nrzimmer/retro-crt/tv/circuits/voltage_waveform_table.md

# Tabela de Tensões e Formas de Onda — A Board

**Fonte:** páginas 47–48 do manual | **Condição:** TV em operação normal, sinal NTSC salvo indicação

> Valores marcados com `*` = sinal (não tensão DC).

## IC001 — TDA12009H (128 pinos)

### Pinos 1–48

| Pino | Sinal | Tensão (V) |
|---|---|---|
| 1 | — | 0 |
| 2 | — | 0 |
| 3 | — | 1.2 |
| 4 | — | 2.6 |
| 5 | — | 3.2 |
| 6 | — | 0 |
| 7 | — | 3.2 |
| 8 | — | 0 |
| 9 | — | 3.1 |
| 10 | — | * |
| 11 | — | * |
| 12 | — | 0 |
| 13 | VGUARD | 0.1 |
| 14 | PH2LF | 2.4 |
| 15 | PH1LF | 4.8 |
| 16 | — | 1.9 |
| 17 | — | 2.1 |
| 18 | — | 0 |
| 19 | — | 2.2 |
| 20 | — | 2.2 |
| 21 | EWD | 3.2 |
| 22 | VD+ | 1.6 |
| 23 | VD− | 1.7 |
| 24 | VIFIN1 | 1.8 |
| 25 | VIFIN2 | 1.5 |
| 26 | — | 2.3 |
| 27 | — | 1.8 |
| 28 | — | 0 |
| 29 | SIFIN1 | 1.8 |
| 30 | SIFIN2 | 1.8 |
| 31 | AGCOUT | 4.6 |
| 32 | EHTO | 0.7 |
| 33 | — | 0 |
| 34 | — | 2.1 |
| 35 | — | 2.1 |
| 36 | OUTL | 3.4 |
| 37 | OUTR | 3.4 |
| 38 | — | 2.0 |
| 39 | MONO_OUTL | 2.4 |
| 40 | — | 0 |
| 41 | PLLIF | 1.8 |
| 42 | — | 2.0 |
| 43 | IFVO | 0.3 |
| 44 | — | 0.3 |
| 45 | VCC8V | 8.3 |
| 46 | — | 1.8 |
| 47 | — | 4.8 |
| 48 | — | 1.1 |

### Pinos 49–87 (entradas de vídeo e saídas RGB)

| Pino | Sinal | Tensão (V) |
|---|---|---|
| 49 | — | 2.1 |
| 50 | — | 2.1 |
| 51 | CVBS2/Y2 | 1.3 |
| 52 | C2 | 1.5 |
| 53 | — | 2.1 |
| 54 | — | 2.1 |
| 55 | CVBS3 | 1.4 |
| 56 | — | 2.1 |
| 57 | — | 2.1 |
| 58 | CVBS1/Y1 | 1.3 |
| 59 | C1 | 1.5 |
| 60 | — | 3.4 |
| 61 | — | 3.4 |
| 62 | — | 3.4 |
| 63 | — | 3.4 |
| 64 | CVBSO | 1.1 |
| 65 | VM | 0.2 |
| 66 | AFC | 0 |
| 67 | HOUT | 4.7 |
| 68 | — | 1.2 |
| 69 | — | 1.2 |
| 70 | — | 1.2 |
| 71 | — | 1.9 |
| 72 | — | 1.6 |
| 73 | — | 0.1 |
| 74 | — | 0 |
| 75 | — | 0.1 |
| 76 | — | 1.1 |
| 77 | — | 1.2 |
| 78 | — | 1.2 |
| 79 | — | 0 |
| 80 | — | 4.7 |
| 81 | — | 3.4 |
| 82 | — | 3.0 |
| 83 | ABL | 1.5 |
| 84 | IK | 1.5 |
| 85 | B OUT | 1.5 |
| 86 | G OUT | 1.4 |
| 87 | R OUT | 1.5 |

### Pinos 88–128 (controle de sistema)

| Pino | Sinal | Tensão (V) |
|---|---|---|
| 88–90 | — | 3.1, 0, 3.1 |
| 91 | — | 1.5 |
| 92 | — | 0 |
| 93 | — | 1.8 |
| 94 | — | 3.1 |
| 95 | — | 0 |
| 96 | — | 1.8 |
| 97 | — | 2.8 |
| 98 | — | 0.3 |
| 99 | — | 3.2 |
| 100 | VDDC2 | 1.6 |
| 101 | VSSC2 | 0 |
| 102 | — | 3.2 |
| 103 | — | 0 |
| 104 | — | 2.2 |
| 105 | — | 0 |
| 106 | — | 0 |
| 107 | — | 3.1 |
| 108 | SCL0 | 3.5 |
| 109 | SDA0 | 3.2 |
| 110 | VDDP (3.3V) | 3.2 |
| 111 | S1/VC | 4.8 |
| 112 | ROT CTRL | 0 |
| 113 | ROT SW | 0 |
| 114 | STBY_SW | 0 |
| 115 | DGC RELAY | 0.1 |
| 116 | — | 1.6 |
| 117 | VDDC1 (1.8V) | 1.6 |
| 118 | — | 3.1 |
| 119 | KEY | 0.2 |
| 120 | S2 | 0 |
| 121 | — | 0 |
| 122 | RED LED | 3.1 |
| 123 | GREEN LED | 1.6 |
| 124 | VDDC3 (1.8V) | 0 |
| 125 | VSSC3 | 3.2 |
| 126 | — | 0.2 |
| 127 | — | 3.2 |
| 128 | — | 3.2 |

---

## Reguladores de tensão

| Ref | Tipo | Pin I (V) | Pin G (V) | Pin O (V) |
|---|---|---|---|---|
| IC602 | KIA78R09API (9V) | 10.4 | 0 | 8.8 |
| IC603 | PQ018EF01SSH (1.8V áudio) | 3.9 | 0 | 1.9 (pin2=3.9, pin3=0, pin4=2.3) |
| IC604 | KIA7805API (5V) | 8.8 | 0 | 4.8 |
| IC605 | SE135N-LF38 (error amp) | 134.4 | 0 | 21.2 |
| IC606 | KIA78D33P1 (3.3V) | 23.6 | 0 | 3.2 |
| IC607 | BA18BC0FP-E2 (1.8V main) | 3.4 | 0 | 1.7 |

---

## IC802 — TJM4558CDT (op-amp EW)

| Pino | Tensão (V) |
|---|---|
| 1 (OUT1) | 3.3 |
| 2 (IN1−) | 2.2 |
| 3 (IN1+) | 6.0 |
| 4 (Vcc) | 8.8 |
| 5 (IN2+) | 2.4 |
| 6 (IN2−) | 3.1 |
| 7 (OUT2) | 3.0 |
| 8 (GND) | 0 |

---

## IC804 — STV9302A (Vertical IC)

| Pino | Sinal | Tensão (V) |
|---|---|---|
| 1 | VSS | −13.5 |
| 2 | IN | pulso |
| 3 | VCC | 13.9 |

---

## IC801 — LM2903DT (Comparador H-center)

| Pino | Tensão (V) |
|---|---|
| 1 | 2.2 |
| 2 | 0.7 |
| 3 | 1.5 |
| 4 | 0 |
| 5–8 | 3.3, 2.2, 6.0, 8.8 |

---

## Transistores — tensões chave

| Ref | Tipo | B (V) | C (V) | E (V) |
|---|---|---|---|---|
| Q001 | UN2211 | 0 | 2.1 | 0 |
| Q006 | UN2216 | 3.2 | 1.9 | 1.9 |
| Q007 | UN2216 | 0 | 3.1 | 0.1 |
| Q008 | 2SC1623 | 0 | 3.3 | 0 |
| Q010 | 2SA1235-F | 0.2 | 0 | 0.9 |
| Q200 | UN2211 | 82.3 | 0 | 0 |
| Q201 | 2SA1235-F | 4.5 | 8.8 | 3.9 |
| Q202 | 2SA1235-F | 1.9 | 0 | 0 |
| Q206 | UN2216 | 23.6 | 24.3 | 24.4 |
| Q803 | 2SC3209LK | 133.4 | 70.6 | 0 |
| Q804 | KTA1279 | 133.8 | 0 | (0) |
| Q805 | 2SC5885 | — | 137.6 (DC) | — |
| Q806 | 2SC1623 | 0 | 4.9 | 9.3 (NTSC: 9.9) |
| Q807 | 2SA1235-F | 1.1 | 0 | 0.1 |
| Q808 | IRF614-037 | G=0.1 | D=0 | S=1.8 |
| Q814 | 2SC1623 | 0 | 6.1 | 8.8 |
| Q900 | 2SA1235-F | 5.8 | 6.1 | 0 |
| Q901 | UN2216 | 5.8 | 0 | 5.6 |

---

## Formas de onda (condição NTSC salvo indicação)

| Ref | Local / sinal | Amplitude (Vpp) |
|---|---|---|
| 1 | — | 1.960 |
| 2 | VD+ drive vertical | 5.360 |
| 3 | VD− drive vertical | 3.440 |
| 4 | — | 1.800 |
| 5 | — | 2.480 |
| 6 | — | 1.120 |
| 7 | — | 1.840 |
| 8 | IC200 (áudio out) | 1.680 |
| 9 | — | 4 NTSC — 2.480 |
| 10 | — | 5 NTSC — varia |
| 11 | — | 660.0 mVpp |
| 12 | Estágio H (IC001 zona) | 132.0 |
| 13 | — | 700.0 mVpp |
| 14 | Saída vertical IC804 | 1.400 |
| 15 | DY800 yoke H | 28.80 |
| 16 | Q806 MIXER EW | 9.200 |
| 17 | Saída vertical (alt) | 1.340 |

---

## Deflection Yoke DY800 — tensões DC nas bobinas

| Pino | Tensão (V) |
|---|---|
| 1 (H.DY+) | 196.0 |
| 2 (H.DY−) | 196.2 |
| 3 (H.DY ref) | 196.6 |
| 4 (V.DY+) | 0.5 |
| 5 (V.DY−) | 0.1 |

---

## IC601 — Controlador SMPS (seleção)

| Pino | Tensão (V) |
|---|---|
| 1 | (12.6) [12.7] |
| 2 | 0 |
| 3 | 23.0 |
| 4–6 | 0, 0, 0 |
| 7 | 11.3 |
| 8 | 0.8 |
| 9 | 0 |
| 10 | 24.2 |
| 11 | 10.2 |
| 12 | 11.3 |
| 13 | 1.4 |
| 14 | 12.4 |
| 15 | 154.9 |
| 16 | 0 |
| 17 | 0.2 |
