nrzimmer/retro-crt/scart/cables/README.md

# Cabos SCART por Console

Pinagens e diagramas de fiação. Voltar para [`scart/README.md`](../README.md) para componentes comuns e avisos.

| Arquivo | Console | Conector | Obs |
|---|---|---|-----|
| [nes.md](nes.md) | NES / Famicom | MultiAV (via NESRGB) | Requer mod — ver [`consoles/nes/`](../../consoles/nes/) |
| [snes.md](snes.md) | Super Nintendo | MultiAV 12P card-edge | RGB nativo (exceto SNES Mini) |
| [n64.md](n64.md) | Nintendo 64 | MultiAV 12P | Requer mod — ver [`consoles/n64/`](../../consoles/n64/) |
| [megadrive.md](megadrive.md) | Sega Mega Drive 1/2 | DIN-8U / mini-DIN 9 | RGB nativo |
| [ps1.md](ps1.md) | PlayStation 1 | Proprietário 12P | RGB nativo |
| [ps2.md](ps2.md) | PlayStation 2 | Proprietário 12P | RGB nativo; atenção ao 480p |
| [saturn.md](saturn.md) | Sega Saturn | mini-DIN 10 | Componentes obrigatórios no sync |
| [neogeo.md](neogeo.md) | SNK Neo Geo AES/MVS | DIN-8C | RGB nativo |
