nrzimmer/retro-crt/consoles/megadrive/README.md

# Sega Mega Drive / Genesis — Mods

---

## Mod Stereo (MD1)

Mega Drive 1 tem apenas saída de áudio mono pelo DIN-8. Para stereo:

**Opção 1 — Jack de fone frontal:**  
MD1 tem jack 3.5mm na frente com stereo — capturar dali em vez do DIN-8.

**Opção 2 — Mod interno:**  
Separar os canais L e R do gerador de som (YM2612 / SN76489) internamente e adicionar conector.

Mega Drive 2 já tem stereo nativo pelo mini-DIN 9 (pinos 8 e 9).

---

## Referências

- [Genesis Stereo Audio Mod — RetroRGB](https://retrorgb.com/genesisaudio.html)
