nrzimmer/retro-crt/tv/manual/rev_brazil/pages/page-18.md

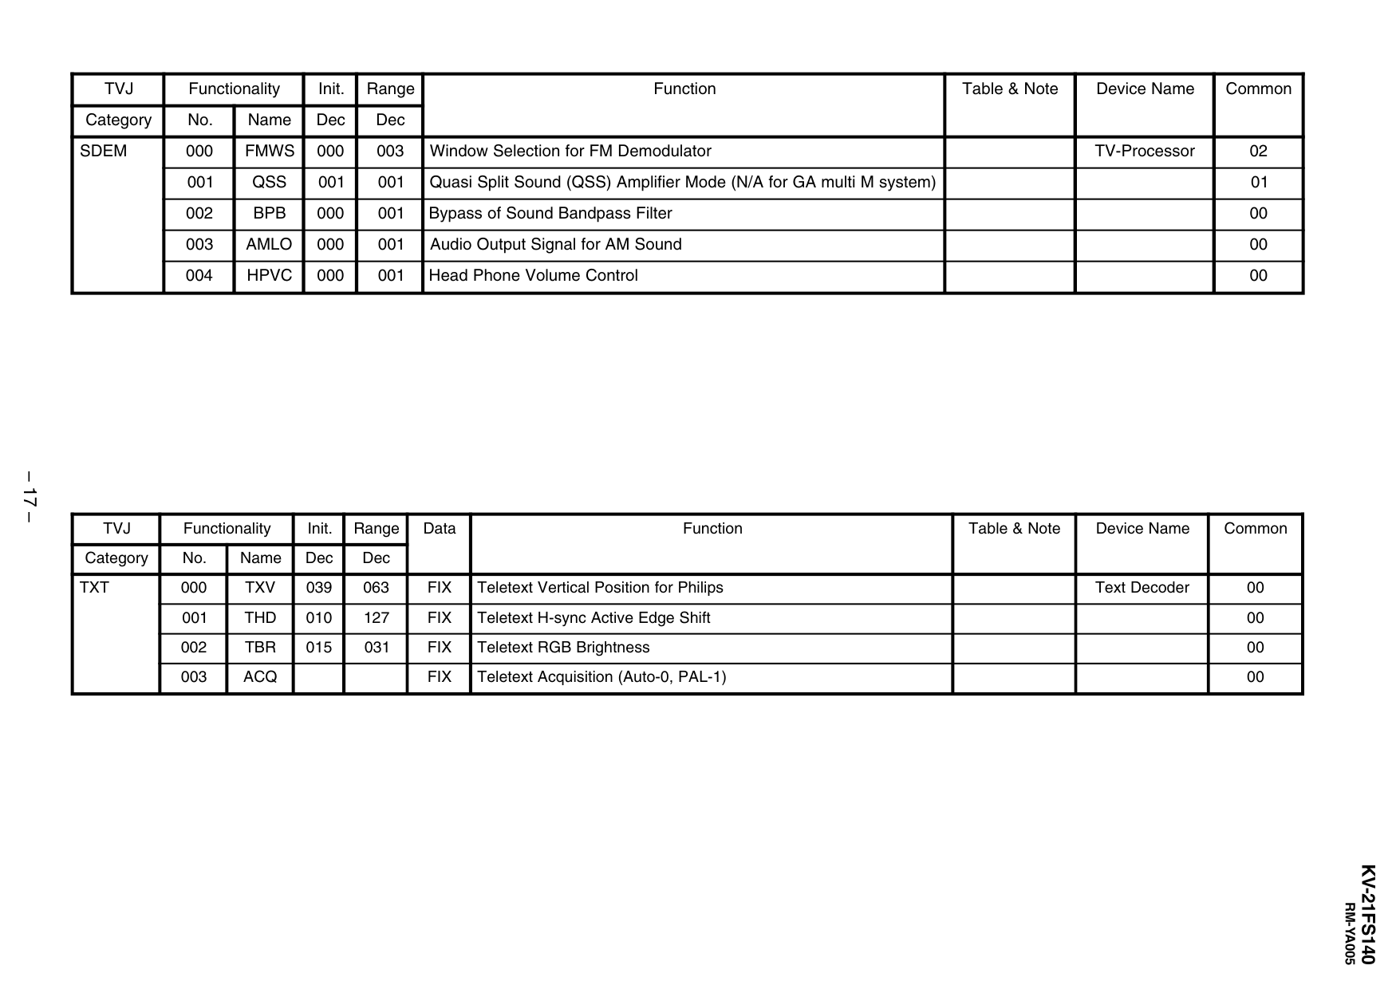
[picture p14: tv/manual/rev_brazil/pages/img/page-18.png]
page-18


TVJ

Functionality

Init.

Range

Category

No.

Name

Dec

Dec

SDEM

000

FMWS

000

003

Window Selection for FM Demodulator

001

QSS

001

001

Quasi Split Sound (QSS) Amplifier Mode (N/A for GA multi M system)

01

002

BPB

000

001

Bypass of Sound Bandpass Filter

00

003

AMLO

000

001

Audio Output Signal for AM Sound

00

004

HPVC

000

001

Head Phone Volume Control

00

Function

Table & Note

Device Name

Common

TV-Processor

02

– 17 –
TVJ

Functionality

Init.

Range

Category

No.

Name

Dec

Dec

TXT

000

TXV

039

063

FIX

Teletext Vertical Position for Philips

001

THD

010

127

FIX

Teletext H-sync Active Edge Shift

00

002

TBR

015

031

FIX

Teletext RGB Brightness

00

003

ACQ

FIX

Teletext Acquisition (Auto-0, PAL-1)

00

Data

Function

Table & Note

Device Name

Common

Text Decoder

00

RM-YA005

KV-21FS140
