nrzimmer/retro-crt/tv/manual/rev_brazil/pages/page-23.md

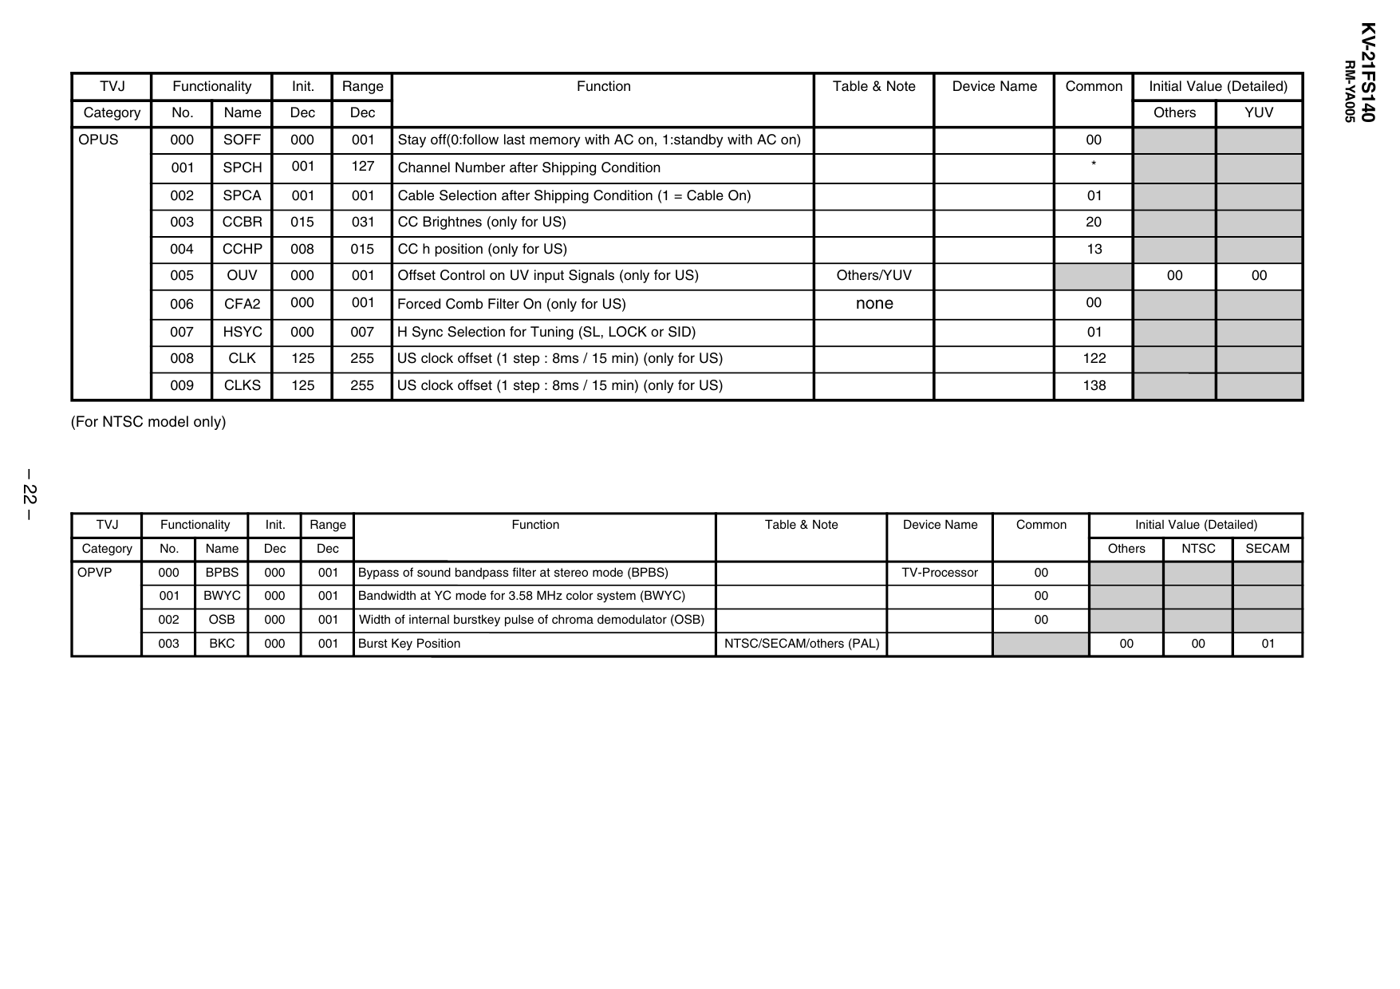
[picture p18: tv/manual/rev_brazil/pages/img/page-23.png]
page-23


Init.

Range

Category

No.

Name

Dec

Dec

OPUS

000

SOFF

000

001

Stay off(0:follow last memory with AC on, 1:standby with AC on)

00

001

SPCH

001

127

Channel Number after Shipping Condition

*

002

SPCA

001

001

Cable Selection after Shipping Condition (1 = Cable On)

01

003

CCBR

015

031

CC Brightnes (only for US)

20

004

CCHP

008

015

CC h position (only for US)

13

005

OUV

000

001

Offset Control on UV input Signals (only for US)

006

CFA2

000

001

Forced Comb Filter On (only for US)

007

HSYC

000

007

H Sync Selection for Tuning (SL, LOCK or SID)

01

008

CLK

125

255

US clock offset (1 step : 8ms / 15 min) (only for US)

122

009

CLKS

125

255

US clock offset (1 step : 8ms / 15 min) (only for US)

138

Function

Table & Note

Device Name

Common

Initial Value (Detailed)

Others/YUV

Others

YUV

00

00

00

none

(For NTSC model only)

– 22 –
TVJ

Functionality

Init.

Range

Category

No.

Name

Dec

Dec

OPVP

000

BPBS

000

001

Bypass of sound bandpass filter at stereo mode (BPBS)

Function

Table & Note

Device Name

Common

TV-Processor

00

001

BWYC

000

001

Bandwidth at YC mode for 3.58 MHz color system (BWYC)

00

002

OSB

000

001

Width of internal burstkey pulse of chroma demodulator (OSB)

00

003

BKC

000

001

Burst Key Position

NTSC/SECAM/others (PAL)

Initial Value (Detailed)
Others

NTSC

SECAM

00

00

01

RM-YA005

Functionality

KV-21FS140

TVJ
