nrzimmer/retro-crt/tv/manual/rev_brazil/pages/page-36.md

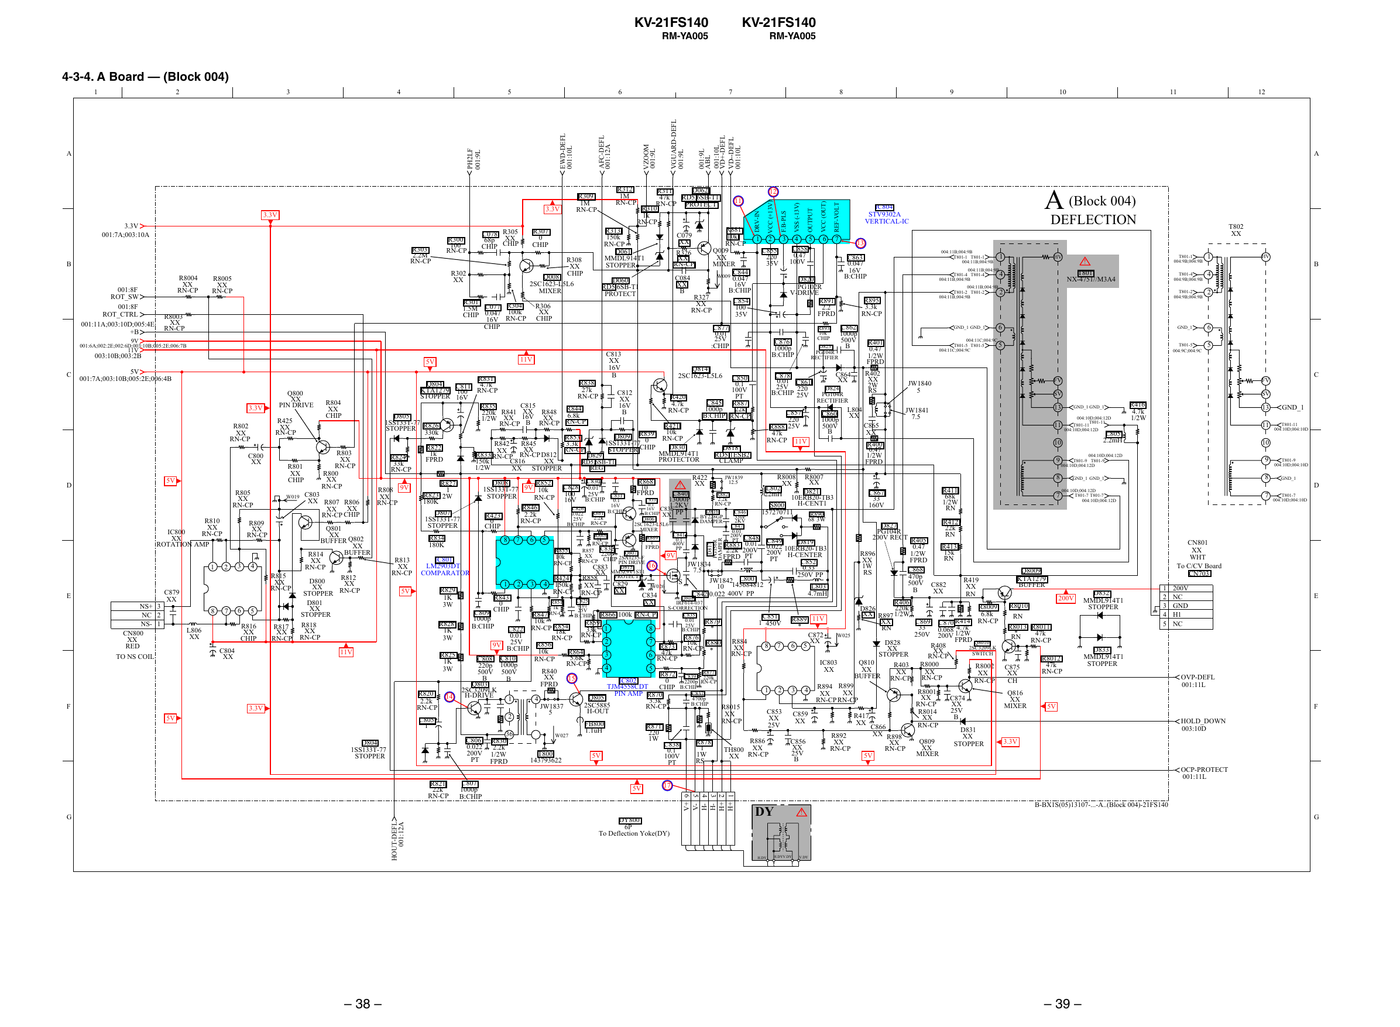
[picture p27: tv/manual/rev_brazil/pages/img/page-36.png]
page-36


KV-21FS140

KV-21FS140

RM-YA005

RM-YA005

4-3-4. A Board — (Block 004)
6

R303
2.2M
RN-CP

B

R308
XX
CHIP

R302
XX

R8005
XX
RN-CP

Q008
2SC1623-L5L6
MIXER

R301
1.5M C077 R304
100k
CHIP 0.047 RN-CP
16V
CHIP

R8003
XX
RN-CP

D060
RD5.6SB-T1
PROTECT

R306
XX
CHIP

C877
0.01
25V
:CHIP

001:6A;002:2E;002:6D;003:10B;005:2E;006:7B

11V

C

11V

5V

5V
001:7A;003:10B;005:2E;006:4B

3.3V

R425
XX
RN-CP

R802
XX
RN-CP
C800
XX
5V

D

R805
XX
RN-CP
R810
XX
IC800
RN-CP
XX
ROTATION AMP
1

NS+ 3
NC 2
NS- 1
CN800
XX
RED

2

3

7

6

5

C804
XX

F

3.3V
5V

R803
XX
RN-CP
R800
XX
RN-CP

R817
XX
RN-CP

REF-VOLT

VCC (OUT)

OUTPUT

F.B-PLS

VSS (-13V)

C862
R893
10k
1000p
CHIP
500V
B
D823
PG104R
RECTIFIER

C876
1000p
B:CHIP

C813
XX
16V
B

Q814
2SC1623-L5L6 C850
R831
R838
0.1
Q804
C811 4.7k
27k
100V
KTA1279 100 RN-CP
C812
RN-CP
PT
STOPPER 16V
R420
XX
C845
R887
4.7k
C815
16V
R835
R844
1000p
22k
RN-CP
B
220k R841 XX R848
6.8k
B:CHIP RN-CP
D805
1/2W XX 16V XX
RN-CP
1SS133T-77 R826
RN-CP B RN-CP
R421
STOPPER
10k
330k
D809 R839 RN-CP
R853
1SS133T-77 0
R842
3.3k
R845
D830
R822
D818
RN-CP
XX
STOPPER CHIP
XX
MMDL914T1
1k
R833 RN-CP RN-CP D812
RD5.1ESB2
D829
R824
PROTECTOR
FPRD
CLAMP
XX
150k
C816
RD5.6SB-T1
33k
1/2W
REG
XX STOPPER
RN-CP
JW1839
R422
C830
R868
12.5
R852
D808
R827
XX
!
C828 0.01
10
1SS133T-77 9V 10k
1
R808 9V
FPRD
C840
100
R882
25V
R823 2W
STOPPER
XX
RN-CP 16V B:CHIP C831
2.2k
C833
13000P
0.1
180K
RN-CP
RN-CP
0.1
1.2KV
16V
R846
C826
16V C836
D816
C846
B:CHIP XX PP
R861 B:CHIP
D807
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

PH2LF
001:9L

A

7

VCC (+13V)

5

4

3

EWD-DEFL
001:10L

2

1

0.01
200V
PT C848

CN801
XX
WHT
To C/CV Board
CN703
D832
MMDL914T1
STOPPER

1
2
3
4
5

200V
NC
GND
H1
NC

E

D833
MMDL914T1
STOPPER
OVP-DEFL
001:11L
F
HOLD_DOWN
003:10D

OCP-PROTECT
001:11L
5V

17

V+
VHHH+
H+

C807
1000p
B:CHIP

1
2
3
4
5
6

R821
22k
RN-CP

HOUT-DEFL
001:12A

G

– 38 –

DY800
6P
To Deflection Yoke(DY)

DY

H.DY

H.DYV.DY

B-BX1S(05)13107-...-A..(Block 004)-21FS140
!

G

V.DY

– 39 –
