nrzimmer/retro-crt/tv/manual/rev_brazil/pages/page-38.md

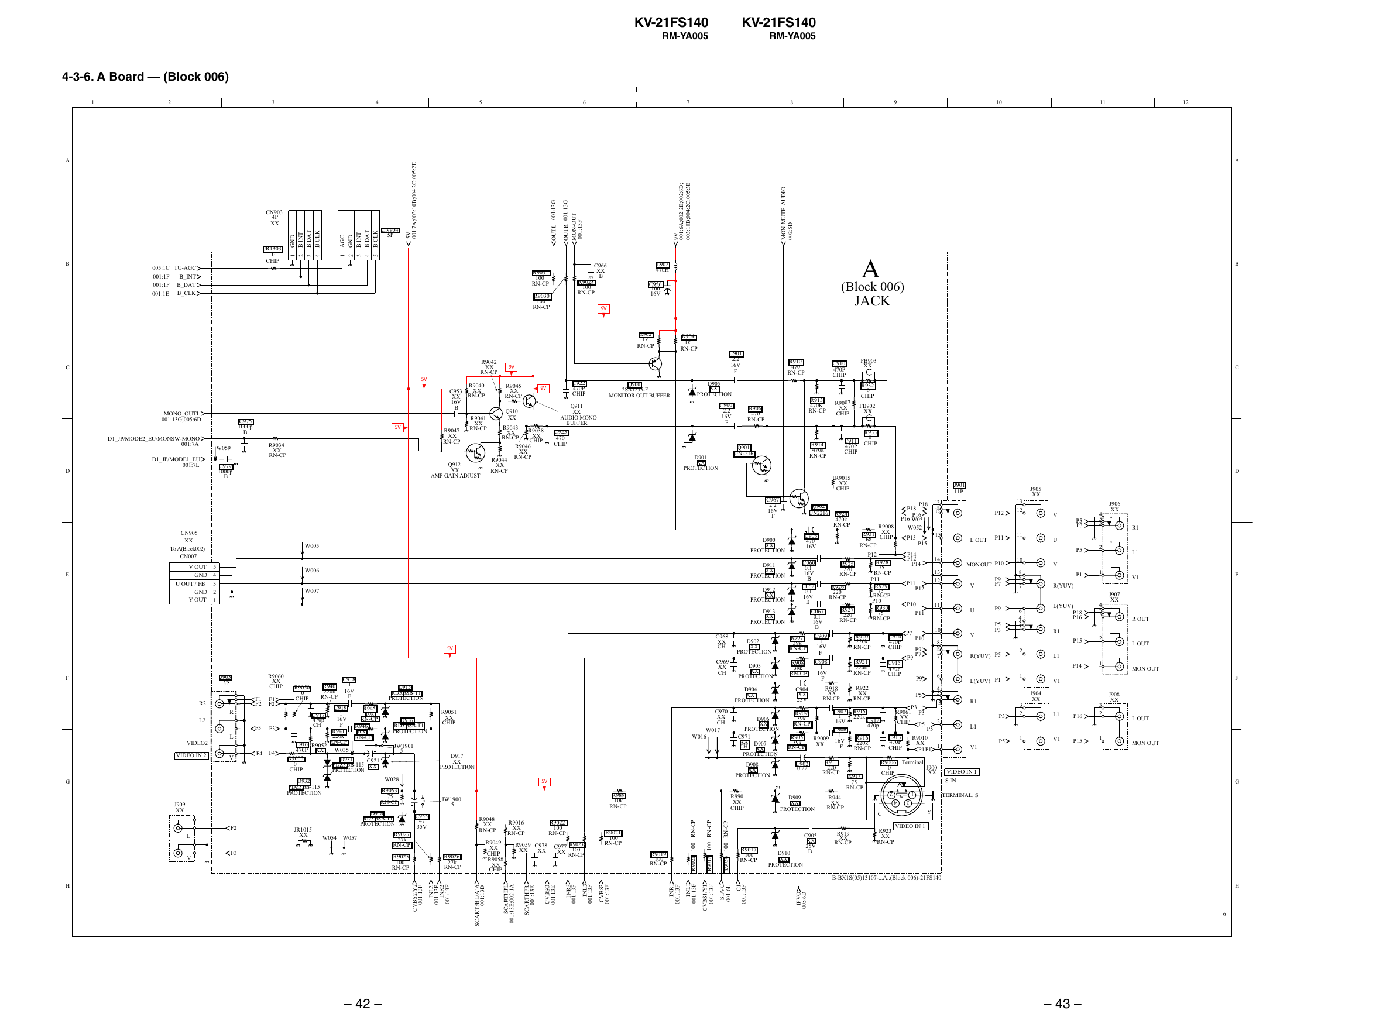
[picture p29: tv/manual/rev_brazil/pages/img/page-38.png]
page-38


KV-21FS140

KV-21FS140

RM-YA005

RM-YA005

7

8

4-3-6. A Board — (Block 006)
5

4

B

001:1F
001:1F
001:1E

R9028
100
RN-CP

R9030
100
RN-CP

R9042
XX
RN-CP

C

R9040
XX
C953
XX RN-CP
16V
B
C975
1000p
B

D1_JP/MODE2_EU/MONSW-MONO
001:7A

5V

W059

D1_JP/MODE1_EU
001:7L

R9047
XX
RN-CP

R9034
XX
RN-CP

Q912
XX
AMP GAIN ADJUST

C979
1000p
B

D

R904
1k
RN-CP

C901
2.2
16V
F

9V
R9045
XX
RN-CP

R9041
XX
RN-CP

MON-MUTE-AUDIO
002:5D

JACK

9V

5V

C922
470P
CHIP

9V

R9043
R9038
XX
XX
RN-CP
CHIP
R9046
XX
RN-CP
R9044
XX
RN-CP

R910
470
RN-CP

C900
2.2
16V
F

C925
470
CHIP

R906
470
RN-CP

D901
XX
PROTECTION

E

V OUT
GND
U OUT / FB
GND
Y OUT

Q902
UN2216

D911
XX
PROTECTION
D912
XX
PROTECTION

W007

C968
XX
CH

5V

F3

F4

F4

L
VIDEO2
VIDEO IN 2

V

C919
R945
10k
1
C917
RN-CP
16V
470p
F
CH
R946
R941
10k
220k
RN-CP
C916 R9052 RN-CP
W035
470P XX
R9005
D931
C921
0
PDZ3.6B-115 XX
CHIP
PROTECTION

L

V

D917
XX
PROTECTION

D918
RD5.6SB-T1
PROTECTION
JR1015
XX

W054

D906
XX
PROTECTION
C971
XX D907
CH XX
PROTECTION

JW1901
5

W057

F3

R926
220
RN-CP

C067
0.1
16V
B
C909
R907
1
39k
16V
RN-CP
F
C908
R908
1
39k
16V
RN-CP
F

R927
220
RN-CP

R920
220k
RN-CP

R918
XX
RN-CP

R922
XX
RN-CP

R909
39k
RN-CP

C907
1
16V
C906
1
R9009 16V
XX
F

R915
220k

C902
0.22

R911
220
RN-CP

R989
10k
RN-CP

JW1900
5
C955
47
35V

R9048
XX
RN-CP

R9027
27k
RN-CP

R9049
XX
CHIP
R9058
XX
CHIP

R9026
27k
RN-CP

R9025
100
RN-CP

R9016
XX
RN-CP

R9022
100
RN-CP

R9059 C978
XX
XX

C977 R9023
XX 100
RN-CP

R990
XX
CHIP

R9021
100
RN-CP
R9019
100
RN-CP

R9017
100
RN-CP

D909
XX
PROTECTION

D910
XX
PROTECTION

C905
XX
25V
B

R917
75
RN-CP

15

P14
P12
P14

13
12

P12

13
12

P5
P3

4
5
3

P5

2

P1

1

L(YUV)
P18
P16

4
5
3

V

11

P11
P7

P9

10
P10

7
6

P9

C913
470P
CHIP

11

U

P9

6
4
5
3

L1

Y

8
P9
P7

9

V

R1

U

10

E

V1

R(YUV)

7

P5
P3

R(YUV) P5

L(YUV) P1

3

2

P3
2
P5

L1

R9010
XX
1
P1 P1

V1

P15

2

P14

1

P5

L OUT

L1

1

MON OUT
F

V1
J904
XX

R1

R OUT

R1

Y

4
5

R9006 Terminal
J900
0
XX
CHIP

3
2

L1

P16

1

V1

P15

3
2

1

J908
XX
L OUT

MON OUT

VIDEO IN 1
S IN

G

TERMINAL, S
Y

C
R923
XX
RN-CP

MON OUT P10

8
9

P9
P7

P5

C912
470p

L OUT

P11

J906
XX

J907
XX

P10

P3
R9061 P3
XX
CHIP P5

R944
XX
RN-CP

R919
XX
RN-CP

14

P11
P12

C915
470P
CHIP

R916
220k
RN-CP

17
18
16

P15

C914
470P
CHIP

R921
220k
RN-CP

J905
XX

W052
P15

P12
R928
75
RN-CP
P11
R929
75
RN-CP
P10
R930
75
RN-CP

C904
XX
25V

R905
39k
RN-CP

D908
XX
PROTECTION

R9008
R931 XX
68 CHIP
RN-CP

R925
220
RN-CP

5V

R9053
75
RN-CP

J909
XX
F2

C970
XX
CH
W017
W016

R9051
XX
CHIP

W028

D932
PDZ3.6B-115
PROTECTION

G

D916
RD5.6SB-T1
PROTECTION

D904
XX
PROTECTION

P18
P18
P16
P16 W051

R924
470k
RN-CP

2

F3

D915
RD5.6SB-T1
PROTECTION

C060
0.1
16V
B
C062
0.1
16V
B

1

L2

D903
XX
PROTECTION

R9036 100 RN-CP

F1
F2

R

R9050
0
CHIP

R9020 100 RN-CP

F1
F2

R2

C969
XX
CH
C918
1
R940
220k 16V
F
RN-CP

R9018 100 RN-CP

R9060
XX
CHIP

D902
XX
PROTECTION

J901
11P

C903
470
16V

D900
XX
PROTECTION

W006

J903
3P

R933
0
CHIP

C911
470P
CHIP

D

D913
XX
PROTECTION

F

FB902
XX

R9015
XX
CHIP

W005

5
4
3
2
1

R9007
XX
CHIP

R914
470k
RN-CP

Q901
UN2216

C

R932
0
CHIP

R913
470K
RN-CP

C967
2.2
16V
F
CN905
XX
To A(Block002)
CN007

FB903
XX

C910
470P
CHIP

D905
XX
PROTECTION

Q900
2SA1235-F
MONITOR OUT BUFFER

Q911
XX
AUDIO MONO
BUFFER

Q910
XX

B

(Block 006)

C956
100
16V

R902
1k
RN-CP

MONO_OUTL
001:13G;005:6D

12

A

L902
47uH

C966
XX
B

R9031
100
RN-CP

B_INT
B_DAT
B_CLK

9V
001:6A;002:2E;002:6D;
003:10B;004:2C;005:3E

OUTL 001:13G

005:1C TU-AGC

OUTR 001:13G
MON-OUT
001:13F

AGC
GND
B INT
B DAT
B CLK
1
2
3
4
5

CN904
5P

11

10

A

5V
001:7A;003:10B;004:2C;005:2E

GND
B INT
B DAT
B CLK

JR1903
0
CHIP

1
2
3
4

CN903
4P
XX

9

2

A

6

4

3

3

2

1

1

VIDEO IN 1

H

IFVO
005:6D

C1
001:13F

S1/VC
001:6L

CVBS1/Y1
001:13F

INL1
001:13F

INR1
001:13F

CVBS3
001:13F

INL3
001:13F

INR3
001:13F

CVBSO
001:13E

SCARTHPR
001:13E

SCARTHPL
001:13E;002:1A

SCARTFBL/A16
001:13D

CVBS2/Y2
001:13F

– 42 –

INL2
001:13F
INR2
001:13F

B-BX1S(05)13107-...A..(Block 006)-21FS140
H

6

– 43 –
