nrzimmer/retro-crt/tv/manual/rev_brazil/pages/page-42.md

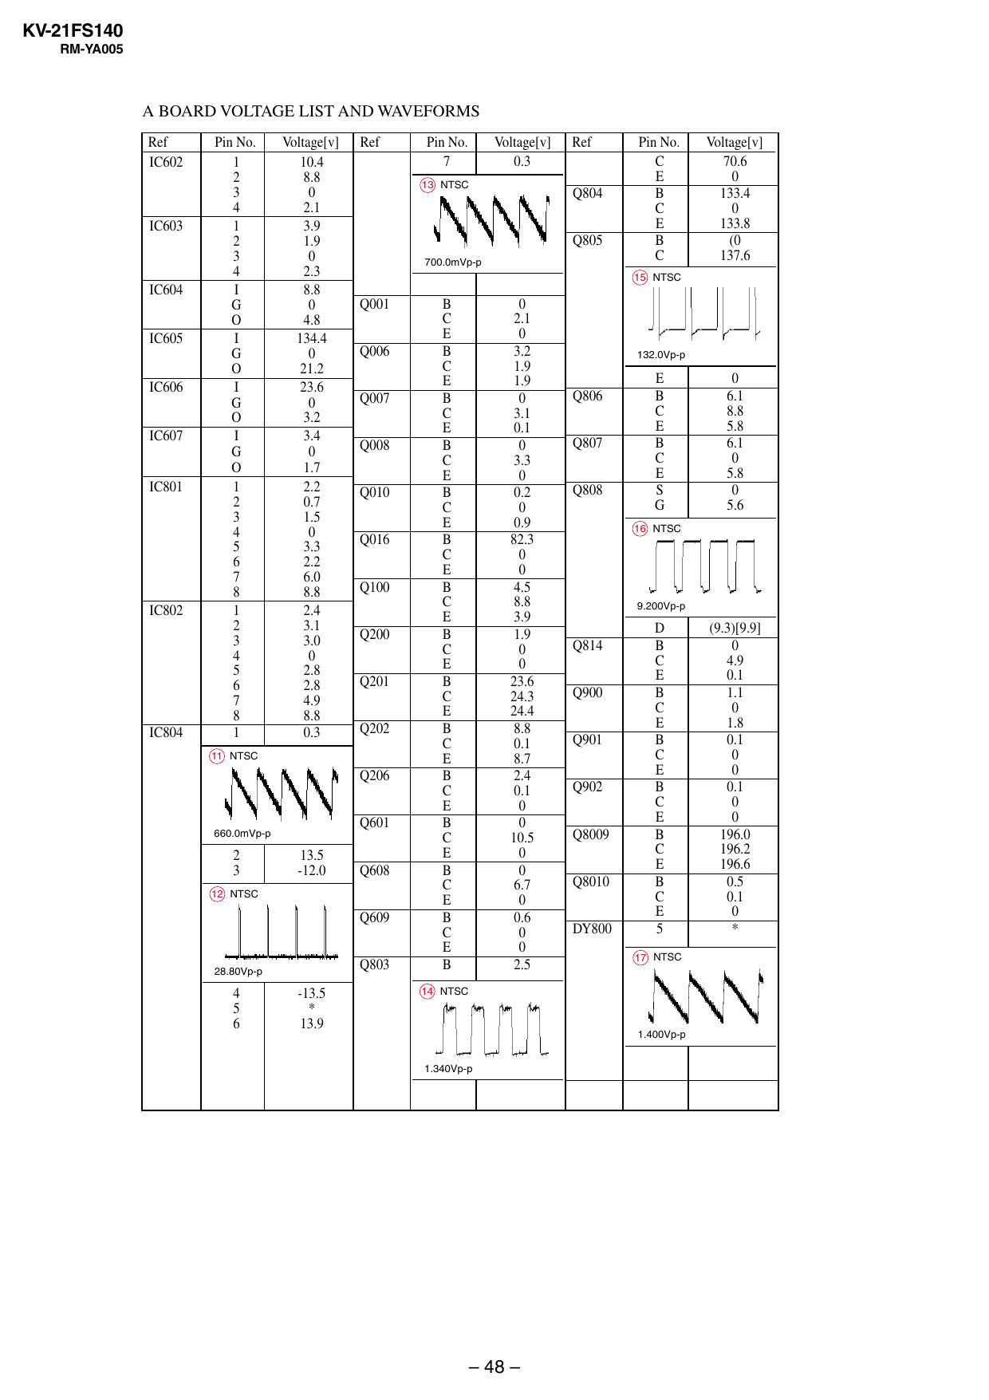
[picture p33: tv/manual/rev_brazil/pages/img/page-42.png]
page-42


KV-21FS140
RM-YA005

A BOARD VOLTAGE LIST AND WAVEFORMS
Ref
IC602

IC603

IC604
IC605
IC606
IC607
IC801

IC802

IC804

Pin No.
1
2
3
4
1
2
3
4
I
G
O
I
G
O
I
G
O
I
G
O
1
2
3
4
5
6
7
8
1
2
3
4
5
6
7
8
1

Voltage[v]
10.4
8.8
0
2.1
3.9
1.9
0
2.3
8.8
0
4.8
134.4
0
21.2
23.6
0
3.2
3.4
0
1.7
2.2
0.7
1.5
0
3.3
2.2
6.0
8.8
2.4
3.1
3.0
0
2.8
2.8
4.9
8.8
0.3

Ref

Q001
Q006
Q007
Q008
Q010
Q016
Q100
Q200
Q201
Q202

Q608
Q609

4
5
6

Q803
-13.5
*
13.9

Pin No.
C
E
B
C
E
B
C

Voltage[v]
70.6
0
133.4
0
133.8
(0
137.6

15 NTSC

12 NTSC

28.80Vp-p

Q804
Q805

Q601
13.5
-12.0

Ref

700.0mVp-p

Q206

2
3

Voltage[v]
0.3

13 NTSC

11 NTSC

660.0mVp-p

Pin No.
7

B
C
E
B
C
E
B
C
E
B
C
E
B
C
E
B
C
E
B
C
E
B
C
E
B
C
E
B
C
E
B
C
E
B
C
E
B
C
E
B
C
E
B

0
2.1
0
3.2
1.9
1.9
0
3.1
0.1
0
3.3
0
0.2
0
0.9
82.3
0
0
4.5
8.8
3.9
1.9
0
0
23.6
24.3
24.4
8.8
0.1
8.7
2.4
0.1
0
0
10.5
0
0
6.7
0
0.6
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

132.0Vp-p

Q806
Q807
Q808

E
B
C
E
B
C
E
S
G
16 NTSC

9.200Vp-p

Q814
Q900
Q901
Q902
Q8009
Q8010
DY800

D
B
C
E
B
C
E
B
C
E
B
C
E
B
C
E
B
C
E
5
17 NTSC

14 NTSC

1.400Vp-p
1.340Vp-p

– 48 –

0
6.1
8.8
5.8
6.1
0
5.8
0
5.6

(9.3)[9.9]
0
4.9
0.1
1.1
0
1.8
0.1
0
0
0.1
0
0
196.0
196.2
196.6
0.5
0.1
0
*
