nrzimmer/retro-crt/tv/manual/rev_brazil/pages/page-44.md

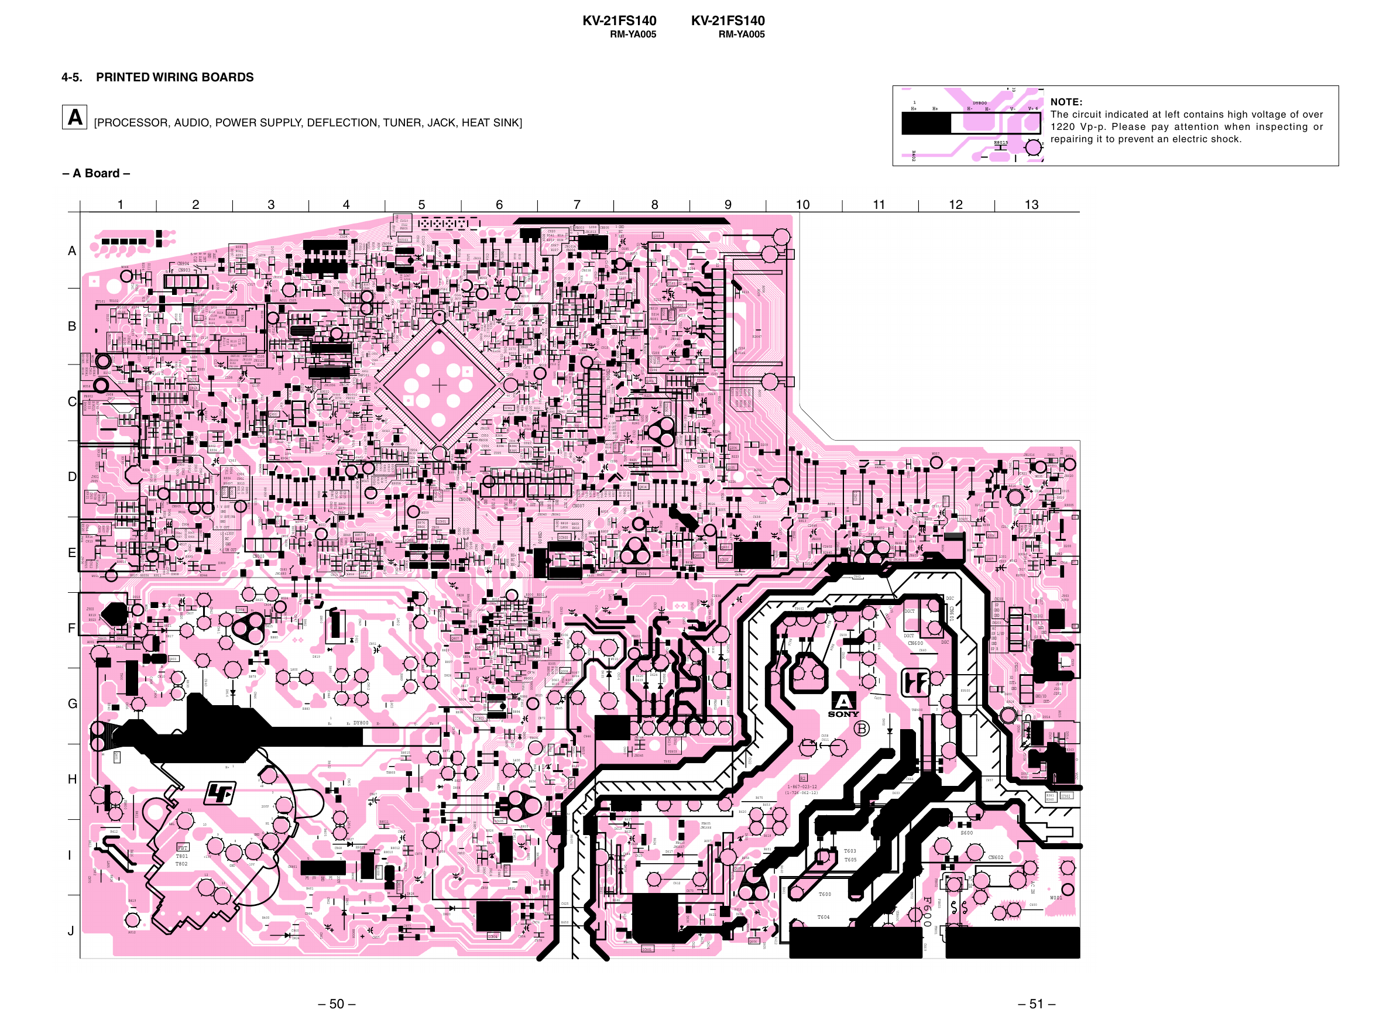
[picture p35: tv/manual/rev_brazil/pages/img/page-44.png]
page-44


4-5.

KV-21FS140

KV-21FS140

RM-YA005

RM-YA005

PRINTED WIRING BOARDS
NOTE:
The circuit indicated at left contains high voltage of over
1220 Vp-p. Please pay attention when inspecting or
repairing it to prevent an electric shock.

A [PROCESSOR, AUDIO, POWER SUPPLY, DEFLECTION, TUNER, JACK, HEAT SINK]
– A Board –

4

5
FB006

C231
R215

12

R216
C213

A008
A009

Q016

Q206

C210

C232

JR300

R232
C208
C206
C219

1

JR018
D202

R222

R200 C201

7

C241

D635
D205

R229

C632

R225

D209

Q204

R228

C675

A002

W057

R223

JR1016

D917

R227

Q205

R8005

C921

R609

IC607
R098

1
C009

C657

VCC

C666

O

C008

R633

R822

(1-726-062-12)

R672

FB800

D055
R362

D603

R361
R360

2

5

C623

T603
T605

R658

CN602

R660

D618

D615

FH603

W001
C600

FH601

C669

Q606

D605

D614

IC601

C616

FB601

C621

C878

T604

R612

C854

R623

R8008

C861

IC804

R650

PS604

C876

1

VDR600

6
7

R621

D636

C877

C844

C619

R400

2

T600

E
R618
D608

F600

R8007

D823

C862

B
C625

AC IN

C673

C602

R661

E

R645

R891

AC IN

FH602

R659

C863
R893

C845

D818

Q804

D830

Q605

R646

C857

S600

R619

R651

R895

D820

– 50 –

D633

R624

4

PH600

R831

C644

A007

FB610
JW1667
D617

C612
C858
D828

C864

D824

C855

Q8010

R401

C860

R888

C866

Q8009

R8013

B

B

200V

R406

NC

H1
NC

GND

C870

13

R419

A012

C850

FB605
JW1666
R625
C624

R833

C875

1

CN801

12

R414

C882

L805

-13V

A006

B

5
GND

R8012
R8010

E

R416

+13V

R824
R8009

D619

1

D827
C868

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

R155
C141

TU102

IC003

R131

R096

1
C120

L044
L032
C1329
C002

R004

L008

JR1010

TU101

R006
R393
R002
C001
C003
D002

D003

R099
R001
R003

R097

AGC

D111
R154

CN904
CN903

5

B CLK

5

W064

GND

B INT
B DAT

A

1

A

7
L039

FB007

C324

6

C1019
C022
FB005

O

3

I

2

3

1

– 51 –
