nrzimmer/retro-crt/tv/manual/rev_brazil/pages/page-45.md

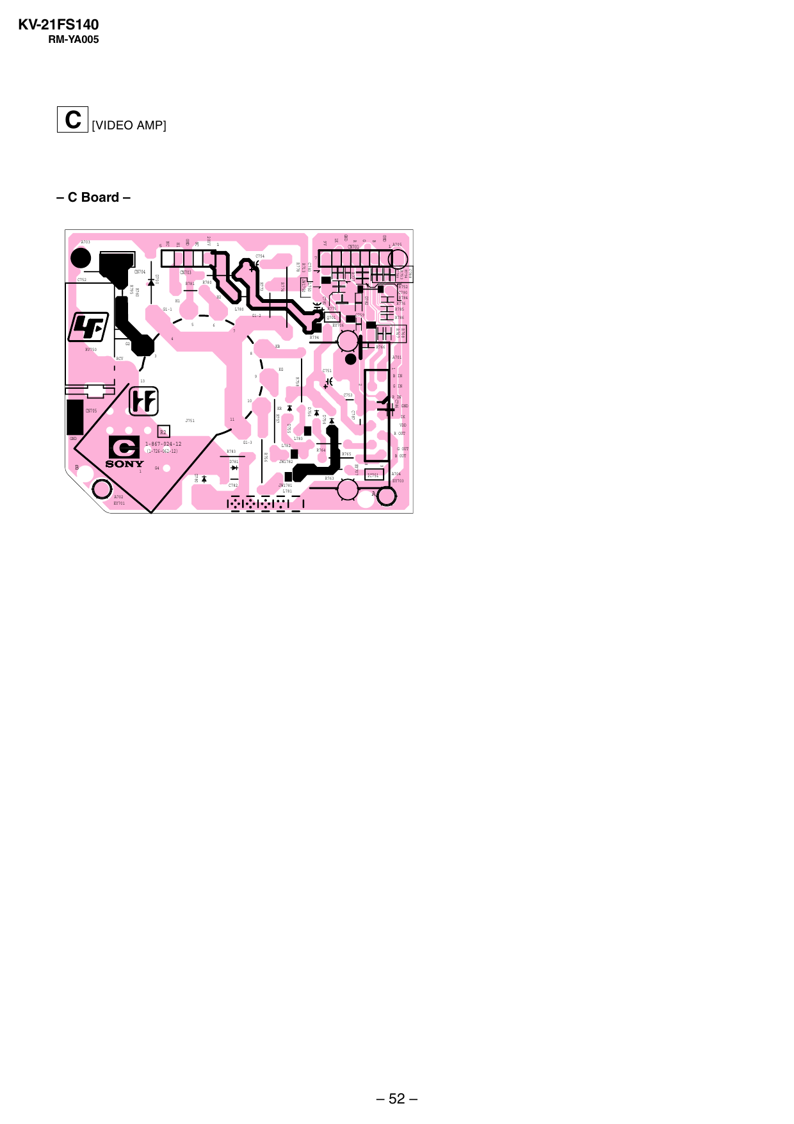
[picture p36: tv/manual/rev_brazil/pages/img/page-45.png]
page-45


KV-21FS140
RM-YA005

C [VIDEO AMP]
– C Board –
GND

B

R

G

1 A705

CN701

7

R777

R774

L750
JW1750

R780

R773

H2

G1-1

R775

L780
G1-2
5

R752
C790
R784
R776
R785

D782

C781

R760
R795

R781

H1

C788
R754
R753
C789

C783
R713
R778

CN703

D750

CN704

GND

1
C754

C752

1K

9V

200V

H1

NC

GND

5

NC

A703

C759

Q701

6

R786

EY706

R768
R767

7
R794

4
G2

KB

RV750
3

RCV

R766

8

A701

1

KG

C751

B IN

13

2

R758

9

G IN

C753

R IN

C786

10

D755

R2
GND
R783

R763
C782

A702
EY701

JW1781
L781

G OUT
R765

B OUT

9

G4

D780

1

JW1782

EY707

B

R764

8

D781

R OUT

L782

R756

(1-726-062-12)

GND
IK
VDD

L783

G1-3

1-867-024-12

C787

11

D754

R757

J751

D756

KR

CN705

IC751

A704
EY703

A

– 52 –
