nrzimmer/retro-crt/tv/manual/rev_brazil/pages/page-50.md

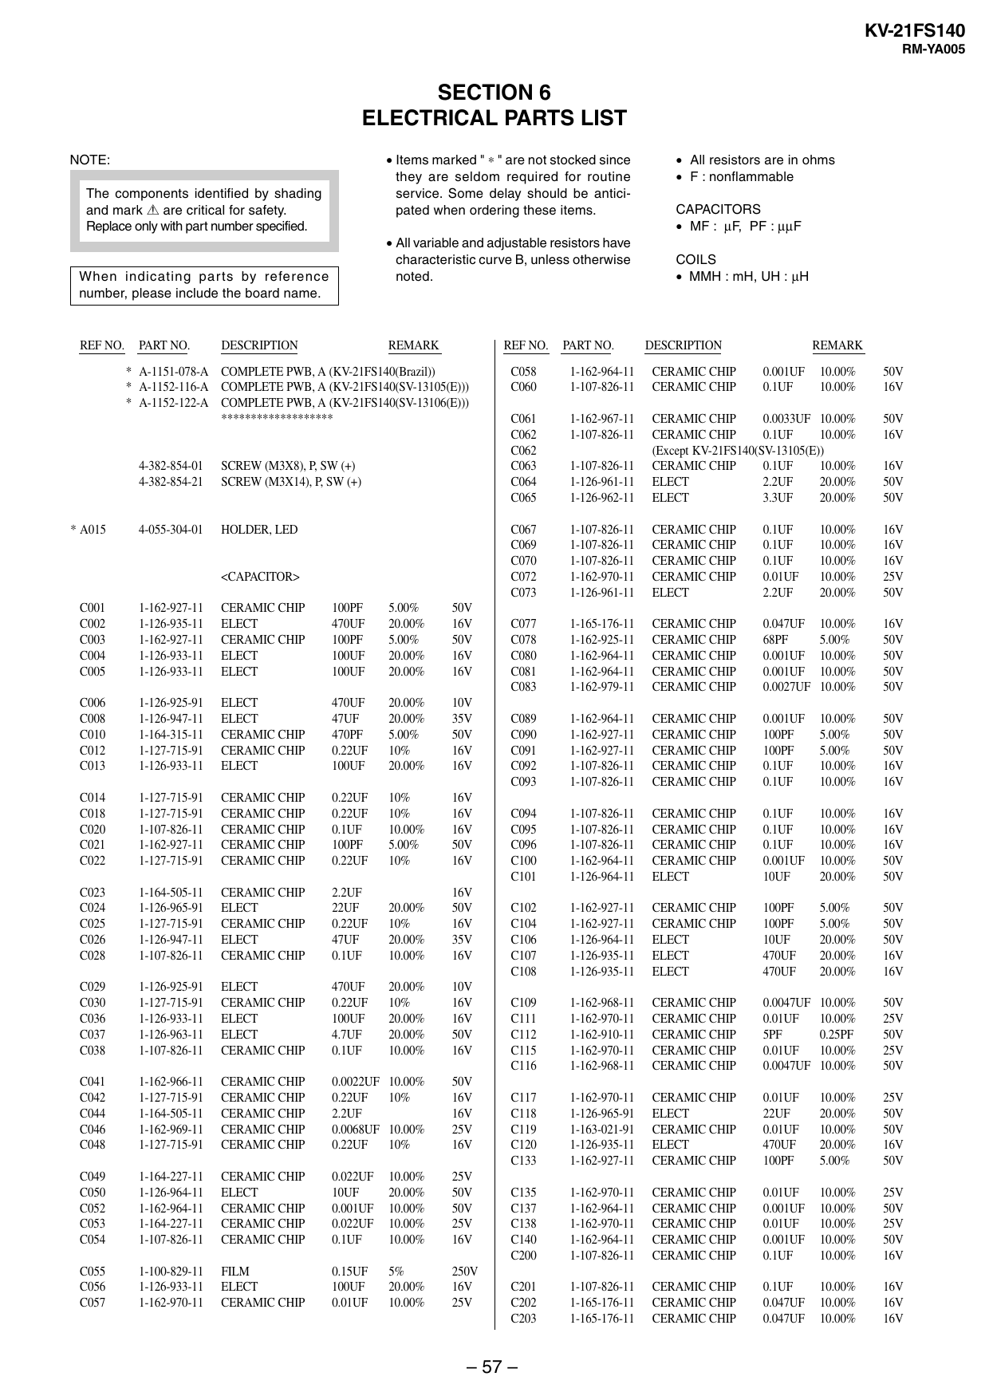
[picture p39: tv/manual/rev_brazil/pages/img/page-50.png]
page-50


KV-21FS140
RM-YA005
The components identified by shading
and mark ! are critical for safety.
Replace only with part number specified.

SECTION 6
ELECTRICAL PARTS LIST

A

REF NO.
NOTE:

PART NO.

DESCRIPTION

REMARK
REF NO. PART NO.
• Items marked " ∗ " are not stocked since
they are seldom required for routine
service. Some delay should be anticipated when ordering these items.

The components identified by shading
and mark ! are critical for safety.
Replace only with part number specified.

• All variable and adjustable resistors have
characteristic curve B, unless otherwise
noted.

When indicating par ts by reference
number, please include the board name.

REF NO.

PART NO.

DESCRIPTION

REMARK

* A-1151-078-A COMPLETE PWB, A (KV-21FS140(Brazil))
* A-1152-116-A COMPLETE PWB, A (KV-21FS140(SV-13105(E)))
* A-1152-122-A COMPLETE PWB, A (KV-21FS140(SV-13106(E)))
*******************

* A015

4-382-854-01
4-382-854-21

SCREW (M3X8), P, SW (+)
SCREW (M3X14), P, SW (+)

4-055-304-01

HOLDER, LED

<CAPACITOR>
C001
C002
C003
C004
C005

1-162-927-11
1-126-935-11
1-162-927-11
1-126-933-11
1-126-933-11

CERAMIC CHIP
ELECT
CERAMIC CHIP
ELECT
ELECT

100PF
470UF
100PF
100UF
100UF

5.00%
20.00%
5.00%
20.00%
20.00%

50V
16V
50V
16V
16V

C006
C008
C010
C012
C013

1-126-925-91
1-126-947-11
1-164-315-11
1-127-715-91
1-126-933-11

ELECT
ELECT
CERAMIC CHIP
CERAMIC CHIP
ELECT

470UF
47UF
470PF
0.22UF
100UF

20.00%
20.00%
5.00%
10%
20.00%

10V
35V
50V
16V
16V

C014
C018
C020
C021
C022

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
CERAMIC CHIP

0.01UF
0.001UF
0.01UF
0.001UF
0.1UF

10.00%
10.00%
10.00%
10.00%
10.00%

25V
50V
25V
50V
16V

C201
C202
C203

1-107-826-11
1-165-176-11
1-165-176-11

CERAMIC CHIP
CERAMIC CHIP
CERAMIC CHIP

0.1UF
0.047UF
0.047UF

10.00%
10.00%
10.00%

16V
16V
16V

– 57 –

REMARK
0.001UF
0.1UF
