nrzimmer/retro-crt/tv/manual/rev_brazil/pages/page-51.md

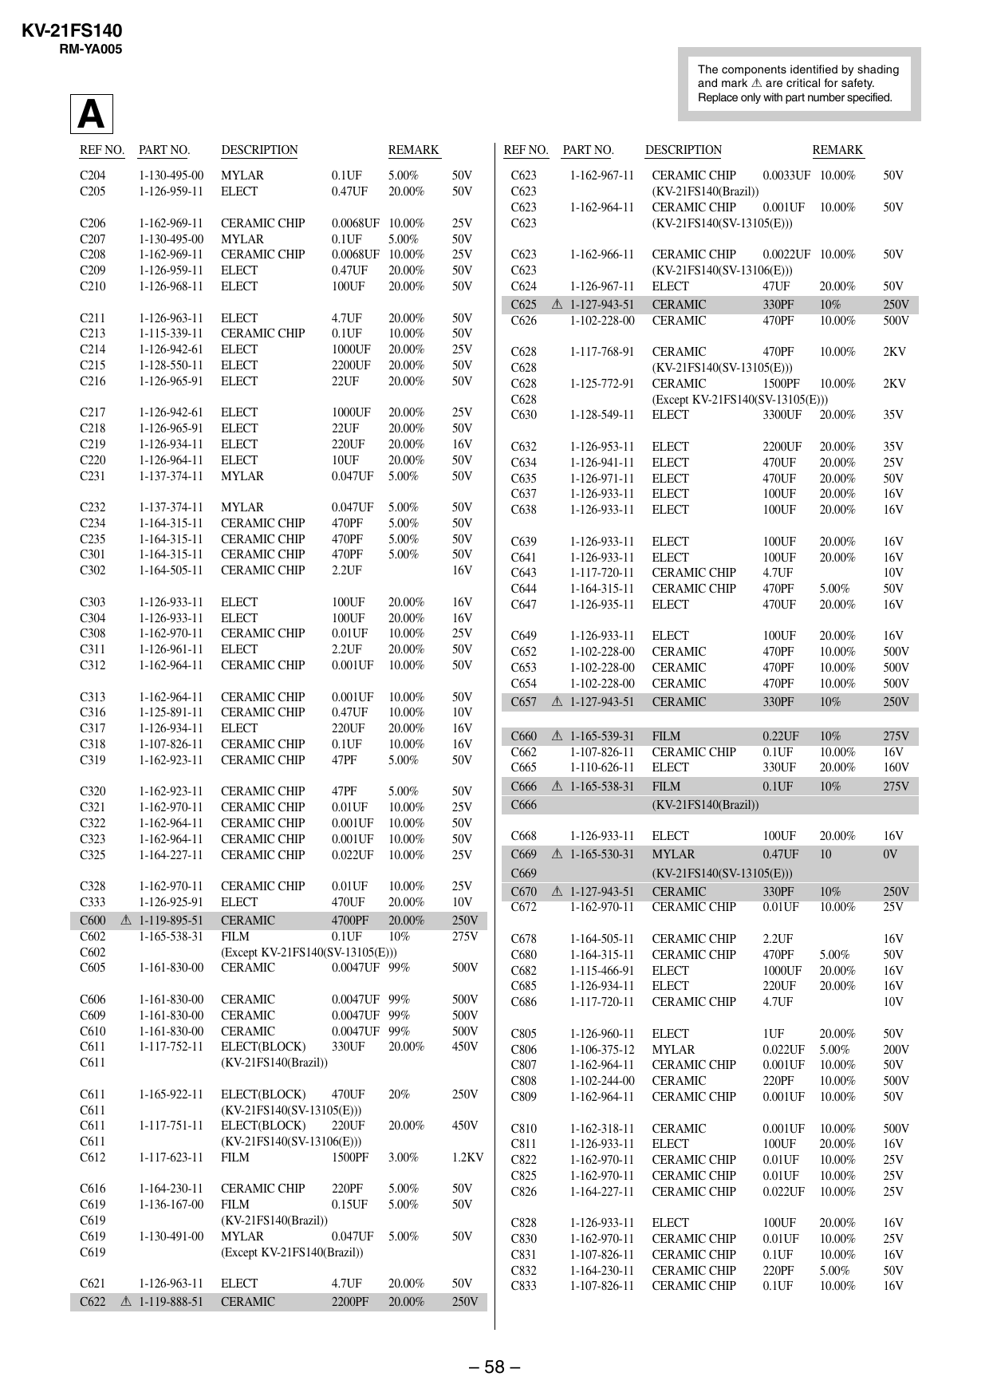
[picture p40: tv/manual/rev_brazil/pages/img/page-51.png]
page-51


KV-21FS140
RM-YA005
The components identified by shading
and mark ! are critical for safety.
Replace only with part number specified.

A
REF NO.

PART NO.

DESCRIPTION

C204
C205

1-130-495-00
1-126-959-11

MYLAR
ELECT

0.1UF
0.47UF

5.00%
20.00%

50V
50V

C206
C207
C208
C209
C210

1-162-969-11
1-130-495-00
1-162-969-11
1-126-959-11
1-126-968-11

CERAMIC CHIP
MYLAR
CERAMIC CHIP
ELECT
ELECT

0.0068UF 10.00%
0.1UF
5.00%
0.0068UF 10.00%
0.47UF
20.00%
100UF
20.00%

25V
50V
25V
50V
50V

C211
C213
C214
C215
C216

1-126-963-11
1-115-339-11
1-126-942-61
1-128-550-11
1-126-965-91

ELECT
CERAMIC CHIP
ELECT
ELECT
ELECT

4.7UF
0.1UF
1000UF
2200UF
22UF

20.00%
10.00%
20.00%
20.00%
20.00%

50V
50V
25V
50V
50V

C217
C218
C219
C220
C231

1-126-942-61
1-126-965-91
1-126-934-11
1-126-964-11
1-137-374-11

ELECT
ELECT
ELECT
ELECT
MYLAR

1000UF
22UF
220UF
10UF
0.047UF

20.00%
20.00%
20.00%
20.00%
5.00%

25V
50V
16V
50V
50V

C232
C234
C235
C301
C302

1-137-374-11
1-164-315-11
1-164-315-11
1-164-315-11
1-164-505-11

MYLAR
CERAMIC CHIP
CERAMIC CHIP
CERAMIC CHIP
CERAMIC CHIP

0.047UF
470PF
470PF
470PF
2.2UF

5.00%
5.00%
5.00%
5.00%

50V
50V
50V
50V
16V

C303
C304
C308
C311
C312

1-126-933-11
1-126-933-11
1-162-970-11
1-126-961-11
1-162-964-11

ELECT
ELECT
CERAMIC CHIP
ELECT
CERAMIC CHIP

100UF
100UF
0.01UF
2.2UF
0.001UF

20.00%
20.00%
10.00%
20.00%
10.00%

16V
16V
25V
50V
50V

C313
C316
C317
C318
C319

1-162-964-11
1-125-891-11
1-126-934-11
1-107-826-11
1-162-923-11

CERAMIC CHIP
CERAMIC CHIP
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
C831
C832
C833

1-126-933-11
1-162-970-11
1-107-826-11
1-164-230-11
1-107-826-11

ELECT
CERAMIC CHIP
CERAMIC CHIP
CERAMIC CHIP
CERAMIC CHIP

100UF
0.01UF
0.1UF
220PF
0.1UF

20.00%
10.00%
10.00%
5.00%
10.00%

16V
25V
16V
50V
16V

– 58 –

1-117-768-91

REMARK

! 1-127-943-51
1-162-970-11

2KV

35V
