nrzimmer/retro-crt/tv/manual/rev_brazil/pages/page-52.md

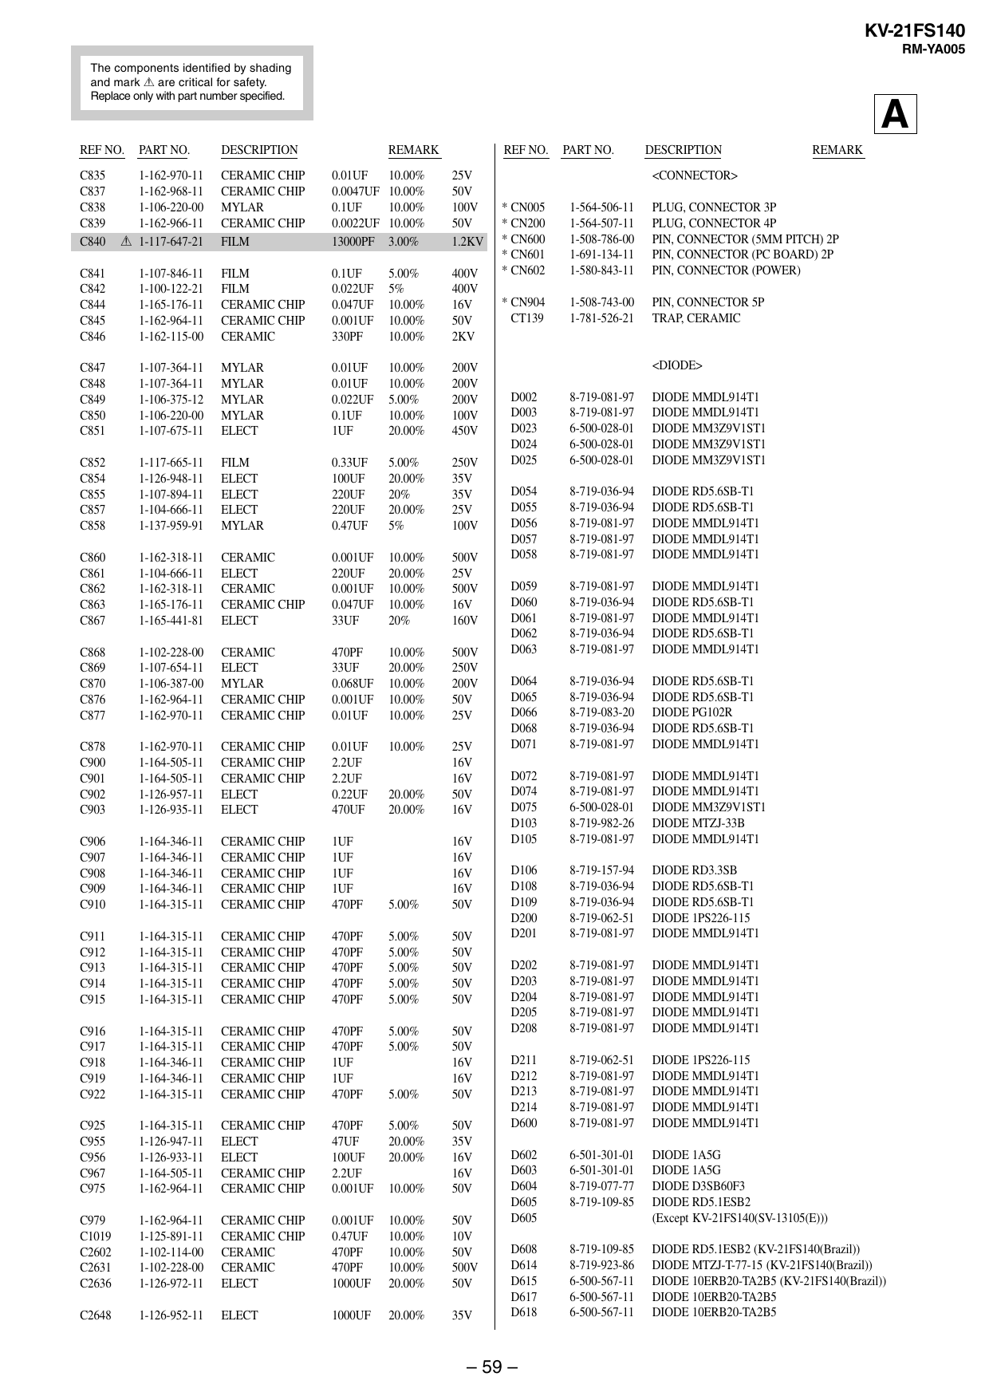
[picture p41: tv/manual/rev_brazil/pages/img/page-52.png]
page-52


KV-21FS140
RM-YA005
The components identified by shading
and mark ! are critical for safety.
Replace only with part number specified.

REF NO.

A

PART NO.

DESCRIPTION

REMARK

C835
C837
C838
C839
C840

1-162-970-11
1-162-968-11
1-106-220-00
1-162-966-11
! 1-117-647-21

CERAMIC CHIP
CERAMIC CHIP
MYLAR
CERAMIC CHIP
FILM

0.01UF
10.00%
0.0047UF 10.00%
0.1UF
10.00%
0.0022UF 10.00%
13000PF 3.00%

25V
50V
100V
50V
1.2KV

C841
C842
C844
C845
C846

1-107-846-11
1-100-122-21
1-165-176-11
1-162-964-11
1-162-115-00

FILM
FILM
CERAMIC CHIP
CERAMIC CHIP
CERAMIC

0.1UF
0.022UF
0.047UF
0.001UF
330PF

5.00%
5%
10.00%
10.00%
10.00%

400V
400V
16V
50V
2KV

C847
C848
C849
C850
C851

1-107-364-11
1-107-364-11
1-106-375-12
1-106-220-00
1-107-675-11

MYLAR
MYLAR
MYLAR
MYLAR
ELECT

0.01UF
0.01UF
0.022UF
0.1UF
1UF

10.00%
10.00%
5.00%
10.00%
20.00%

200V
200V
200V
100V
450V

C852
C854
C855
C857
C858

1-117-665-11
1-126-948-11
1-107-894-11
1-104-666-11
1-137-959-91

FILM
ELECT
ELECT
ELECT
MYLAR

0.33UF
100UF
220UF
220UF
0.47UF

5.00%
20.00%
20%
20.00%
5%

250V
35V
35V
25V
100V

C860
C861
C862
C863
C867

1-162-318-11
1-104-666-11
1-162-318-11
1-165-176-11
1-165-441-81

CERAMIC
ELECT
CERAMIC
CERAMIC CHIP
ELECT

0.001UF
220UF
0.001UF
0.047UF
33UF

10.00%
20.00%
10.00%
10.00%
20%

500V
25V
500V
16V
160V

C868
C869
C870
C876
C877

1-102-228-00
1-107-654-11
1-106-387-00
1-162-964-11
1-162-970-11

CERAMIC
ELECT
MYLAR
CERAMIC CHIP
CERAMIC CHIP

470PF
33UF
0.068UF
0.001UF
0.01UF

10.00%
20.00%
10.00%
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
(Except KV-21FS140(SV-13105(E)))

D608
D614
D615
D617
D618

8-719-109-85
8-719-923-86
6-500-567-11
6-500-567-11
6-500-567-11

DIODE RD5.1ESB2 (KV-21FS140(Brazil))
DIODE MTZJ-T-77-15 (KV-21FS140(Brazil))
DIODE 10ERB20-TA2B5 (KV-21FS140(Brazil))
DIODE 10ERB20-TA2B5
DIODE 10ERB20-TA2B5

– 59 –
