nrzimmer/retro-crt/tv/manual/rev_s79aa/pages/page-09.md

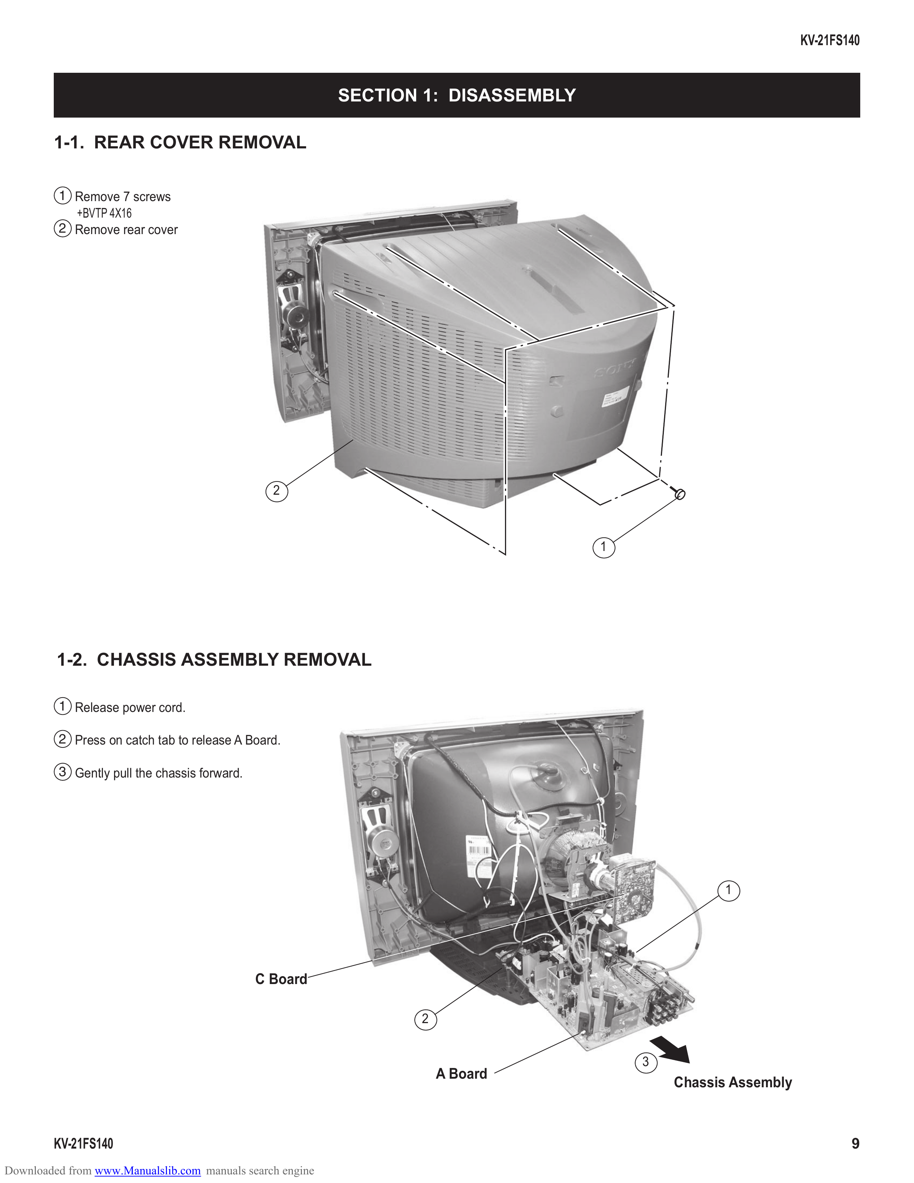
[picture p50: tv/manual/rev_s79aa/pages/img/page-09.png]
page-09


                                                                                                               KV-21FS140

                                                           SECTION 1: DISASSEMBLY

        1-1. REAR COVER REMOVAL

         1 Remove 7 screws
           +BVTP 4X16
         2 Remove rear cover

                                                2

                                                                                    1

         1-2. CHASSIS ASSEMBLY REMOVAL

         1 Release power cord.

         2 Press on catch tab to release A Board.

         3 Gently pull the chassis forward.

                                                                                                  1

                                              C Board

                                                                  2

                                                                                        3
                                                                      A Board
                                                                                            Chassis Assembly

        KV-21FS140                                                                                                     9
Downloaded from www.Manualslib.com manuals search engine
