nrzimmer/retro-crt/tv/manual/rev_s79aa/pages/page-50.md

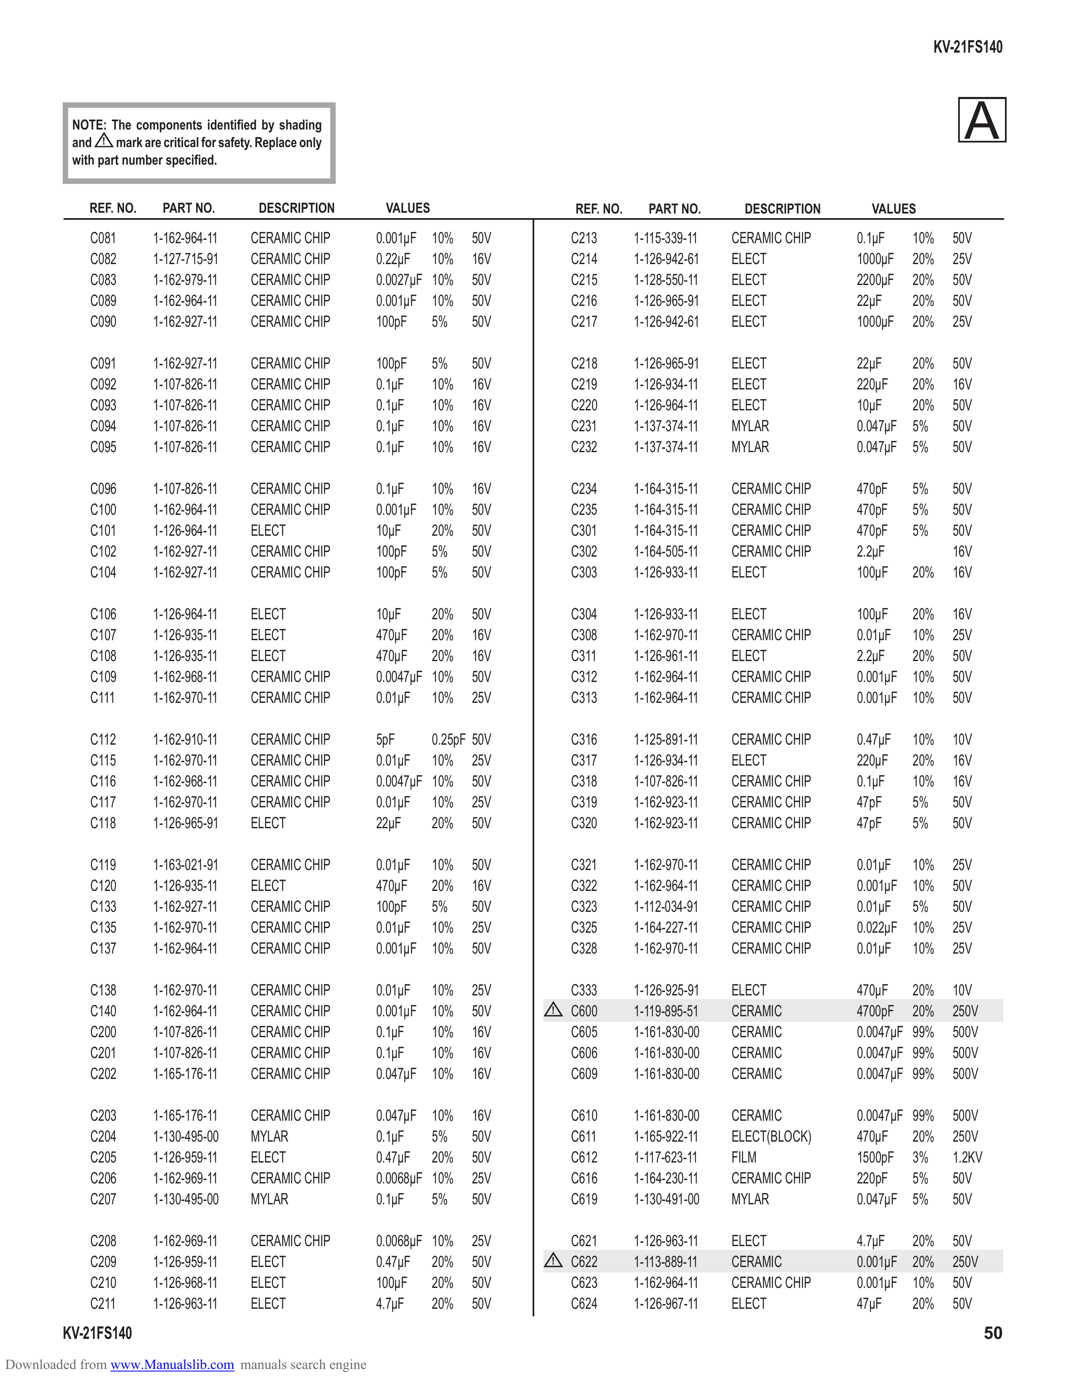
[picture p59: tv/manual/rev_s79aa/pages/img/page-50.png]
page-50


                                                                                                                                               KV-21FS140

          NOTE: The components identiﬁed by shading
          and ! mark are critical for safety. Replace only
          with part number speciﬁed.
                                                                                                                                                   A
             REF. NO.      PART NO.          DESCRIPTION      VALUES                   REF. NO.     PART NO.      DESCRIPTION     VALUES

             C081        1-162-964-11       CERAMIC CHIP     0.001µF 10%     50V       C213       1-115-339-11   CERAMIC CHIP   0.1µF     10%    50V
             C082        1-127-715-91       CERAMIC CHIP     0.22µF 10%      16V       C214       1-126-942-61   ELECT          1000µF    20%    25V
             C083        1-162-979-11       CERAMIC CHIP     0.0027µF 10%    50V       C215       1-128-550-11   ELECT          2200µF    20%    50V
             C089        1-162-964-11       CERAMIC CHIP     0.001µF 10%     50V       C216       1-126-965-91   ELECT          22µF      20%    50V
             C090        1-162-927-11       CERAMIC CHIP     100pF    5%     50V       C217       1-126-942-61   ELECT          1000µF    20%    25V

             C091        1-162-927-11       CERAMIC CHIP     100pF     5%    50V       C218       1-126-965-91   ELECT          22µF      20%    50V
             C092        1-107-826-11       CERAMIC CHIP     0.1µF     10%   16V       C219       1-126-934-11   ELECT          220µF     20%    16V
             C093        1-107-826-11       CERAMIC CHIP     0.1µF     10%   16V       C220       1-126-964-11   ELECT          10µF      20%    50V
             C094        1-107-826-11       CERAMIC CHIP     0.1µF     10%   16V       C231       1-137-374-11   MYLAR          0.047µF   5%     50V
             C095        1-107-826-11       CERAMIC CHIP     0.1µF     10%   16V       C232       1-137-374-11   MYLAR          0.047µF   5%     50V

             C096        1-107-826-11       CERAMIC CHIP     0.1µF     10%   16V       C234       1-164-315-11   CERAMIC CHIP   470pF     5%     50V
             C100        1-162-964-11       CERAMIC CHIP     0.001µF   10%   50V       C235       1-164-315-11   CERAMIC CHIP   470pF     5%     50V
             C101        1-126-964-11       ELECT            10µF      20%   50V       C301       1-164-315-11   CERAMIC CHIP   470pF     5%     50V
             C102        1-162-927-11       CERAMIC CHIP     100pF     5%    50V       C302       1-164-505-11   CERAMIC CHIP   2.2µF            16V
             C104        1-162-927-11       CERAMIC CHIP     100pF     5%    50V       C303       1-126-933-11   ELECT          100µF     20%    16V

             C106        1-126-964-11       ELECT            10µF     20%    50V       C304       1-126-933-11   ELECT          100µF     20%    16V
             C107        1-126-935-11       ELECT            470µF    20%    16V       C308       1-162-970-11   CERAMIC CHIP   0.01µF    10%    25V
             C108        1-126-935-11       ELECT            470µF    20%    16V       C311       1-126-961-11   ELECT          2.2µF     20%    50V
             C109        1-162-968-11       CERAMIC CHIP     0.0047µF 10%    50V       C312       1-162-964-11   CERAMIC CHIP   0.001µF   10%    50V
             C111        1-162-970-11       CERAMIC CHIP     0.01µF 10%      25V       C313       1-162-964-11   CERAMIC CHIP   0.001µF   10%    50V

             C112        1-162-910-11       CERAMIC CHIP     5pF      0.25pF 50V       C316       1-125-891-11   CERAMIC CHIP   0.47µF    10%    10V
             C115        1-162-970-11       CERAMIC CHIP     0.01µF 10% 25V            C317       1-126-934-11   ELECT          220µF     20%    16V
             C116        1-162-968-11       CERAMIC CHIP     0.0047µF 10% 50V          C318       1-107-826-11   CERAMIC CHIP   0.1µF     10%    16V
             C117        1-162-970-11       CERAMIC CHIP     0.01µF 10% 25V            C319       1-162-923-11   CERAMIC CHIP   47pF      5%     50V
             C118        1-126-965-91       ELECT            22µF     20% 50V          C320       1-162-923-11   CERAMIC CHIP   47pF      5%     50V

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
        KV-21FS140                                                                                                                                       50
Downloaded from www.Manualslib.com manuals search engine
