nrzimmer/retro-crt/tv/manual/rev_s79aa/pages/page-51.md

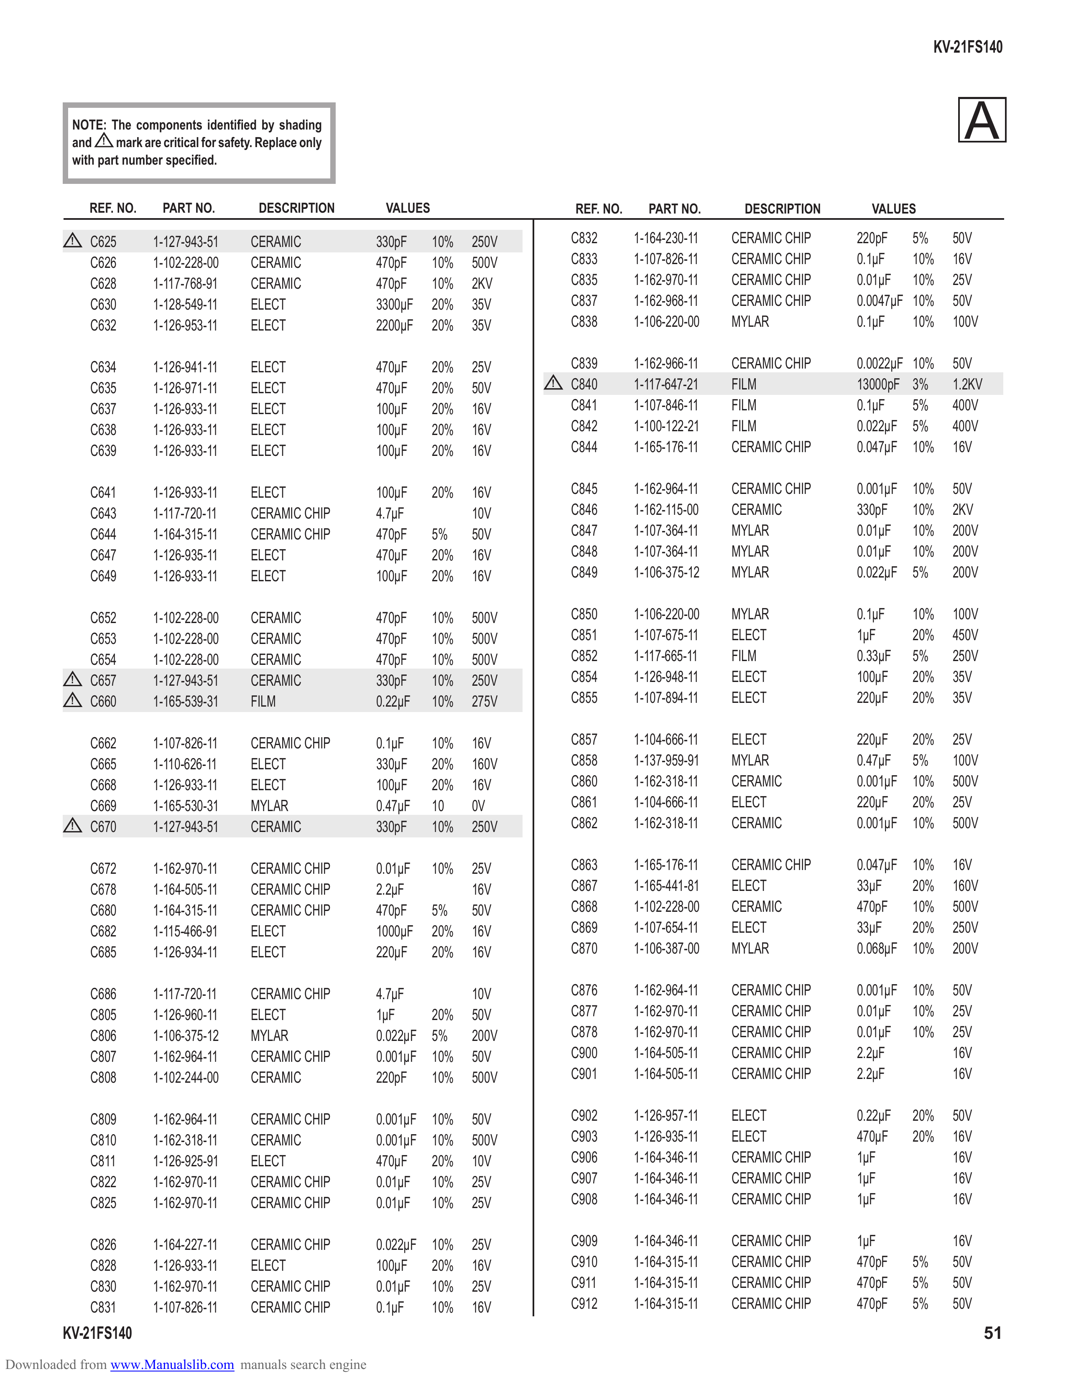
[picture p60: tv/manual/rev_s79aa/pages/img/page-51.png]
page-51


                                                                                                                                                KV-21FS140

          NOTE: The components identiﬁed by shading
          and ! mark are critical for safety. Replace only
          with part number speciﬁed.
                                                                                                                                                    A
              REF. NO.     PART NO.          DESCRIPTION      VALUES                    REF. NO.     PART NO.      DESCRIPTION     VALUES

          !   C625       1-127-943-51       CERAMIC          330pF     10%   250V       C832       1-164-230-11   CERAMIC CHIP   220pF    5%      50V
              C626       1-102-228-00       CERAMIC          470pF     10%   500V       C833       1-107-826-11   CERAMIC CHIP   0.1µF    10%     16V
              C628       1-117-768-91       CERAMIC          470pF     10%   2KV        C835       1-162-970-11   CERAMIC CHIP   0.01µF 10%       25V
              C630       1-128-549-11       ELECT            3300µF    20%   35V        C837       1-162-968-11   CERAMIC CHIP   0.0047µF 10%     50V
              C632       1-126-953-11       ELECT            2200µF    20%   35V        C838       1-106-220-00   MYLAR          0.1µF    10%     100V

              C634       1-126-941-11       ELECT            470µF     20%   25V        C839       1-162-966-11   CERAMIC CHIP   0.0022µF 10%     50V
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
        KV-21FS140                                                                                                                                        51
Downloaded from www.Manualslib.com manuals search engine
