nrzimmer/retro-crt/tv/manual/rev_s79aa/pages/page-52.md

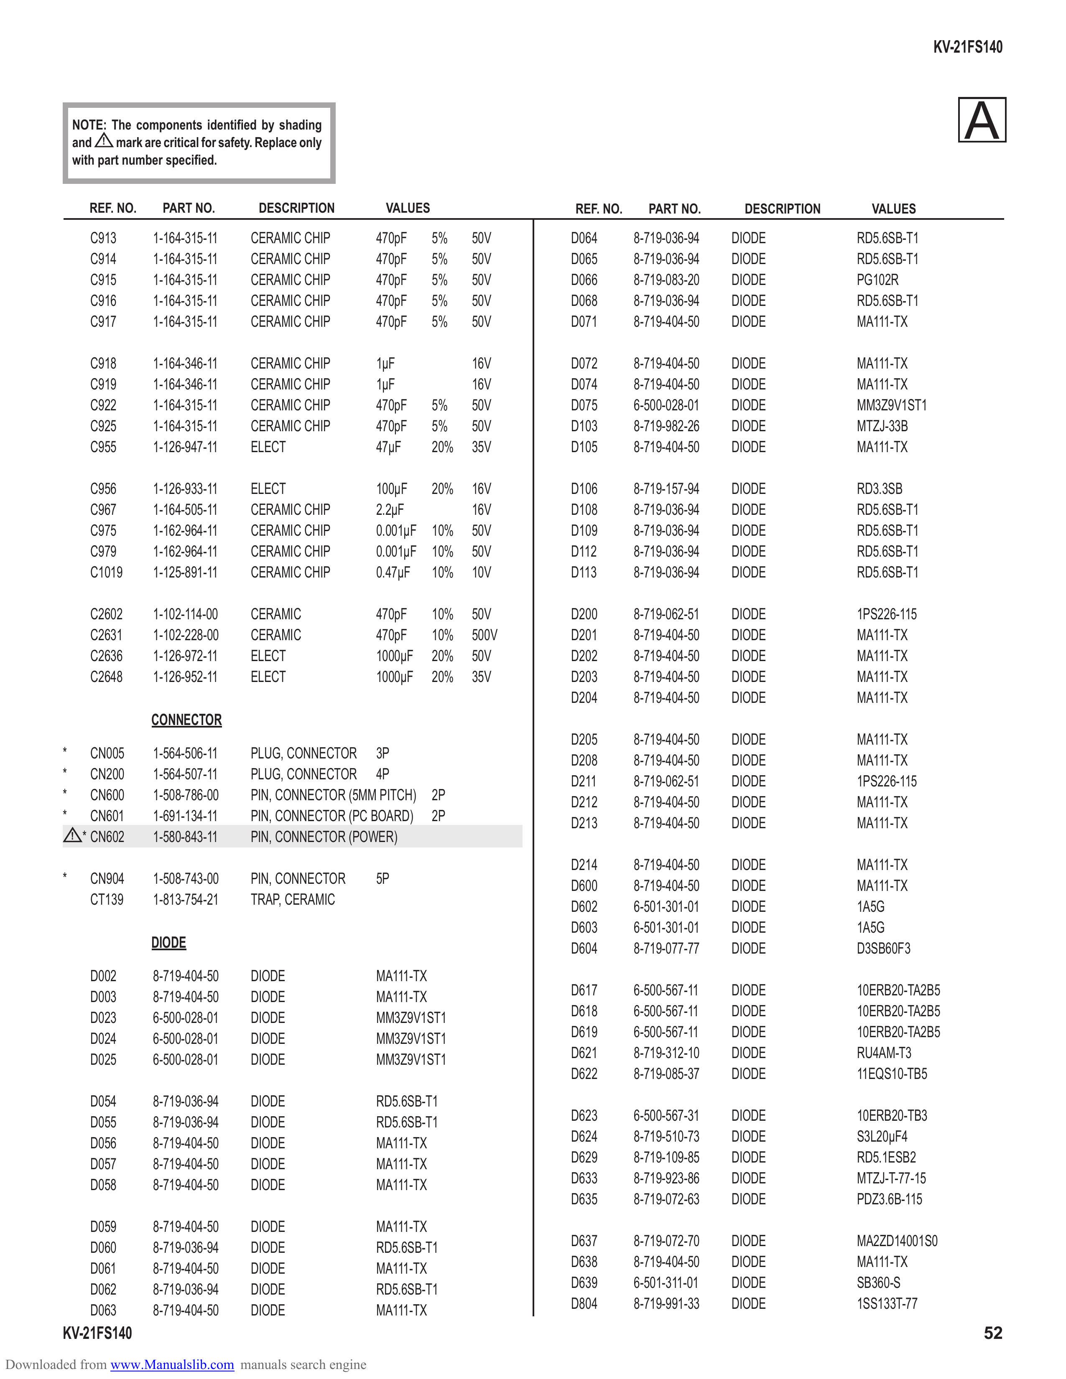
[picture p61: tv/manual/rev_s79aa/pages/img/page-52.png]
page-52


                                                                                                                                                KV-21FS140

            NOTE: The components identiﬁed by shading
            and ! mark are critical for safety. Replace only
            with part number speciﬁed.
                                                                                                                                                    A
               REF. NO.      PART NO.          DESCRIPTION        VALUES                REF. NO.     PART NO.      DESCRIPTION     VALUES

               C913        1-164-315-11       CERAMIC CHIP      470pF      5%    50V    D064       8-719-036-94   DIODE          RD5.6SB-T1
               C914        1-164-315-11       CERAMIC CHIP      470pF      5%    50V    D065       8-719-036-94   DIODE          RD5.6SB-T1
               C915        1-164-315-11       CERAMIC CHIP      470pF      5%    50V    D066       8-719-083-20   DIODE          PG102R
               C916        1-164-315-11       CERAMIC CHIP      470pF      5%    50V    D068       8-719-036-94   DIODE          RD5.6SB-T1
               C917        1-164-315-11       CERAMIC CHIP      470pF      5%    50V    D071       8-719-404-50   DIODE          MA111-TX

               C918        1-164-346-11       CERAMIC CHIP      1µF              16V    D072       8-719-404-50   DIODE          MA111-TX
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
        KV-21FS140                                                                                                                                     52
Downloaded from www.Manualslib.com manuals search engine
