nrzimmer/retro-crt/tv/manual/rev_s79aa/pages/page-59.md

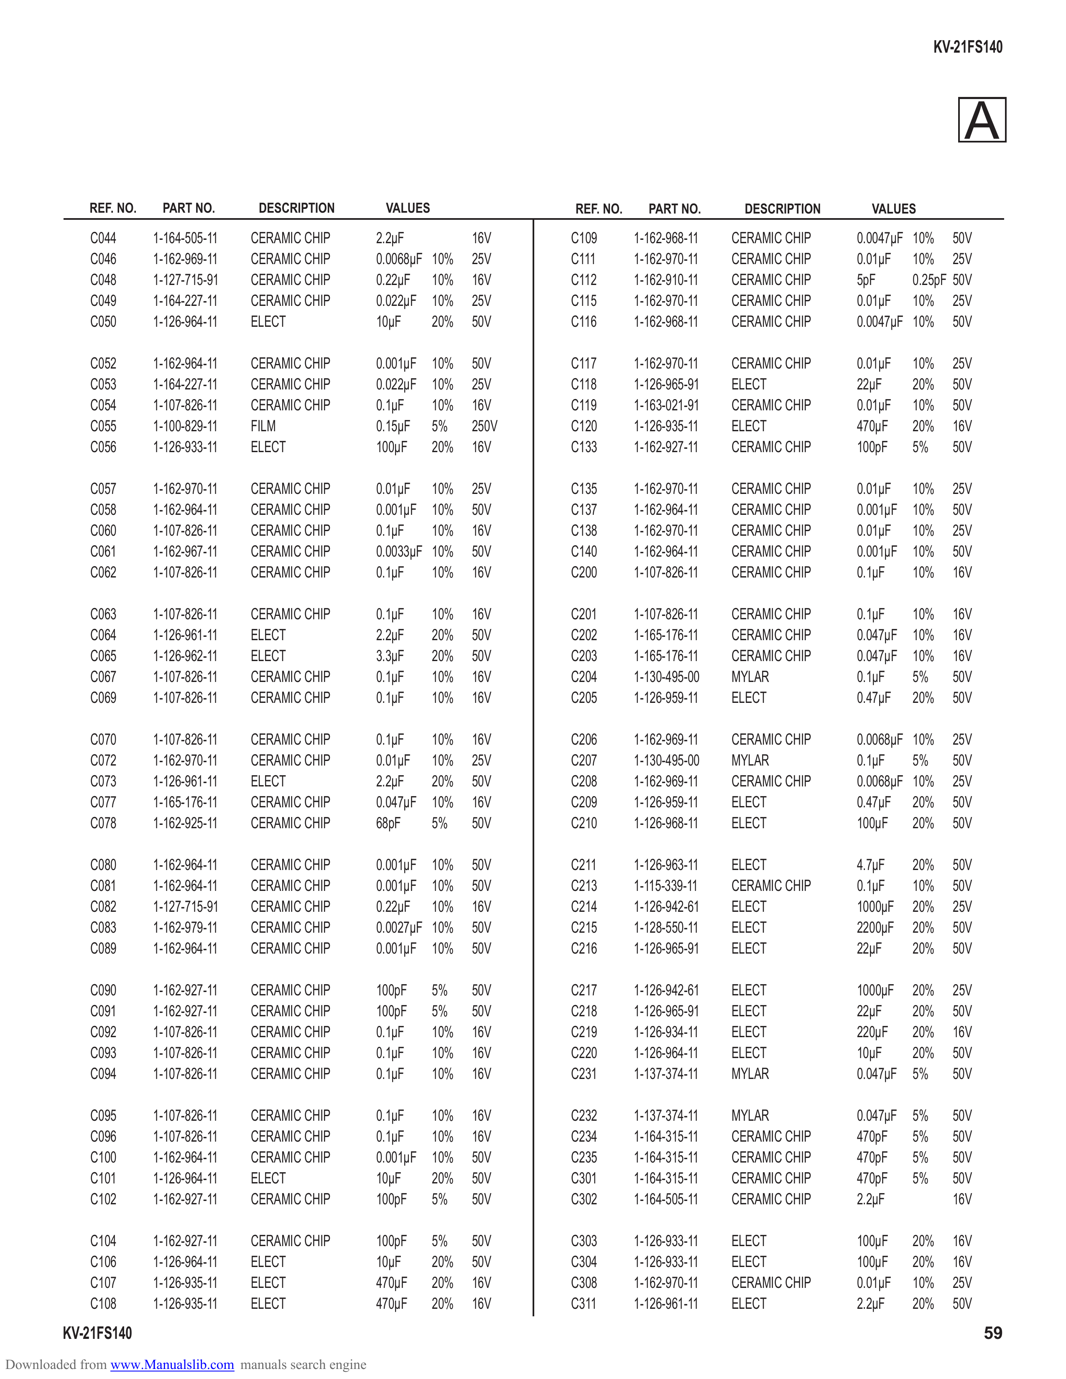
[picture p64: tv/manual/rev_s79aa/pages/img/page-59.png]
page-59


                                                                                                                                          KV-21FS140

                                                                                                                                              A
             REF. NO.    PART NO.       DESCRIPTION         VALUES                REF. NO.     PART NO.      DESCRIPTION     VALUES

             C044       1-164-505-11   CERAMIC CHIP        2.2µF           16V    C109       1-162-968-11   CERAMIC CHIP   0.0047µF 10% 50V
             C046       1-162-969-11   CERAMIC CHIP        0.0068µF 10%    25V    C111       1-162-970-11   CERAMIC CHIP   0.01µF 10% 25V
             C048       1-127-715-91   CERAMIC CHIP        0.22µF 10%      16V    C112       1-162-910-11   CERAMIC CHIP   5pF      0.25pF 50V
             C049       1-164-227-11   CERAMIC CHIP        0.022µF 10%     25V    C115       1-162-970-11   CERAMIC CHIP   0.01µF 10% 25V
             C050       1-126-964-11   ELECT               10µF     20%    50V    C116       1-162-968-11   CERAMIC CHIP   0.0047µF 10% 50V

             C052       1-162-964-11   CERAMIC CHIP        0.001µF   10%   50V    C117       1-162-970-11   CERAMIC CHIP   0.01µF    10%    25V
             C053       1-164-227-11   CERAMIC CHIP        0.022µF   10%   25V    C118       1-126-965-91   ELECT          22µF      20%    50V
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
        KV-21FS140                                                                                                                                59
Downloaded from www.Manualslib.com manuals search engine
