nrzimmer/retro-crt/tv/manual/rev_s79aa/pages/page-61.md

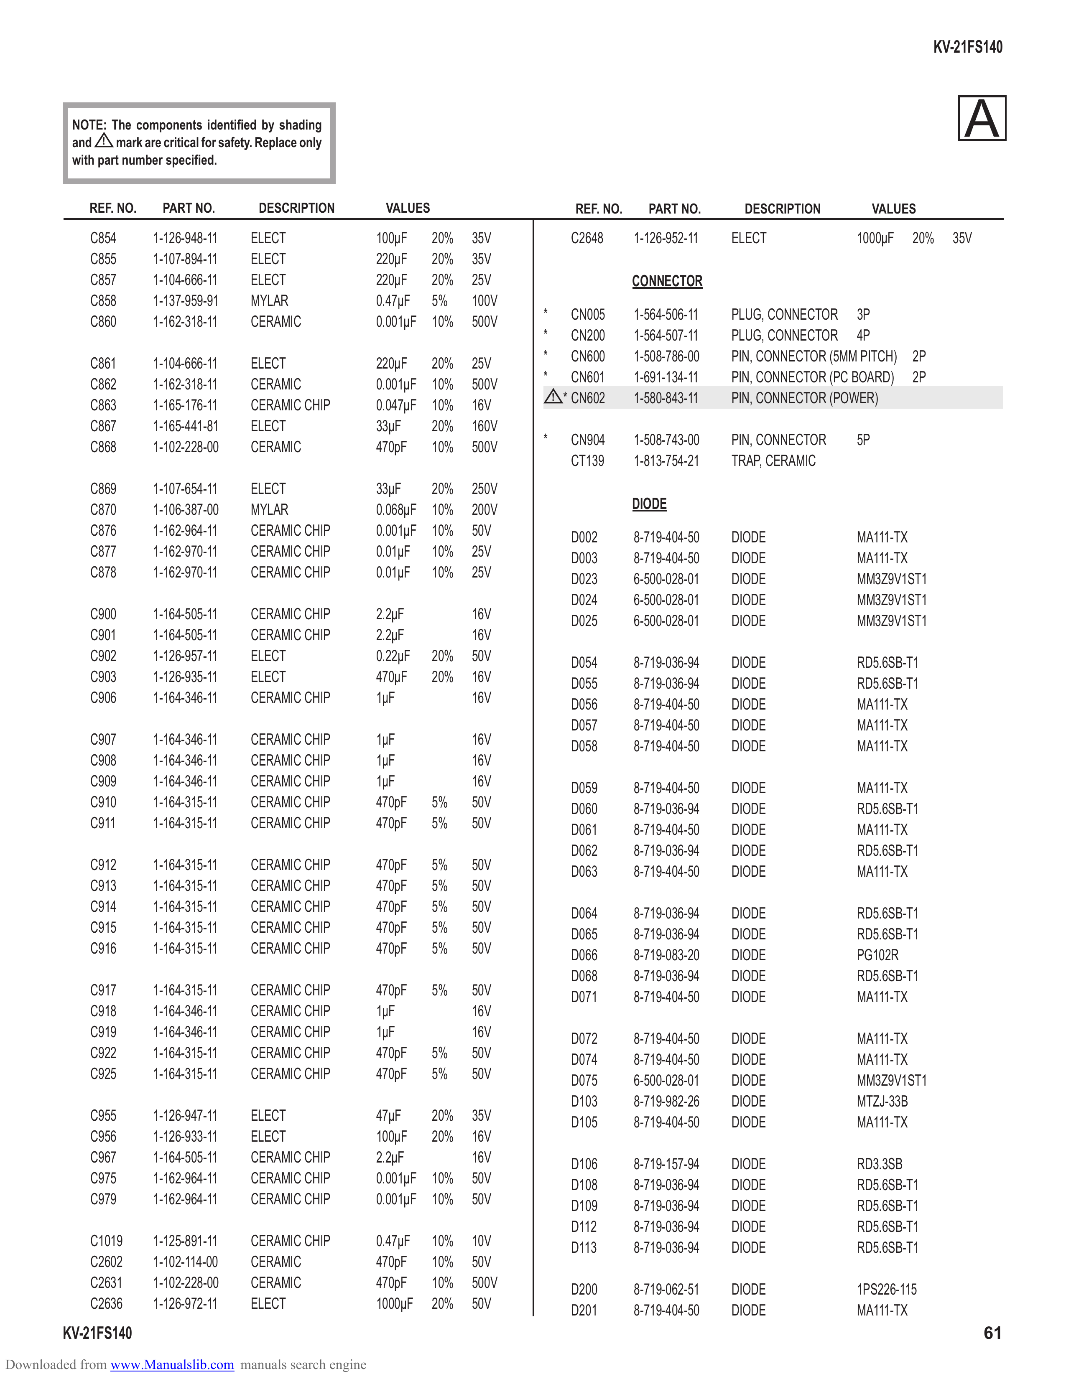
[picture p66: tv/manual/rev_s79aa/pages/img/page-61.png]
page-61


                                                                                                                                                     KV-21FS140

          NOTE: The components identiﬁed by shading
          and ! mark are critical for safety. Replace only
                                                                                                                                                         A
          with part number speciﬁed.

             REF. NO.      PART NO.          DESCRIPTION      VALUES                       REF. NO.     PART NO.      DESCRIPTION           VALUES

             C854        1-126-948-11       ELECT            100µF     20%   35V           C2648      1-126-952-11   ELECT             1000µF    20%   35V
             C855        1-107-894-11       ELECT            220µF     20%   35V
             C857        1-104-666-11       ELECT            220µF     20%   25V                      CONNECTOR
             C858        1-137-959-91       MYLAR            0.47µF    5%    100V
             C860        1-162-318-11       CERAMIC          0.001µF   10%   500V   *       CN005     1-564-506-11   PLUG, CONNECTOR 3P
                                                                                    *       CN200     1-564-507-11   PLUG, CONNECTOR 4P
             C861        1-104-666-11       ELECT            220µF     20%   25V    *       CN600     1-508-786-00   PIN, CONNECTOR (5MM PITCH) 2P
             C862        1-162-318-11       CERAMIC          0.001µF   10%   500V   *       CN601     1-691-134-11   PIN, CONNECTOR (PC BOARD) 2P
                                                                                        ! * CN602     1-580-843-11   PIN, CONNECTOR (POWER)
             C863        1-165-176-11       CERAMIC CHIP     0.047µF   10%   16V
             C867        1-165-441-81       ELECT            33µF      20%   160V
             C868        1-102-228-00       CERAMIC          470pF     10%   500V   *      CN904      1-508-743-00   PIN, CONNECTOR    5P
                                                                                           CT139      1-813-754-21   TRAP, CERAMIC
             C869        1-107-654-11       ELECT            33µF      20%   250V
             C870        1-106-387-00       MYLAR            0.068µF   10%   200V                     DIODE
             C876        1-162-964-11       CERAMIC CHIP     0.001µF   10%   50V           D002       8-719-404-50   DIODE             MA111-TX
             C877        1-162-970-11       CERAMIC CHIP     0.01µF    10%   25V           D003       8-719-404-50   DIODE             MA111-TX
             C878        1-162-970-11       CERAMIC CHIP     0.01µF    10%   25V           D023       6-500-028-01   DIODE             MM3Z9V1ST1
                                                                                           D024       6-500-028-01   DIODE             MM3Z9V1ST1
             C900        1-164-505-11       CERAMIC CHIP     2.2µF           16V           D025       6-500-028-01   DIODE             MM3Z9V1ST1
             C901        1-164-505-11       CERAMIC CHIP     2.2µF           16V
             C902        1-126-957-11       ELECT            0.22µF    20%   50V           D054       8-719-036-94   DIODE             RD5.6SB-T1
             C903        1-126-935-11       ELECT            470µF     20%   16V           D055       8-719-036-94   DIODE             RD5.6SB-T1
             C906        1-164-346-11       CERAMIC CHIP     1µF             16V           D056       8-719-404-50   DIODE             MA111-TX
                                                                                           D057       8-719-404-50   DIODE             MA111-TX
             C907        1-164-346-11       CERAMIC CHIP     1µF             16V           D058       8-719-404-50   DIODE             MA111-TX
             C908        1-164-346-11       CERAMIC CHIP     1µF             16V
             C909        1-164-346-11       CERAMIC CHIP     1µF             16V           D059       8-719-404-50   DIODE             MA111-TX
             C910        1-164-315-11       CERAMIC CHIP     470pF     5%    50V           D060       8-719-036-94   DIODE             RD5.6SB-T1
             C911        1-164-315-11       CERAMIC CHIP     470pF     5%    50V           D061       8-719-404-50   DIODE             MA111-TX
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
        KV-21FS140                                                                                                                                           61
Downloaded from www.Manualslib.com manuals search engine
