nrzimmer/retro-crt/tv/manual/rev_s79aa/pages/page-62.md

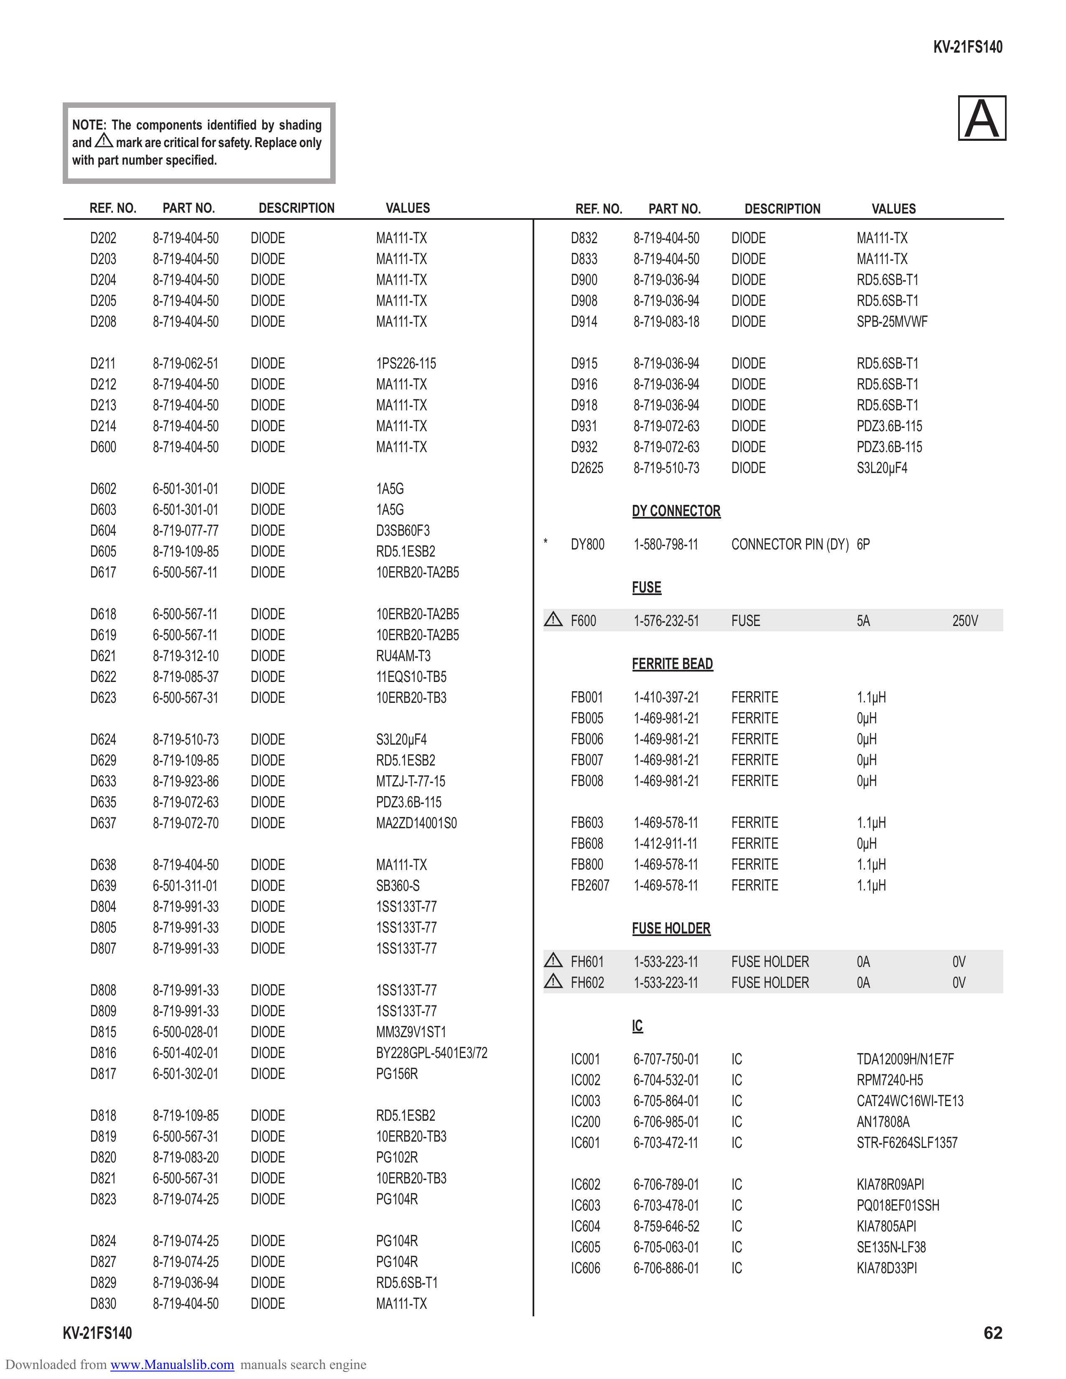
[picture p67: tv/manual/rev_s79aa/pages/img/page-62.png]
page-62


                                                                                                                                                      KV-21FS140

          NOTE: The components identiﬁed by shading
          and ! mark are critical for safety. Replace only
                                                                                                                                                           A
          with part number speciﬁed.

             REF. NO.      PART NO.          DESCRIPTION      VALUES                      REF. NO.        PART NO.        DESCRIPTION        VALUES

             D202        8-719-404-50       DIODE            MA111-TX                     D832       8-719-404-50    DIODE              MA111-TX
             D203        8-719-404-50       DIODE            MA111-TX                     D833       8-719-404-50    DIODE              MA111-TX
             D204        8-719-404-50       DIODE            MA111-TX                     D900       8-719-036-94    DIODE              RD5.6SB-T1
             D205        8-719-404-50       DIODE            MA111-TX                     D908       8-719-036-94    DIODE              RD5.6SB-T1
             D208        8-719-404-50       DIODE            MA111-TX                     D914       8-719-083-18    DIODE              SPB-25MVWF

             D211        8-719-062-51       DIODE            1PS226-115                   D915       8-719-036-94    DIODE              RD5.6SB-T1
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
                                                                                          IC003      6-705-864-01    IC                 CAT24WC16WI-TE13
             D818        8-719-109-85       DIODE            RD5.1ESB2                    IC200      6-706-985-01    IC                 AN17808A
             D819        6-500-567-31       DIODE            10ERB20-TB3                  IC601      6-703-472-11    IC                 STR-F6264SLF1357
             D820        8-719-083-20       DIODE            PG102R
             D821        6-500-567-31       DIODE            10ERB20-TB3                  IC602      6-706-789-01    IC                 KIA78R09API
             D823        8-719-074-25       DIODE            PG104R                       IC603      6-703-478-01    IC                 PQ018EF01SSH
                                                                                          IC604      8-759-646-52    IC                 KIA7805API
             D824        8-719-074-25       DIODE            PG104R                       IC605      6-705-063-01    IC                 SE135N-LF38
             D827        8-719-074-25       DIODE            PG104R                       IC606      6-706-886-01    IC                 KIA78D33PI
             D829        8-719-036-94       DIODE            RD5.6SB-T1
             D830        8-719-404-50       DIODE            MA111-TX
        KV-21FS140                                                                                                                                             62
Downloaded from www.Manualslib.com manuals search engine
