nrzimmer/retro-crt/tv/manual/rev_s79aa/pages/page-69.md

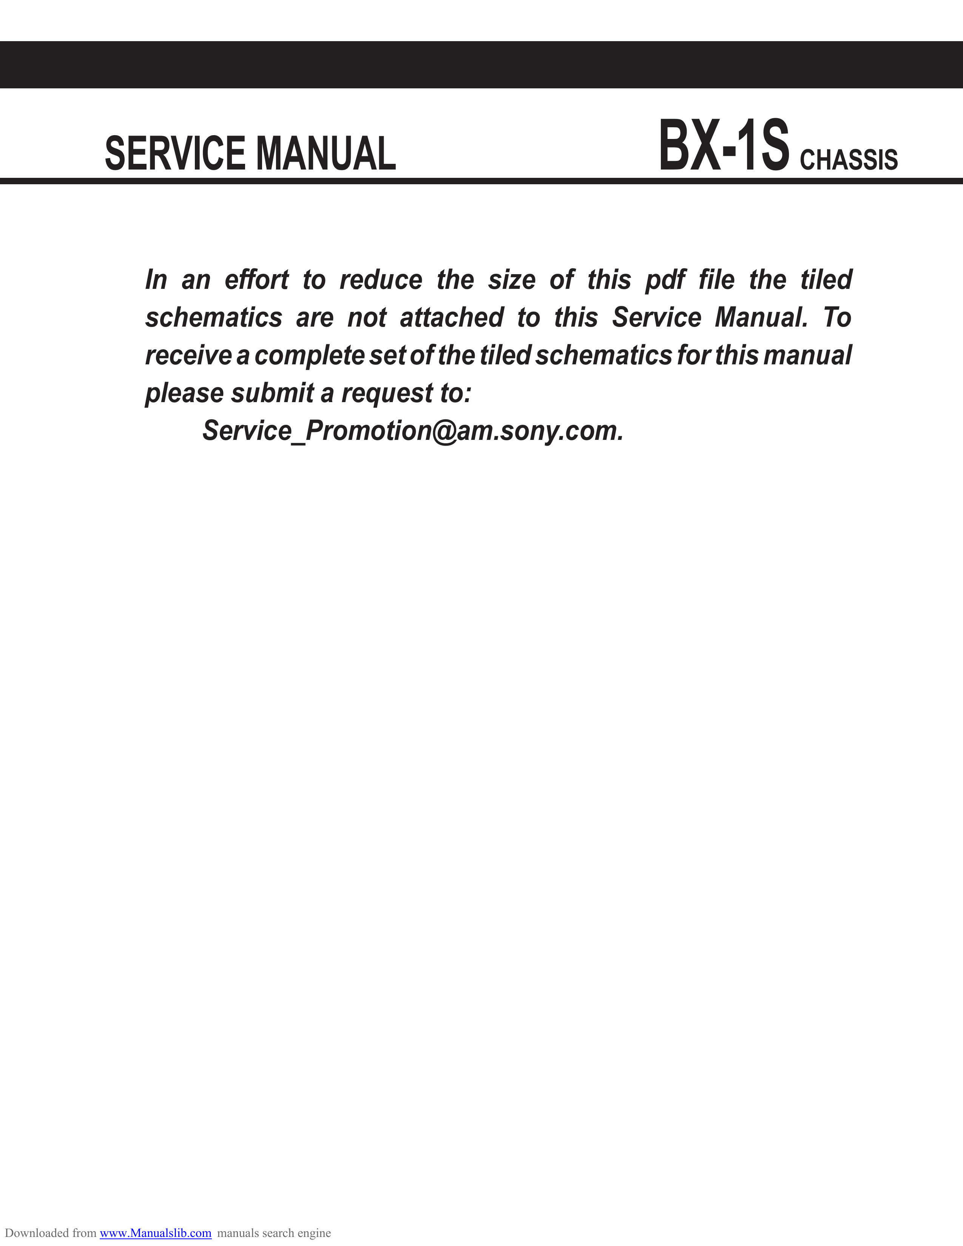
[picture p69: tv/manual/rev_s79aa/pages/img/page-69.png]
page-69


                 SERVICE MANUAL                                     BX-1S        CHASSIS

                        In an effort to reduce the size of this pdf ﬁle the tiled
                        schematics are not attached to this Service Manual. To
                        receive a complete set of the tiled schematics for this manual
                        please submit a request to:
                             Service_Promotion@am.sony.com.

Downloaded from www.Manualslib.com manuals search engine
