nrzimmer/retro-crt/tv/manual/rev_brazil/pages/page-25.md

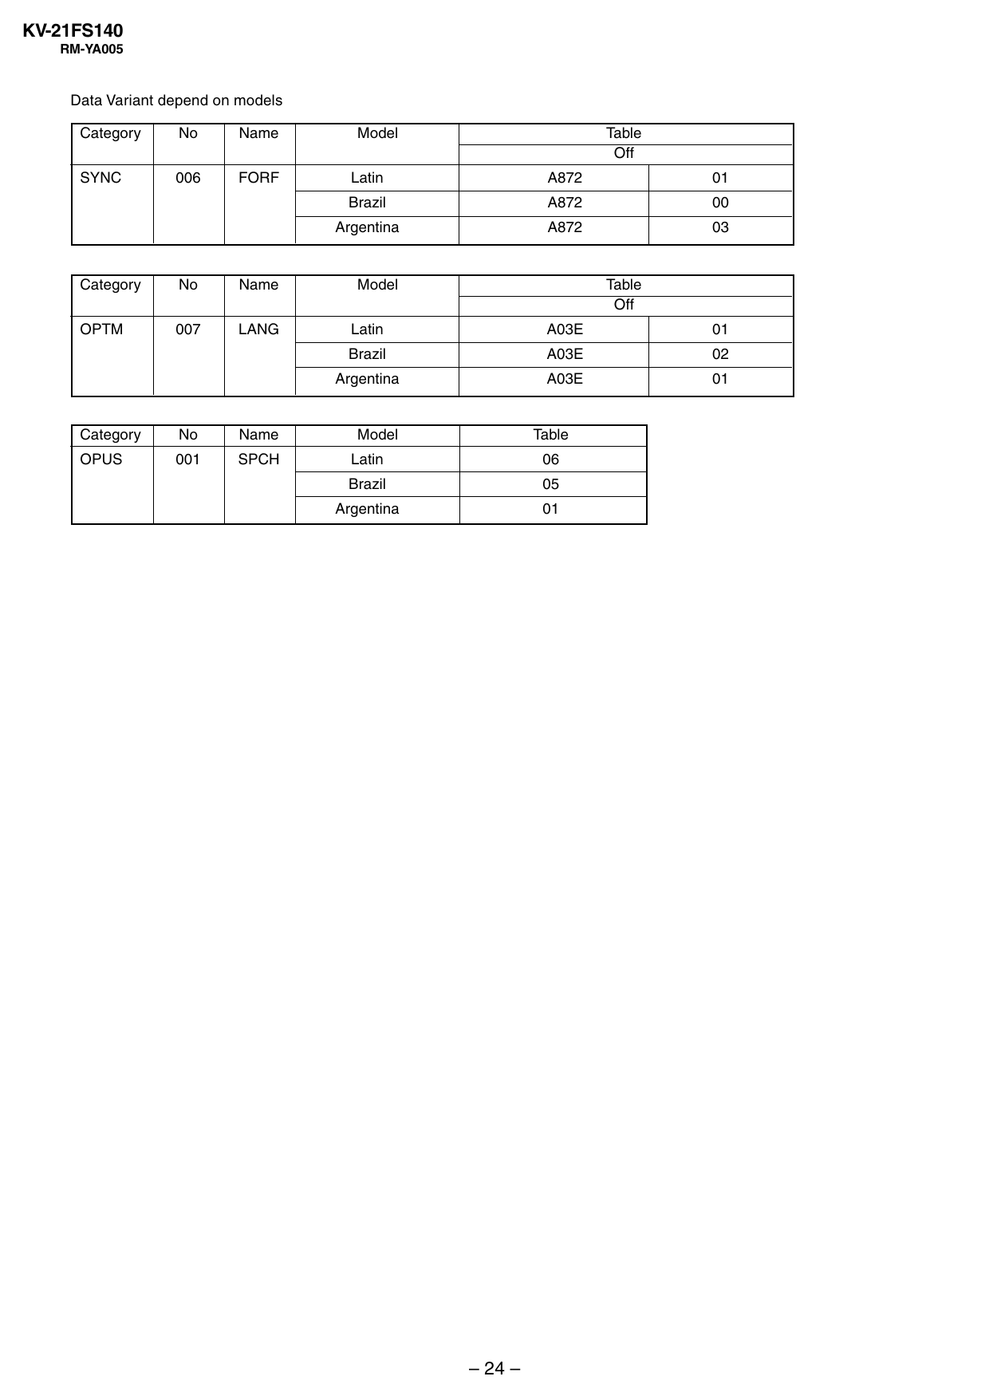
[picture p75: tv/manual/rev_brazil/pages/img/page-25.png]
page-25


KV-21FS140
RM-YA005

Data Variant depend on models
Category

No

Name

Model

SYNC

006

FORF

Latin

A872

01

Brazil

A872

00

Argentina

A872

03

Category

No

Name

Model

OPTM

007

LANG

Latin

Table
Off

Table
Off
A03E

01

Brazil

A03E

02

Argentina

A03E

01

Category

No

Name

Model

Table

OPUS

001

SPCH

Latin

06

Brazil

05

Argentina

01

– 24 –
