nrzimmer/retro-crt/tv/manual/rev_brazil/pages/page-47.md

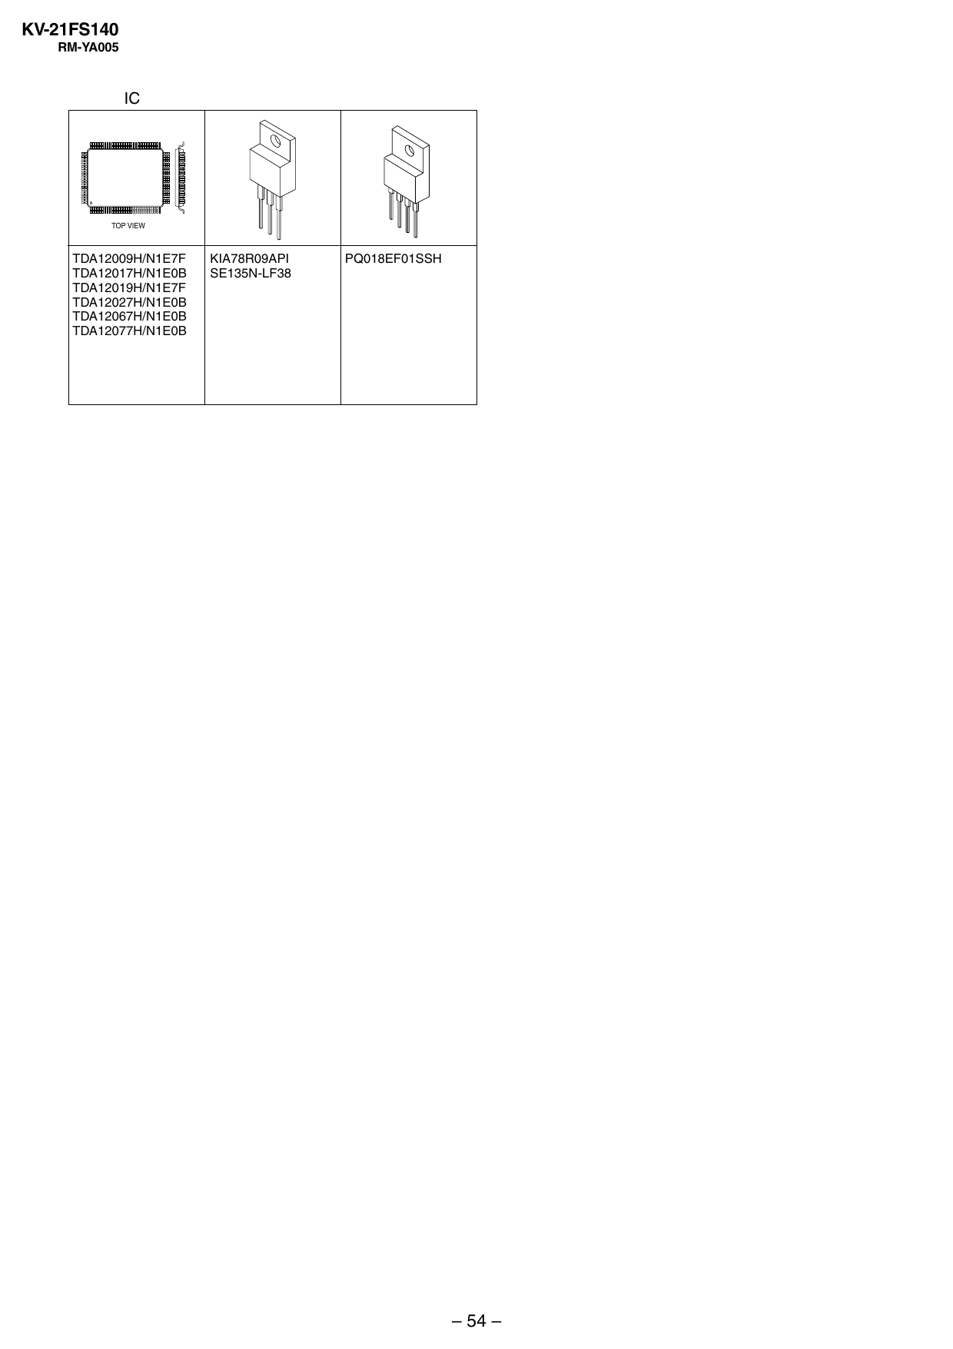
[picture p80: tv/manual/rev_brazil/pages/img/page-47.png]
page-47


KV-21FS140
RM-YA005

IC

TOP VIEW

TDA12009H/N1E7F
TDA12017H/N1E0B
TDA12019H/N1E7F
TDA12027H/N1E0B
TDA12067H/N1E0B
TDA12077H/N1E0B

KIA78R09API
SE135N-LF38

PQ018EF01SSH

– 54 –
