nrzimmer/retro-crt/tv/manual/rev_brazil/pages/page-54.md

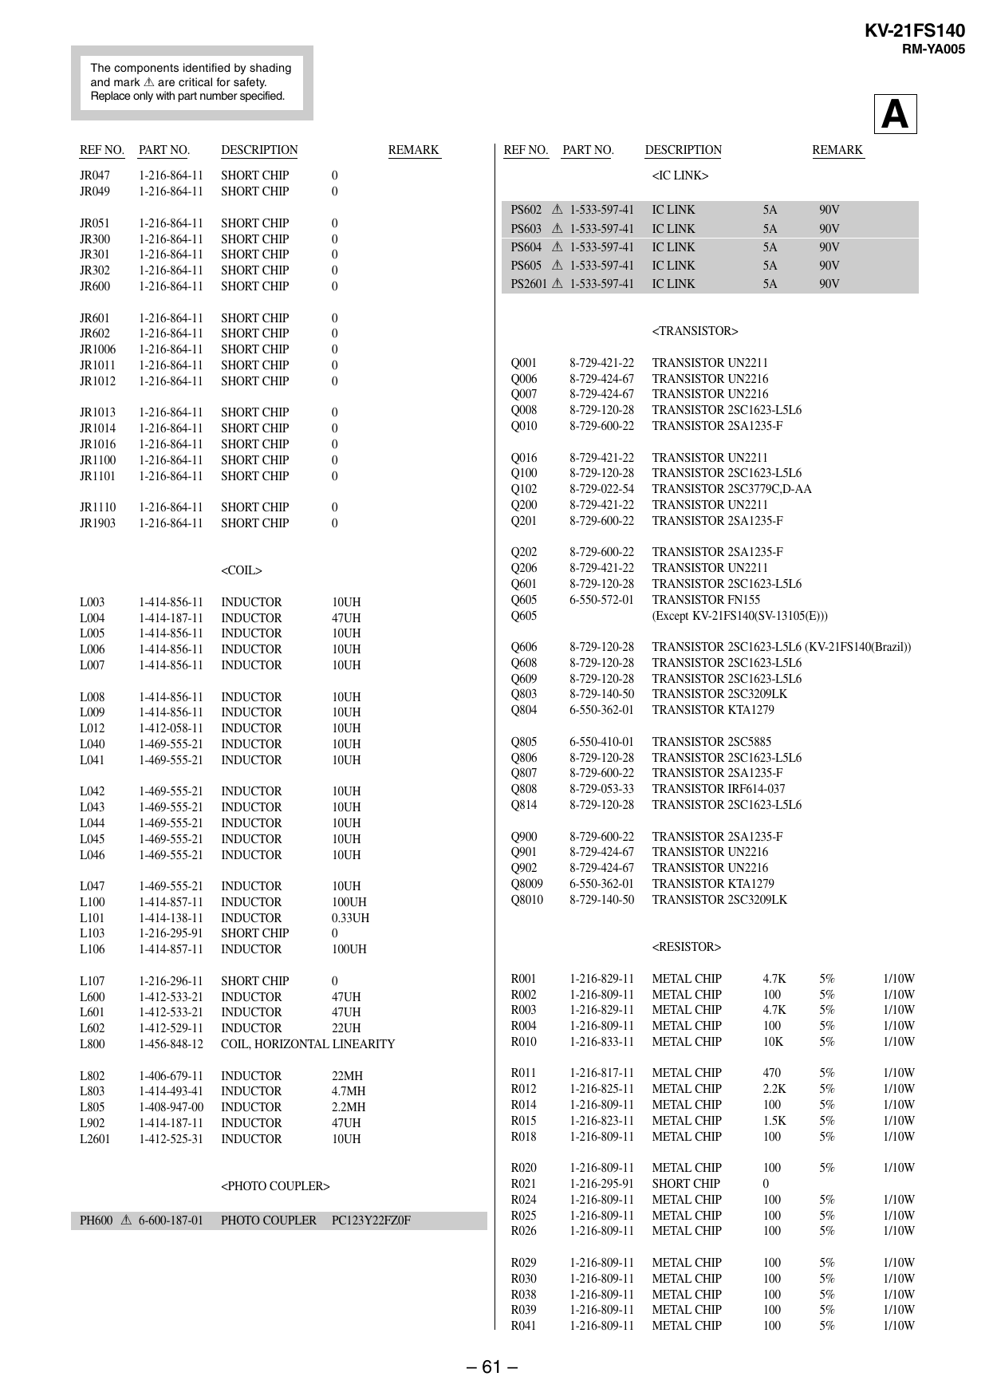
[picture p81: tv/manual/rev_brazil/pages/img/page-54.png]
page-54


KV-21FS140
RM-YA005
The components identified by shading
and mark ! are critical for safety.
Replace only with part number specified.

A

REF NO.

PART NO.

DESCRIPTION

REMARK

JR047
JR049

1-216-864-11
1-216-864-11

SHORT CHIP
SHORT CHIP

0
0

JR051
JR300
JR301
JR302
JR600

1-216-864-11
1-216-864-11
1-216-864-11
1-216-864-11
1-216-864-11

SHORT CHIP
SHORT CHIP
SHORT CHIP
SHORT CHIP
SHORT CHIP

0
0
0
0
0

JR601
JR602
JR1006
JR1011
JR1012

1-216-864-11
1-216-864-11
1-216-864-11
1-216-864-11
1-216-864-11

SHORT CHIP
SHORT CHIP
SHORT CHIP
SHORT CHIP
SHORT CHIP

0
0
0
0
0

JR1013
JR1014
JR1016
JR1100
JR1101

1-216-864-11
1-216-864-11
1-216-864-11
1-216-864-11
1-216-864-11

SHORT CHIP
SHORT CHIP
SHORT CHIP
SHORT CHIP
SHORT CHIP

0
0
0
0
0

JR1110
JR1903

1-216-864-11
1-216-864-11

SHORT CHIP
SHORT CHIP

0
0

<COIL>

REF NO.

PART NO.

DESCRIPTION

REMARK

<IC LINK>
PS602 ! 1-533-597-41
PS603 ! 1-533-597-41
PS604 ! 1-533-597-41
PS605 ! 1-533-597-41
PS2601 ! 1-533-597-41

IC LINK
IC LINK
IC LINK
IC LINK
IC LINK

5A
5A
5A
5A
5A

90V
90V
90V
90V
90V

<TRANSISTOR>
Q001
Q006
Q007
Q008
Q010

8-729-421-22
8-729-424-67
8-729-424-67
8-729-120-28
8-729-600-22

TRANSISTOR UN2211
TRANSISTOR UN2216
TRANSISTOR UN2216
TRANSISTOR 2SC1623-L5L6
TRANSISTOR 2SA1235-F

Q016
Q100
Q102
Q200
Q201

8-729-421-22
8-729-120-28
8-729-022-54
8-729-421-22
8-729-600-22

TRANSISTOR UN2211
TRANSISTOR 2SC1623-L5L6
TRANSISTOR 2SC3779C,D-AA
TRANSISTOR UN2211
TRANSISTOR 2SA1235-F

Q202
Q206
Q601
Q605
Q605

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
1-216-809-11
1-216-809-11
1-216-809-11
1-216-809-11

METAL CHIP
METAL CHIP
METAL CHIP
METAL CHIP
METAL CHIP

100
100
100
100
100

5%
5%
5%
5%
5%

1/10W
1/10W
1/10W
1/10W
1/10W

22MH
4.7MH
2.2MH
47UH
10UH

<PHOTO COUPLER>
PH600 ! 6-600-187-01

PHOTO COUPLER

PC123Y22FZ0F

<RESISTOR>

– 61 –
