nrzimmer/retro-crt/tv/manual/rev_brazil/pages/page-55.md

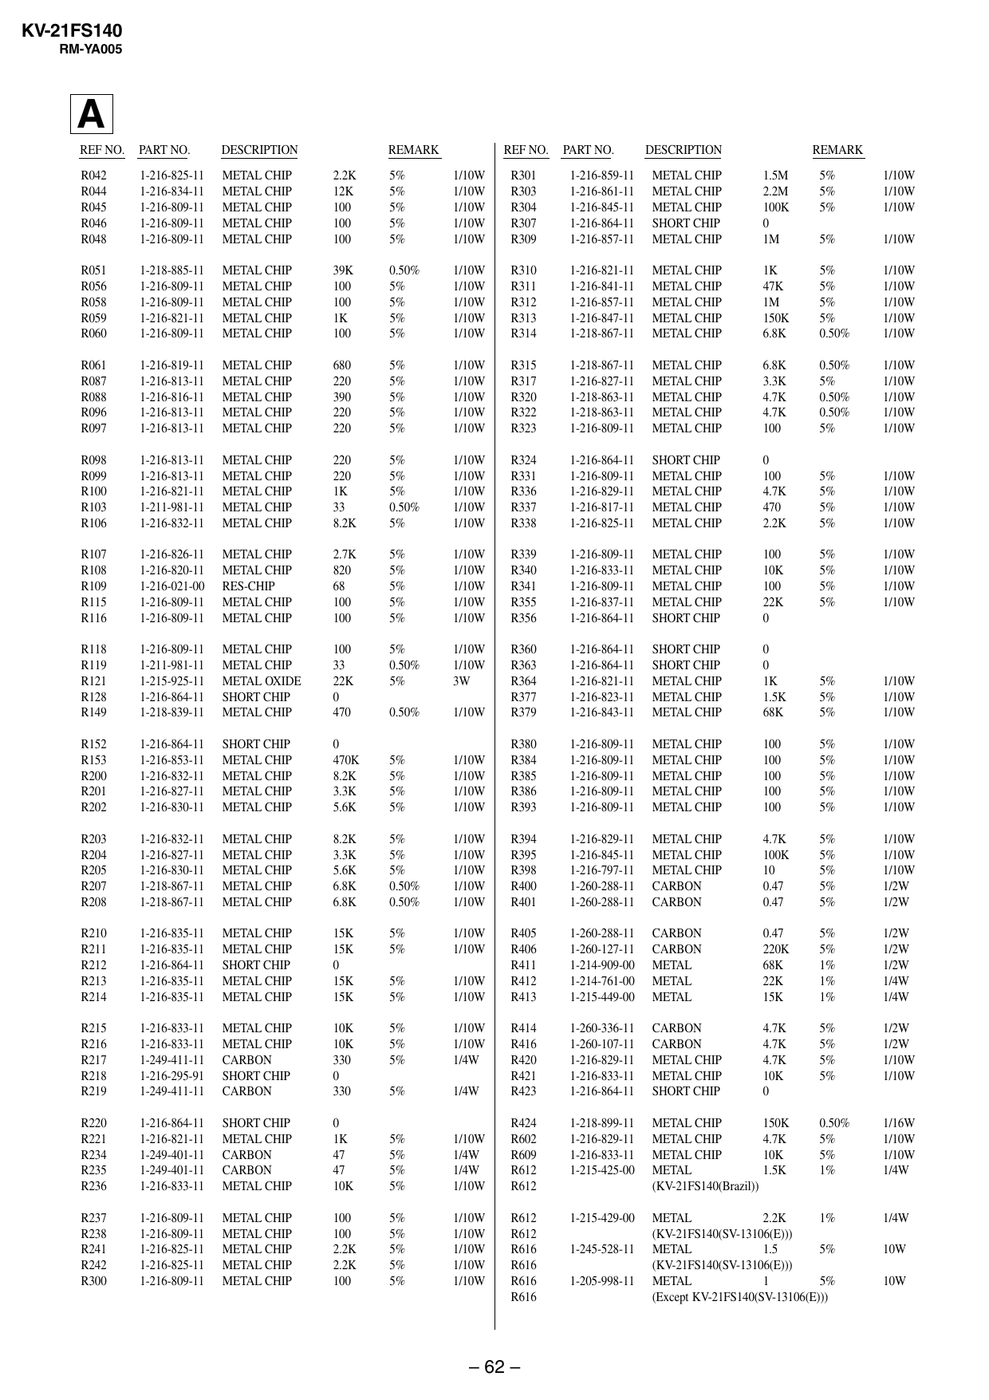
[picture p82: tv/manual/rev_brazil/pages/img/page-55.png]
page-55


KV-21FS140
RM-YA005
The components identified by shading
and mark ! are critical for safety.
Replace only with part number specified.

A
REF NO.

PART NO.

DESCRIPTION

REMARK

REF NO.

PART NO.

DESCRIPTION

R042
R044
R045
R046
R048

1-216-825-11
1-216-834-11
1-216-809-11
1-216-809-11
1-216-809-11

METAL CHIP
METAL CHIP
METAL CHIP
METAL CHIP
METAL CHIP

2.2K
12K
100
100
100

5%
5%
5%
5%
5%

R051
R056
R058
R059
R060

1-218-885-11
1-216-809-11
1-216-809-11
1-216-821-11
1-216-809-11

METAL CHIP
METAL CHIP
METAL CHIP
METAL CHIP
METAL CHIP

39K
100
100
1K
100

R061
R087
R088
R096
R097

1-216-819-11
1-216-813-11
1-216-816-11
1-216-813-11
1-216-813-11

METAL CHIP
METAL CHIP
METAL CHIP
METAL CHIP
METAL CHIP

R098
R099
R100
R103
R106

1-216-813-11
1-216-813-11
1-216-821-11
1-211-981-11
1-216-832-11

R107
R108
R109
R115
R116

1/10W
1/10W
1/10W
1/10W
1/10W

R301
R303
R304
R307
R309

1-216-859-11
1-216-861-11
1-216-845-11
1-216-864-11
1-216-857-11

METAL CHIP
METAL CHIP
METAL CHIP
SHORT CHIP
METAL CHIP

1.5M
2.2M
100K
0
1M

5%
5%
5%

1/10W
1/10W
1/10W

5%

1/10W

0.50%
5%
5%
5%
5%

1/10W
1/10W
1/10W
1/10W
1/10W

R310
R311
R312
R313
R314

1-216-821-11
1-216-841-11
1-216-857-11
1-216-847-11
1-218-867-11

METAL CHIP
METAL CHIP
METAL CHIP
METAL CHIP
METAL CHIP

1K
47K
1M
150K
6.8K

5%
5%
5%
5%
0.50%

1/10W
1/10W
1/10W
1/10W
1/10W

680
220
390
220
220

5%
5%
5%
5%
5%

1/10W
1/10W
1/10W
1/10W
1/10W

R315
R317
R320
R322
R323

1-218-867-11
1-216-827-11
1-218-863-11
1-218-863-11
1-216-809-11

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

100
100
2.2K
2.2K
100

5%
5%
5%
5%
5%

1/10W
1/10W
1/10W
1/10W
1/10W

R612
R612
R616
R616
R616
R616

1-215-429-00

METAL
2.2K
1%
(KV-21FS140(SV-13106(E)))
METAL
1.5
5%
(KV-21FS140(SV-13106(E)))
METAL
1
5%
(Except KV-21FS140(SV-13106(E)))

– 62 –

1-245-528-11
1-205-998-11

REMARK

1/4W
10W
10W
