nrzimmer/retro-crt/tv/manual/rev_brazil/pages/page-56.md

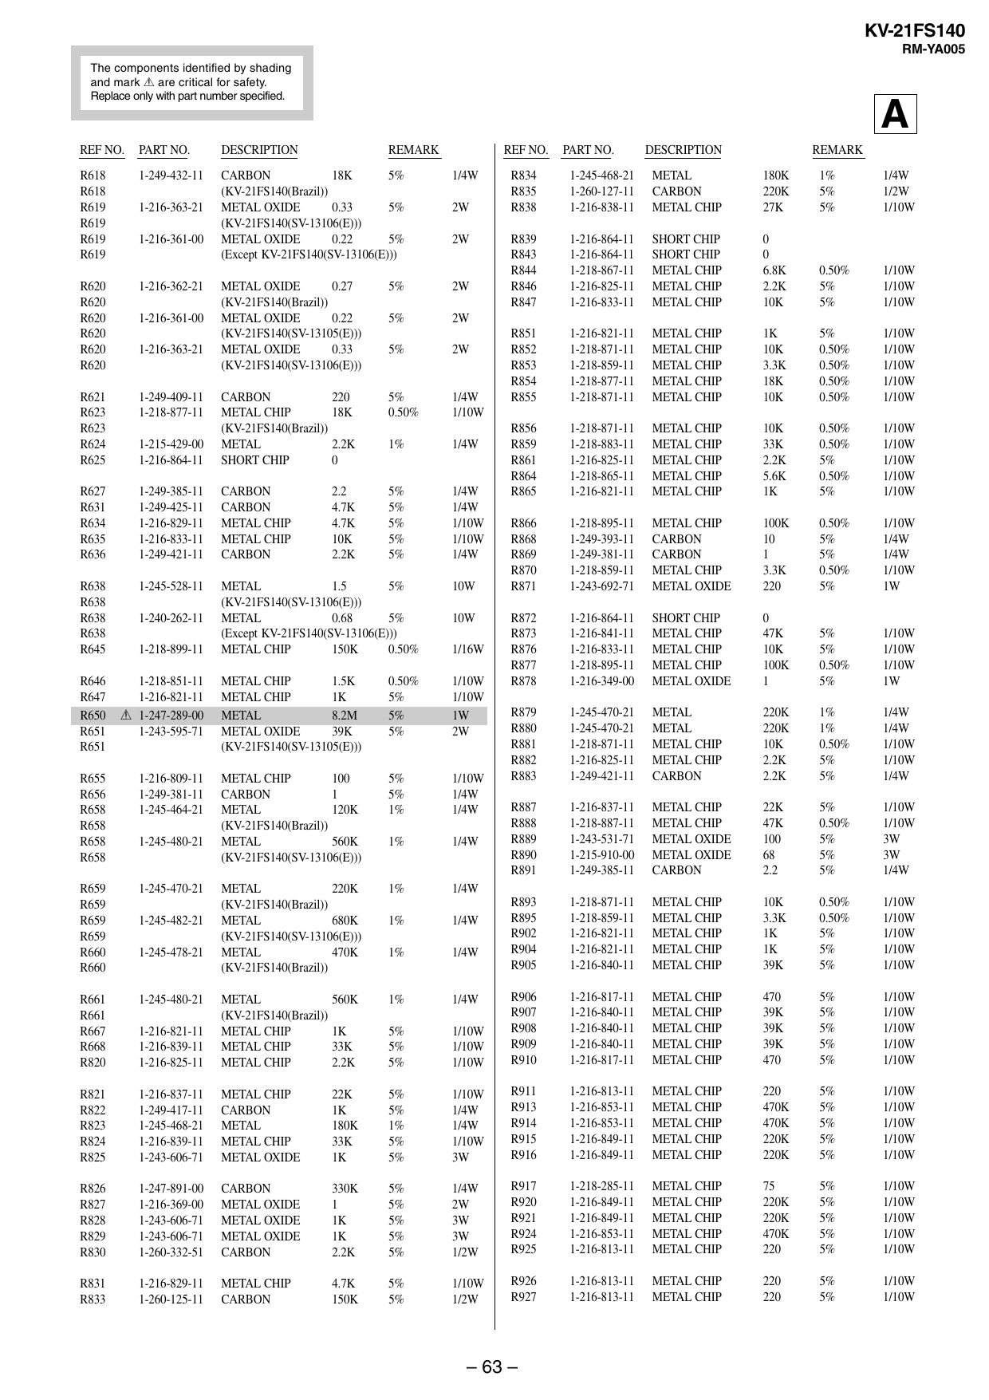
[picture p83: tv/manual/rev_brazil/pages/img/page-56.png]
page-56


KV-21FS140
RM-YA005
The components identified by shading
and mark ! are critical for safety.
Replace only with part number specified.

A

REF NO.

PART NO.

DESCRIPTION

R618
R618
R619
R619
R619
R619

1-249-432-11

CARBON
18K
5%
(KV-21FS140(Brazil))
METAL OXIDE
0.33
5%
(KV-21FS140(SV-13106(E)))
METAL OXIDE
0.22
5%
(Except KV-21FS140(SV-13106(E)))

1/4W

METAL OXIDE
0.27
(KV-21FS140(Brazil))
METAL OXIDE
0.22
(KV-21FS140(SV-13105(E)))
METAL OXIDE
0.33
(KV-21FS140(SV-13106(E)))

5%

2W

5%

2W

5%

2W

5%
0.50%

1/4W
1/10W

1%

1/4W

5%
5%
5%
5%
5%

1/4W
1/4W
1/10W
1/10W
1/4W

1-216-363-21
1-216-361-00

REMARK

R620
R620
R620
R620
R620
R620

1-216-362-21

R621
R623
R623
R624
R625

1-249-409-11
1-218-877-11
1-215-429-00
1-216-864-11

CARBON
220
METAL CHIP
18K
(KV-21FS140(Brazil))
METAL
2.2K
SHORT CHIP
0

R627
R631
R634
R635
R636

1-249-385-11
1-249-425-11
1-216-829-11
1-216-833-11
1-249-421-11

CARBON
CARBON
METAL CHIP
METAL CHIP
CARBON

R638
R638
R638
R638
R645

1-245-528-11

METAL
1.5
5%
(KV-21FS140(SV-13106(E)))
METAL
0.68
5%
(Except KV-21FS140(SV-13106(E)))
METAL CHIP
150K
0.50%

1-216-361-00
1-216-363-21

1-240-262-11
1-218-899-11

2.2
4.7K
4.7K
10K
2.2K

2W
2W

10W
10W
1/16W

REF NO.

PART NO.

DESCRIPTION

REMARK

R834
R835
R838

1-245-468-21
1-260-127-11
1-216-838-11

METAL
CARBON
METAL CHIP

180K
220K
27K

1%
5%
5%

1/4W
1/2W
1/10W

R839
R843
R844
R846
R847

1-216-864-11
1-216-864-11
1-218-867-11
1-216-825-11
1-216-833-11

SHORT CHIP
SHORT CHIP
METAL CHIP
METAL CHIP
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

75
220K
220K
470K
220

5%
5%
5%
5%
5%

1/10W
1/10W
1/10W
1/10W
1/10W

R831
R833

1-216-829-11
1-260-125-11

METAL CHIP
CARBON

4.7K
150K

5%
5%

1/10W
1/2W

R926
R927

1-216-813-11
1-216-813-11

METAL CHIP
METAL CHIP

220
220

5%
5%

1/10W
1/10W

1-245-480-21

1-245-482-21
1-245-478-21

– 63 –
