nrzimmer/retro-crt/tv/manual/rev_s79aa/pages/page-02.md

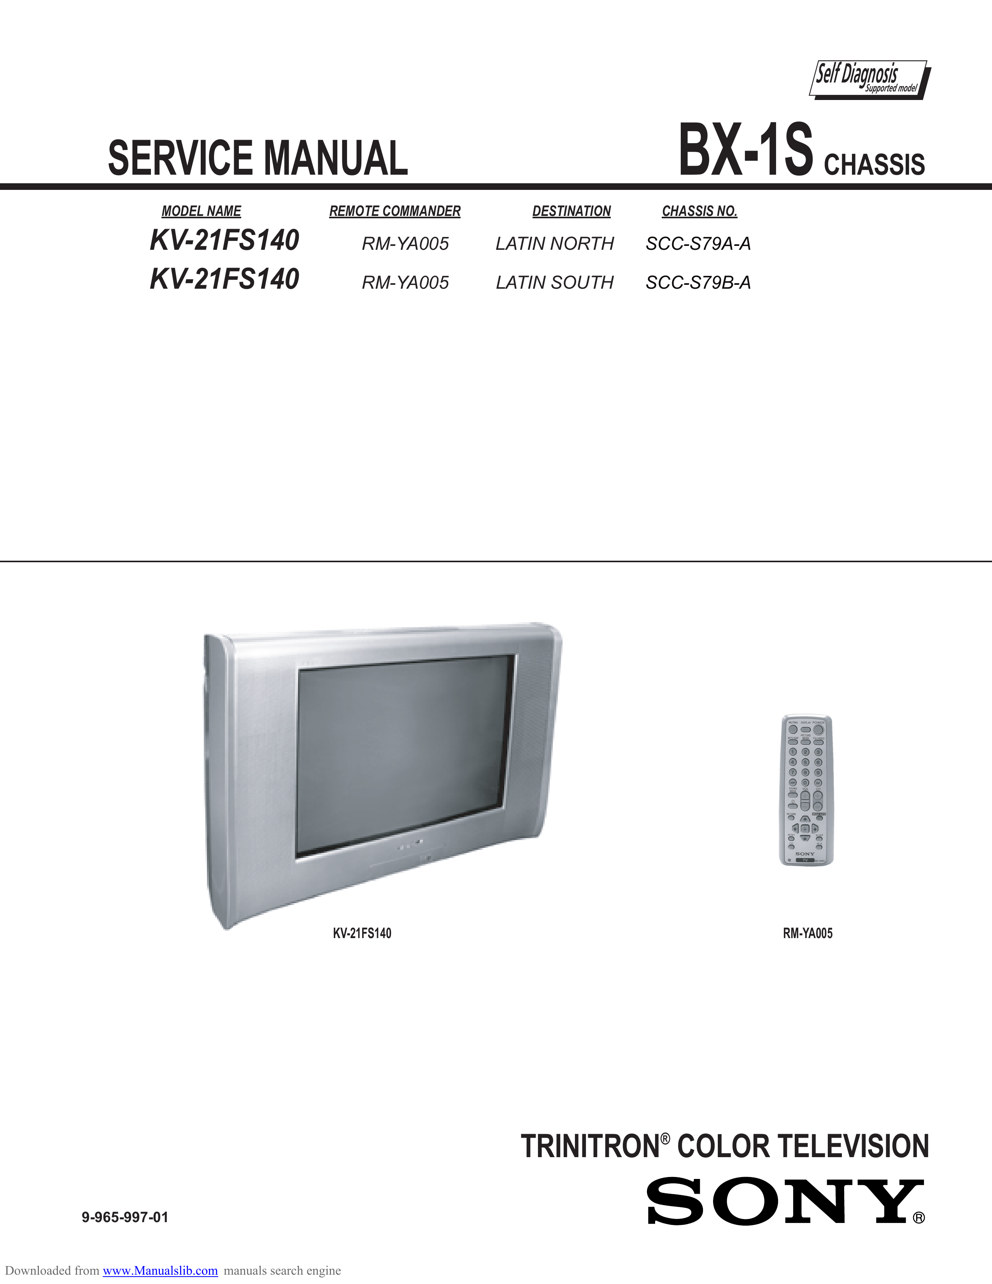
[picture p85: tv/manual/rev_s79aa/pages/img/page-02.png]
page-02


                                                                                                              Self Diagnosis
                                                                                                                      Supported model

                 SERVICE MANUAL                                                              BX-1S             CHASSIS
                          MODEL NAME                  REMOTE COMMANDER      DESTINATION    CHASSIS NO.

                        KV-21FS140                         RM-YA005      LATIN NORTH      SCC-S79A-A

                        KV-21FS140                         RM-YA005      LATIN SOUTH      SCC-S79B-A

                                                      KV-21FS140                                         RM-YA005

                                                                           TRINITRON® COLOR TELEVISION
            9-965-997-01

Downloaded from www.Manualslib.com manuals search engine
