nrzimmer/retro-crt/tv/manual/rev_s79aa/pages/page-17.md

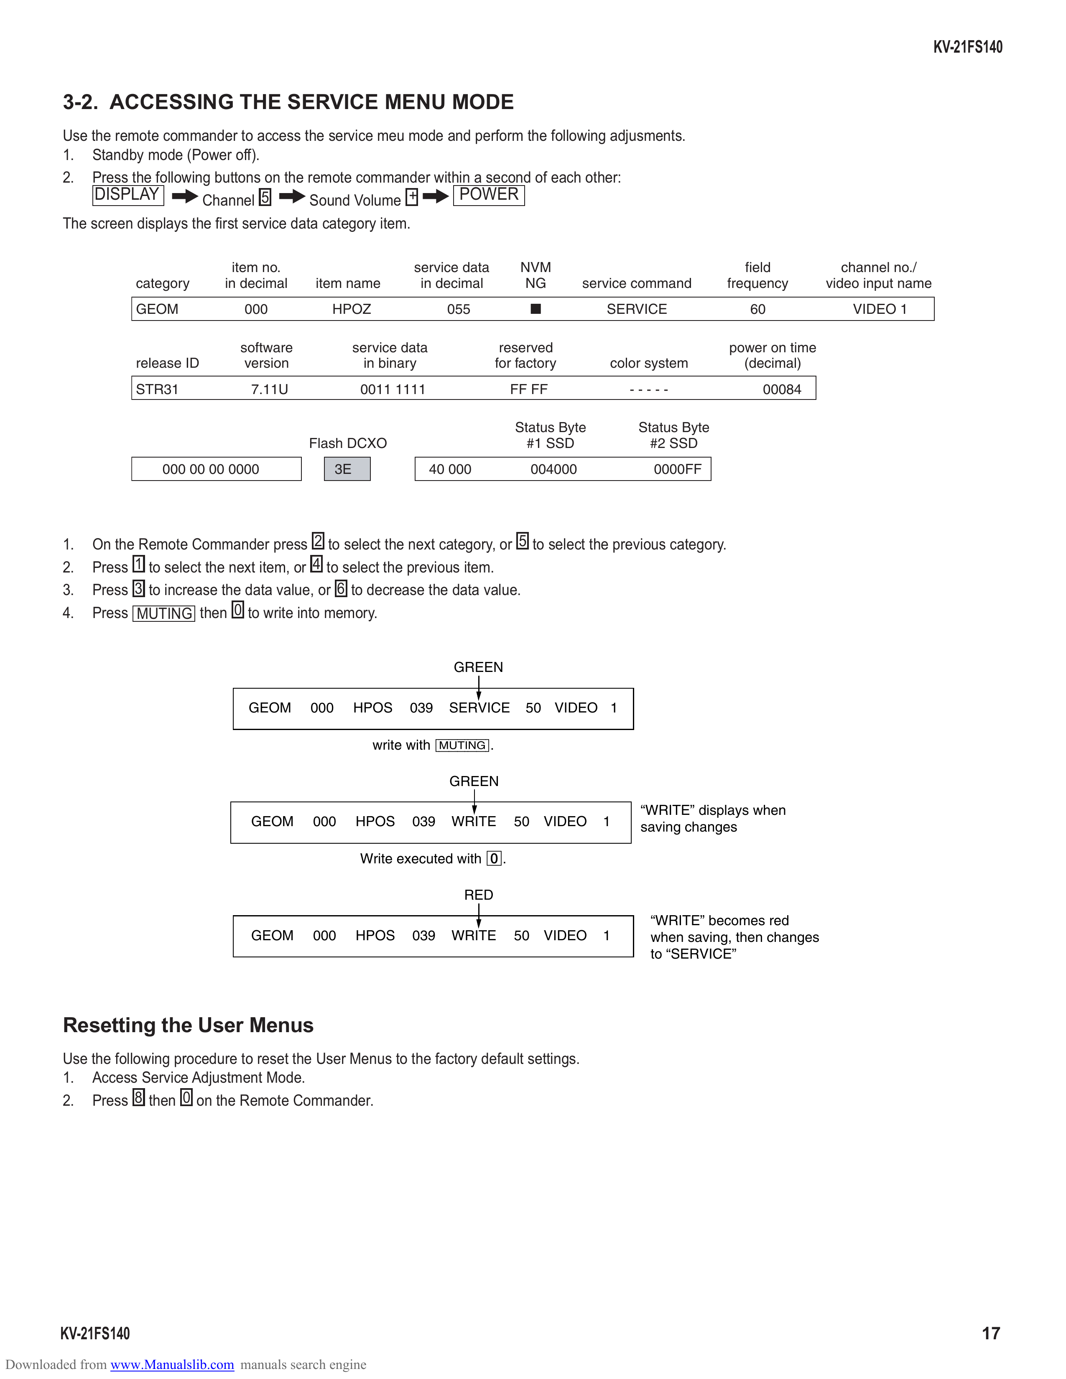
[picture p90: tv/manual/rev_s79aa/pages/img/page-17.png]
page-17


                                                                                                                                                               KV-21FS140

        3-2. ACCESSING THE SERVICE MENU MODE
        Use the remote commander to access the service meu mode and perform the following adjusments.
        1. Standby mode (Power off).
        2. Press the following buttons on the remote commander within a second of each other:
             DISPLAY          Channel 5         Sound Volume +     POWER
        The screen displays the ﬁrst service data category item.

                                   item no.                         service data         NVM                                   field           channel no./
                     category     in decimal     item name           in decimal           NG          service command       frequency       video input name
                     GEOM            000           HPOZ                     055              x           SERVICE               60               VIDEO 1

                                    software               service data               reserved                              power on time
                     release ID      version                 in binary               for factory         color system         (decimal)
                     STR31            7.11U                 0011 1111                  FF FF                 -----               00084

                                                                                        Status Byte           Status Byte
                                               Flash DCXO                                 #1 SSD                #2 SSD
                         000 00 00 0000               3E                  40 000             004000             0000FF

        1.   On the Remote Commander press 2 to select the next category, or 5 to select the previous category.
        2.   Press 1 to select the next item, or 4 to select the previous item.
        3.   Press 3 to increase the data value, or 6 to decrease the data value.
        4.   Press MUTING then 0 to write into memory.

                                                                             GREEN

                                      GEOM      000        HPOS     039     SERVICE       50 VIDEO 1

                                                              write with [MUTING].

                                                                            GREEN

                                                                                                              “WRITE” displays when
                                      GEOM      000        HPOS     039      WRITE      50       VIDEO   1    saving changes

                                                            Write executed with -.

                                                                              RED
                                                                                                               “WRITE” becomes red
                                      GEOM      000        HPOS     039      WRITE      50       VIDEO   1     when saving, then changes
                                                                                                               to “SERVICE”

        Resetting the User Menus
        Use the following procedure to reset the User Menus to the factory default settings.
        1. Access Service Adjustment Mode.
        2. Press 8 then 0 on the Remote Commander.

        KV-21FS140                                                                                                                                                   17
Downloaded from www.Manualslib.com manuals search engine
