nrzimmer/retro-crt/tv/manual/rev_s79aa/pages/page-18.md

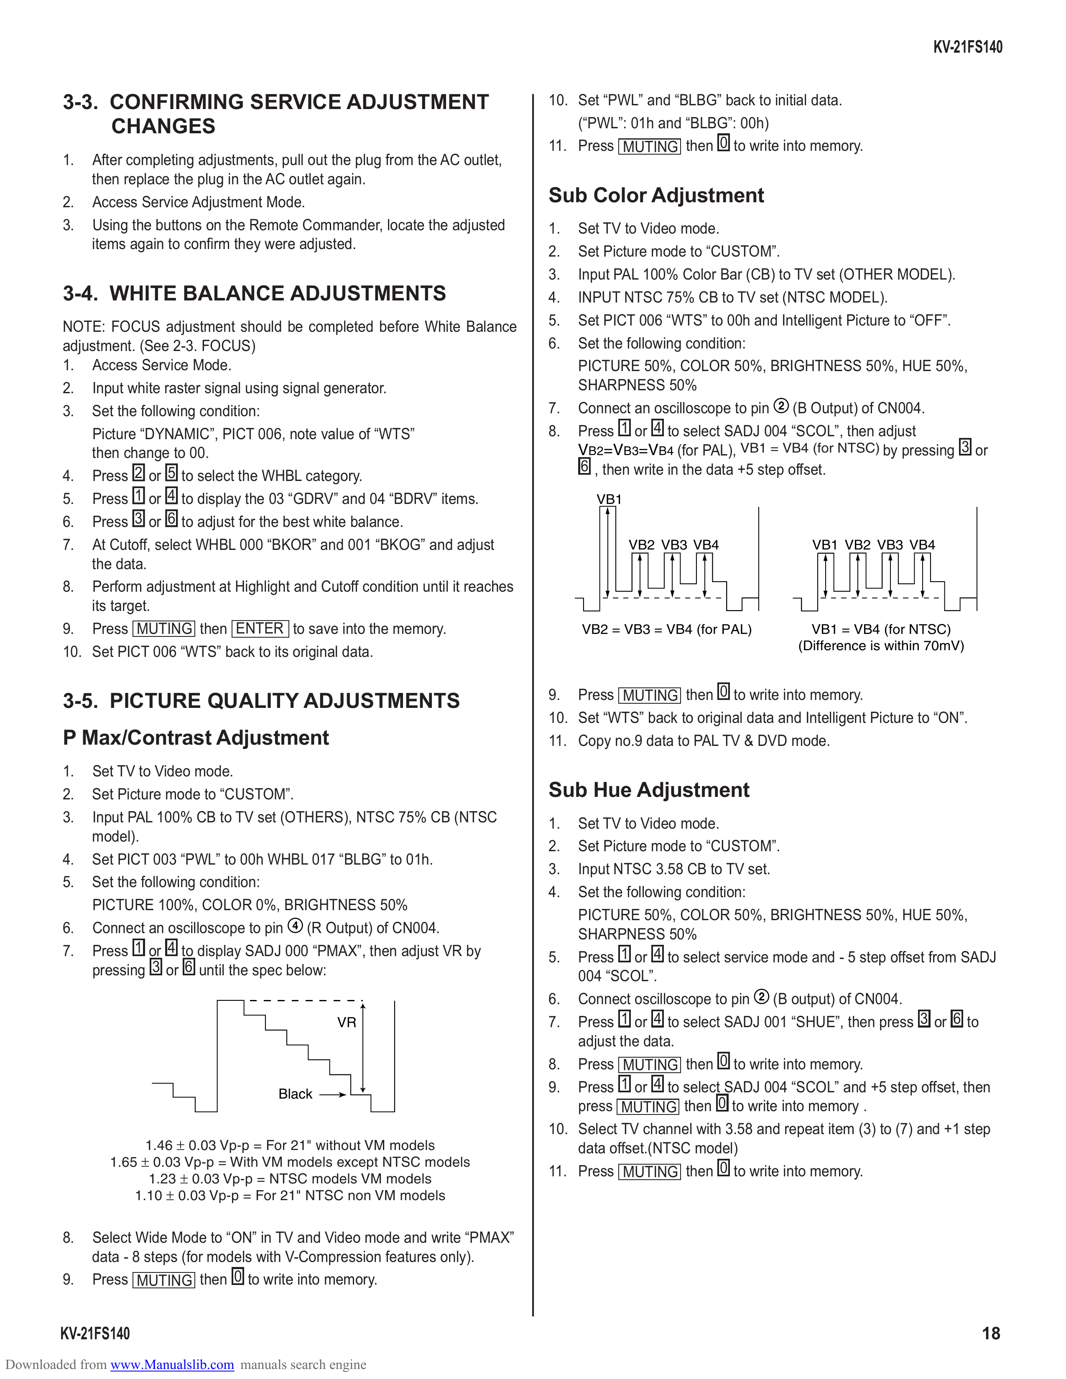
[picture p91: tv/manual/rev_s79aa/pages/img/page-18.png]
page-18


                                                                                                                                                 KV-21FS140

        3-3. CONFIRMING SERVICE ADJUSTMENT                                         10. Set “PWL” and “BLBG” back to initial data.
             CHANGES                                                                   (“PWL”: 01h and “BLBG”: 00h)
                                                                                   11. Press MUTING then 0 to write into memory.
        1.   After completing adjustments, pull out the plug from the AC outlet,
             then replace the plug in the AC outlet again.
        2.   Access Service Adjustment Mode.                                       Sub Color Adjustment
        3.   Using the buttons on the Remote Commander, locate the adjusted        1.   Set TV to Video mode.
             items again to conﬁrm they were adjusted.                             2.   Set Picture mode to “CUSTOM”.
                                                                                   3.   Input PAL 100% Color Bar (CB) to TV set (OTHER MODEL).
        3-4. WHITE BALANCE ADJUSTMENTS                                             4.   INPUT NTSC 75% CB to TV set (NTSC MODEL).
        NOTE: FOCUS adjustment should be completed before White Balance            5.   Set PICT 006 “WTS” to 00h and Intelligent Picture to “OFF”.
        adjustment. (See 2-3. FOCUS)                                               6.   Set the following condition:
        1. Access Service Mode.                                                         PICTURE 50%, COLOR 50%, BRIGHTNESS 50%, HUE 50%,
        2. Input white raster signal using signal generator.                            SHARPNESS 50%
        3. Set the following condition:                                            7.   Connect an oscilloscope to pin 2 (B Output) of CN004.
            Picture “DYNAMIC”, PICT 006, note value of “WTS”                       8.   Press 1 or 4 to select SADJ 004 “SCOL”, then adjust
            then change to 00.                                                          VB2=VB3=VB4 (for PAL), VB1 = VB4 (for NTSC) by pressing 3 or
                                                                                         6 , then write in the data +5 step offset.
        4. Press 2 or 5 to select the WHBL category.
        5. Press 1 or 4 to display the 03 “GDRV” and 04 “BDRV” items.                     VB1
        6. Press 3 or 6 to adjust for the best white balance.
        7. At Cutoff, select WHBL 000 “BKOR” and 001 “BKOG” and adjust                          VB2 VB3 VB4                  VB1 VB2 VB3 VB4
            the data.
        8. Perform adjustment at Highlight and Cutoff condition until it reaches
            its target.
        9. Press MUTING then ENTER to save into the memory.                             VB2 = VB3 = VB4 (for PAL)            VB1 = VB4 (for NTSC)
        10. Set PICT 006 “WTS” back to its original data.                                                                  (Difference is within 70mV)

                                                                                   9. Press MUTING then 0 to write into memory.
        3-5. PICTURE QUALITY ADJUSTMENTS
                                                                                   10. Set “WTS” back to original data and Intelligent Picture to “ON”.
        P Max/Contrast Adjustment                                                  11. Copy no.9 data to PAL TV & DVD mode.
        1.   Set TV to Video mode.
        2.   Set Picture mode to “CUSTOM”.                                         Sub Hue Adjustment
        3.   Input PAL 100% CB to TV set (OTHERS), NTSC 75% CB (NTSC               1.  Set TV to Video mode.
             model).
                                                                                   2.  Set Picture mode to “CUSTOM”.
        4.   Set PICT 003 “PWL” to 00h WHBL 017 “BLBG” to 01h.
                                                                                   3.  Input NTSC 3.58 CB to TV set.
        5.   Set the following condition:
                                                                                   4.  Set the following condition:
             PICTURE 100%, COLOR 0%, BRIGHTNESS 50%
                                                                                       PICTURE 50%, COLOR 50%, BRIGHTNESS 50%, HUE 50%,
        6.   Connect an oscilloscope to pin 4 (R Output) of CN004.                     SHARPNESS 50%
        7.   Press 1 or 4 to display SADJ 000 “PMAX”, then adjust VR by            5. Press 1 or 4 to select service mode and - 5 step offset from SADJ
             pressing 3 or 6 until the spec below:                                     004 “SCOL”.
                                                                                   6. Connect oscilloscope to pin 2 (B output) of CN004.
                                                    VR                             7. Press 1 or 4 to select SADJ 001 “SHUE”, then press 3 or 6 to
                                                                                       adjust the data.
                                                                                   8. Press MUTING then 0 to write into memory.
                                           Black                                   9. Press 1 or 4 to select SADJ 004 “SCOL” and +5 step offset, then
                                                                                       press MUTING then 0 to write into memory .
                                                                                   10. Select TV channel with 3.58 and repeat item (3) to (7) and +1 step
                      1.46 ± 0.03 Vp-p = For 21" without VM models                     data offset.(NTSC model)
                1.65 ± 0.03 Vp-p = With VM models except NTSC models
                      1.23 ± 0.03 Vp-p = NTSC models VM models
                                                                                   11. Press MUTING then 0 to write into memory.
                    1.10 ± 0.03 Vp-p = For 21" NTSC non VM models

        8.   Select Wide Mode to “ON” in TV and Video mode and write “PMAX”
             data - 8 steps (for models with V-Compression features only).
        9.   Press MUTING then 0 to write into memory.

        KV-21FS140                                                                                                                                        18
Downloaded from www.Manualslib.com manuals search engine
