nrzimmer/retro-crt/tv/manual/rev_s79aa/pages/page-36.md

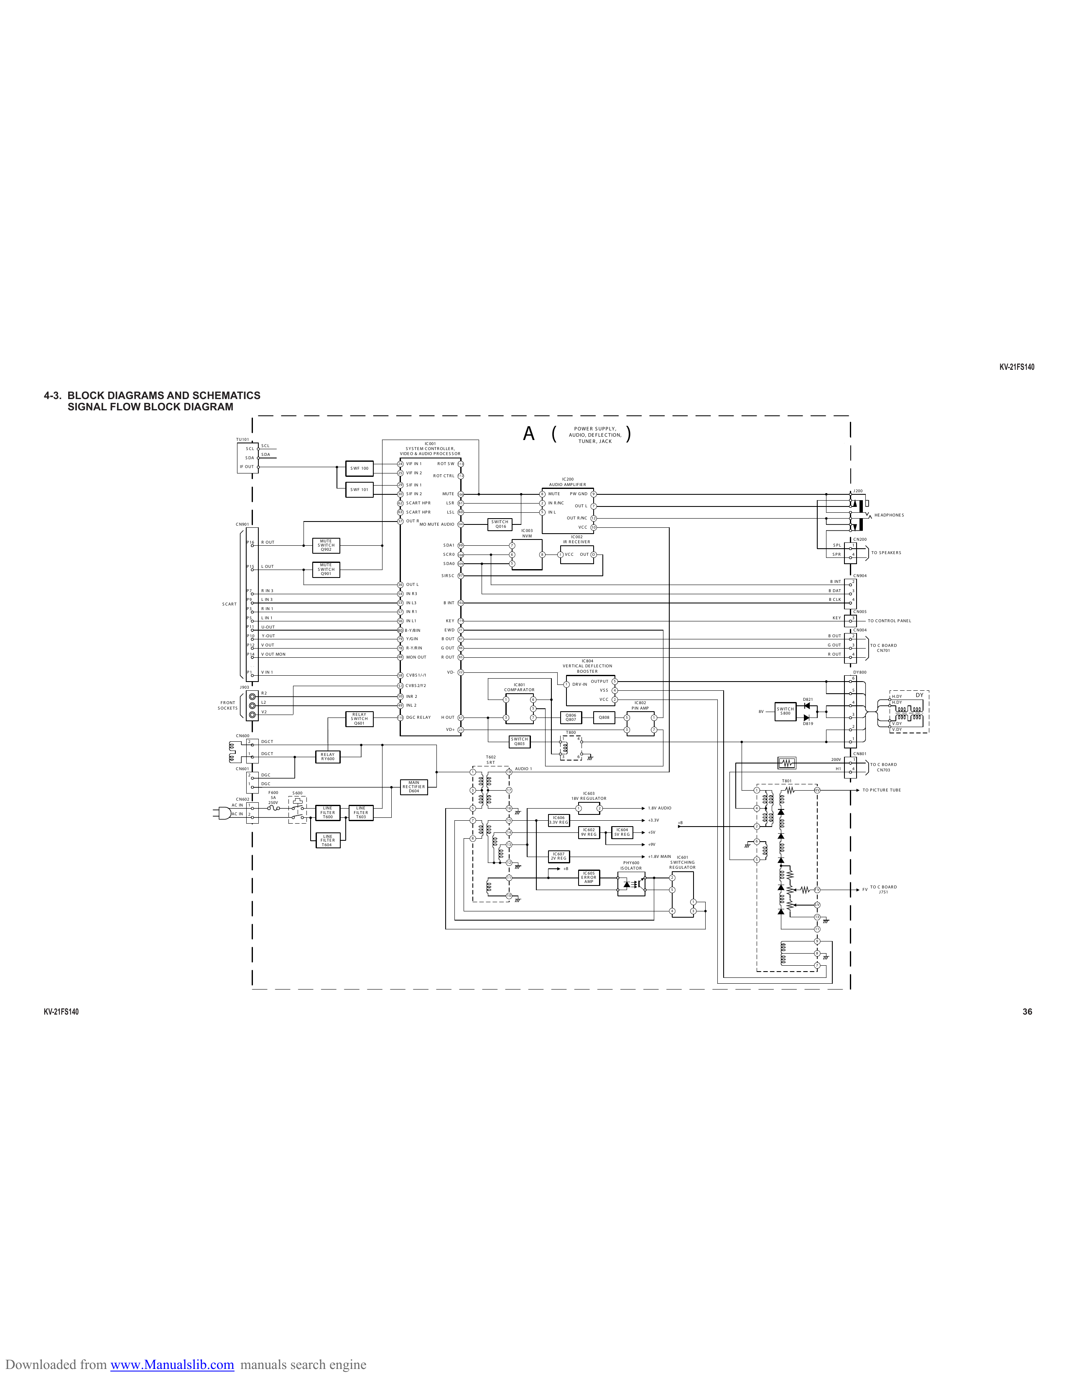
[picture p108: tv/manual/rev_s79aa/pages/img/page-36.png]
page-36


                                                                                                                                                                                                                                                                                                                                                                         KV-21FS140

     4-3. BLOCK DIAGRAMS AND SCHEMATICS
          SIGNAL FLOW BLOCK DIAGRAM

                                           T U101

                                                  SCL
                                                         SCL                                                             IC 001
                                                                                                             S Y S T E M C ONT R OLLE R ,
                                                                                                                                                                             A (                                 P OW E R S UP P LY ,
                                                                                                                                                                                                                AUDIO, DE F LE C T ION,
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

     KV-21FS140                                                                                                                                                                                                                                                                                                                                                                36

Downloaded from www.Manualslib.com manuals search engine
