nrzimmer/retro-crt/tv/manual/rev_s79aa/pages/page-37.md

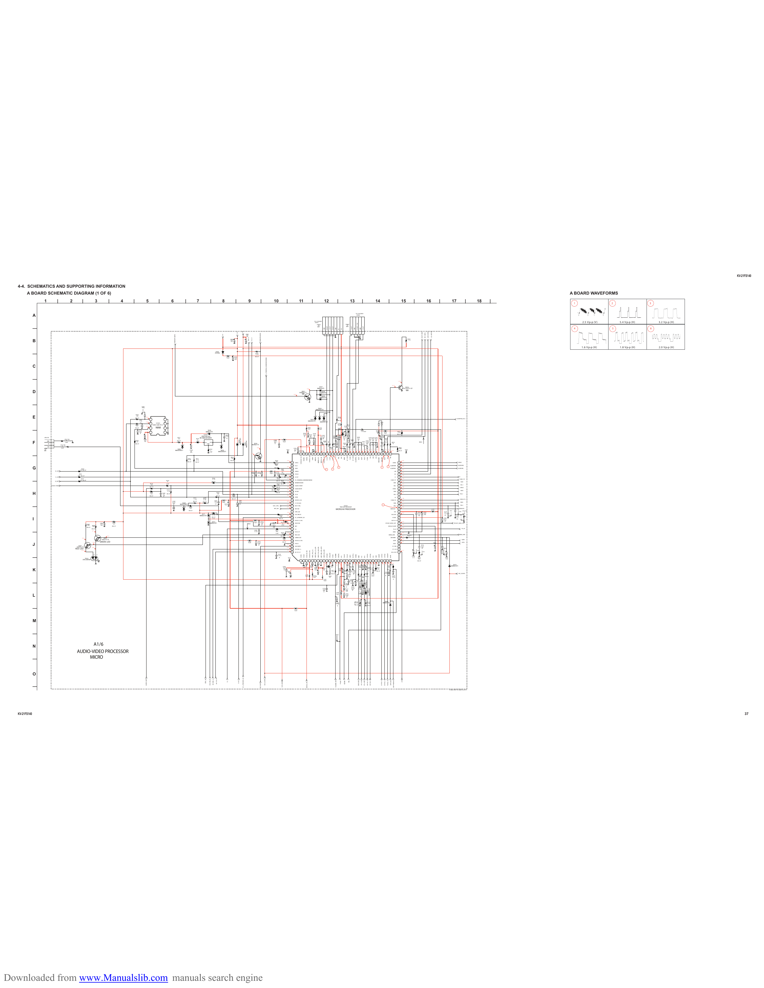
[picture p109: tv/manual/rev_s79aa/pages/img/page-37.png]
page-37


                                                                                                                                                                                                                                                                                                                                                                                                                                                                                                                                                                                                                                                                                                                                                                                                                                                                                                                                                                                                                                                                                                                                                                                                                                                                                                                                                         KV-21FS140

   4-4. SCHEMATICS AND SUPPORTING INFORMATION
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
