nrzimmer/retro-crt/tv/manual/rev_s79aa/pages/page-38.md

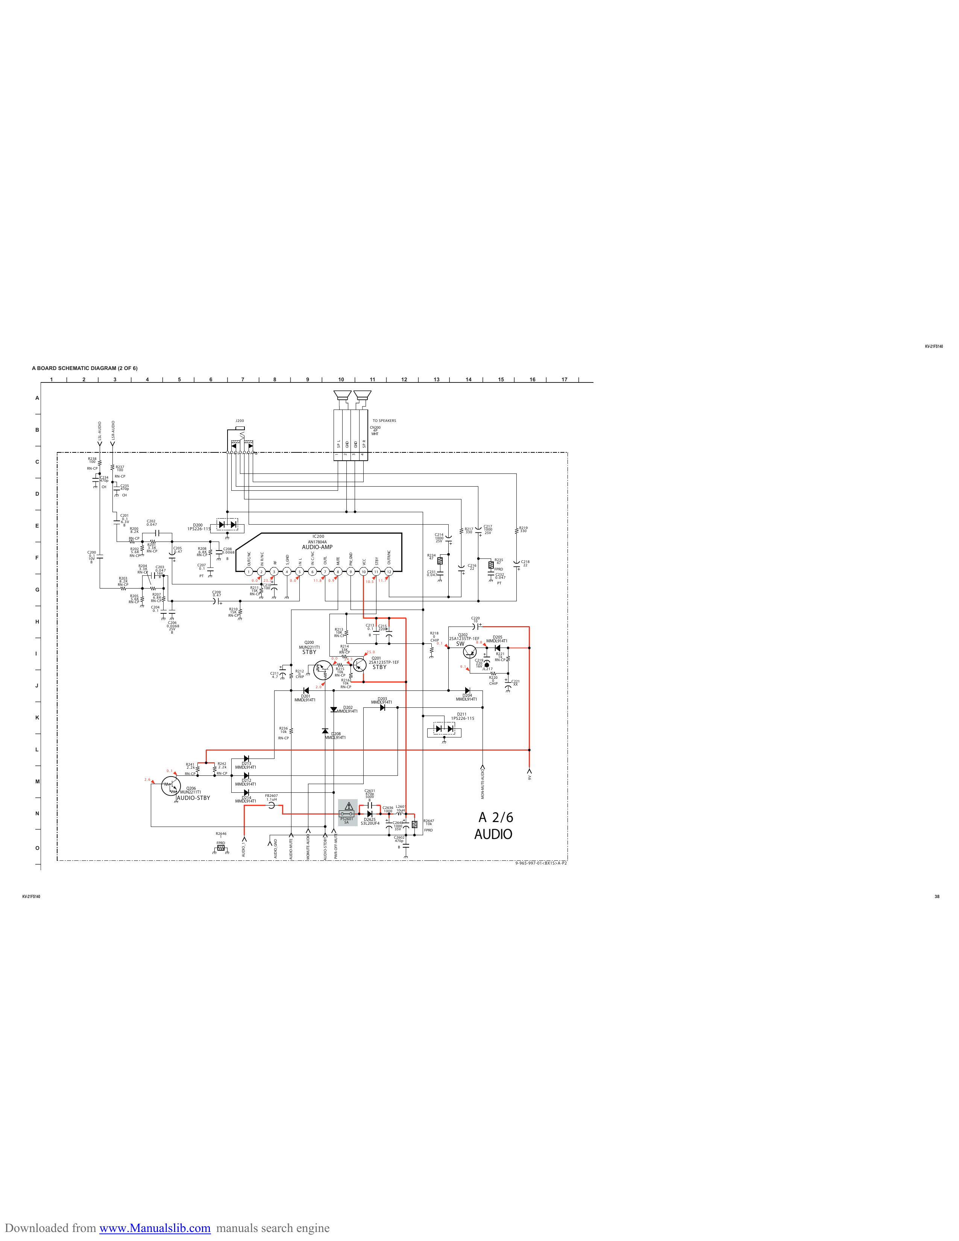
[picture p110: tv/manual/rev_s79aa/pages/img/page-38.png]
page-38


                                                                                                                                                                                                                                                                                                                                                                                                                                                                                                    KV-21FS140

        A BOARD SCHEMATIC DIAGRAM (2 OF 6)

                1   |   2          |                     3                |       4             |           5        |           6           |           7                         |                8                        |                    9                          |                                      10                  |             11            |                   12   |          13      |          14           |                     15   |           16   |     17    |

          A

          —
                                                                                                                                                    J200                                                                                                                                                                                                  TO SPEAKERS

                                    LSL-AUDIO        LSR-AUDIO
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
                                                                                   R201
                                                                          R202      3.3K                  C205            R208           C208                                                                                                 AUDIO-AMP
                                                                                   RN-CP                  0.47

                                                                                                                                                                                                                                                                                                                                                                        OUTR/NC
                            C200                                           5.6K                                           6.8K          0.0068
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
