nrzimmer/retro-crt/tv/manual/rev_s79aa/pages/page-39.md

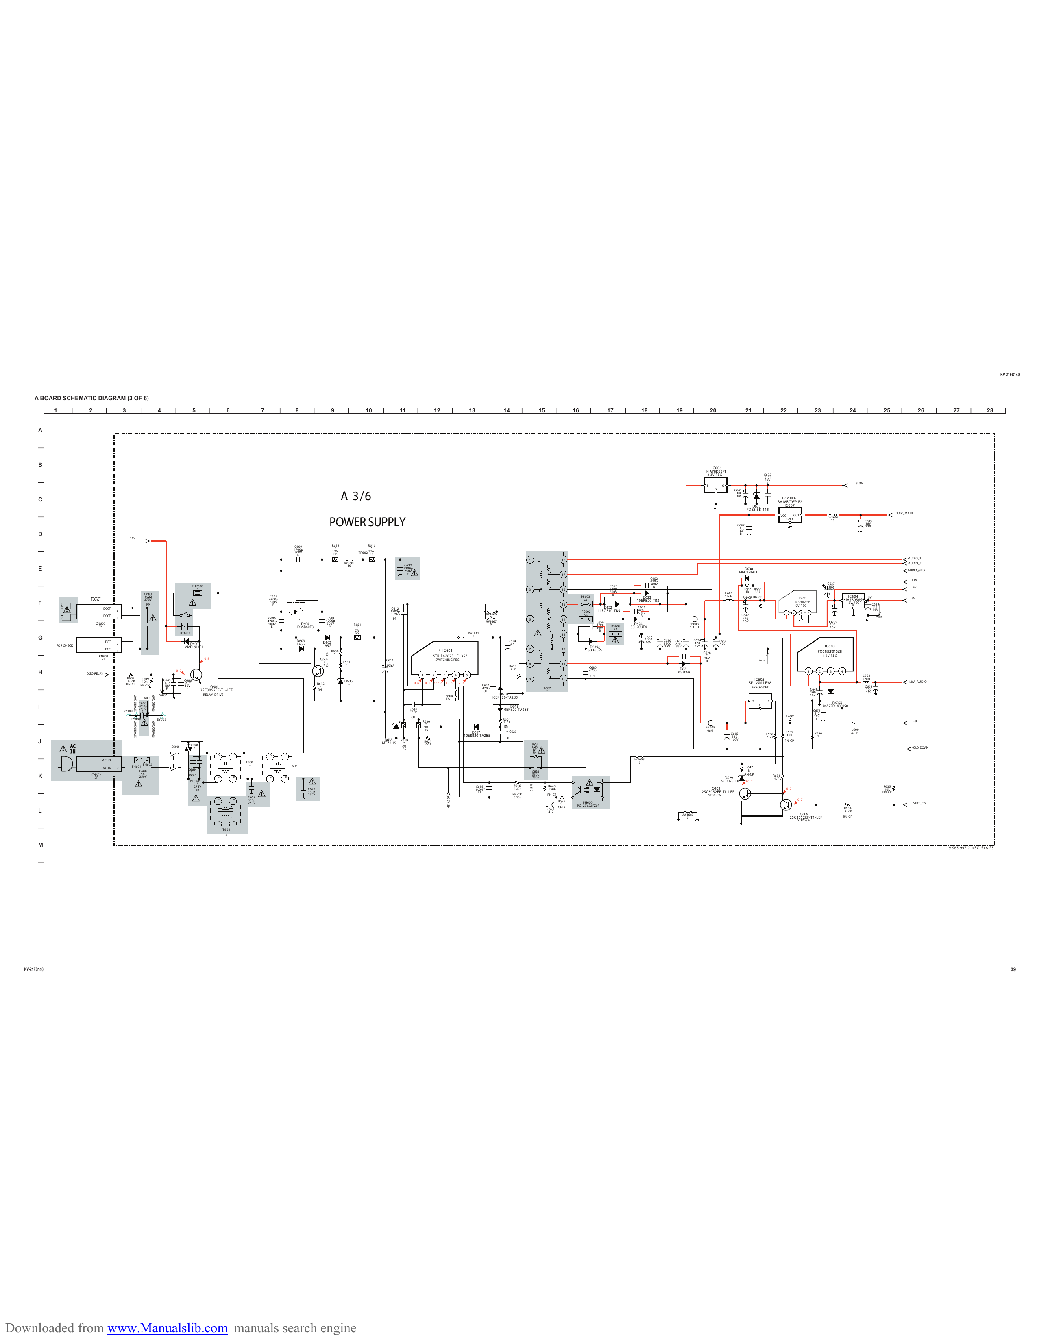
[picture p111: tv/manual/rev_s79aa/pages/img/page-39.png]
page-39


                                                                                                                                                                                                                                                                                                                                                                                                                                                                                                                                                                                                                                                                                                                  KV-21FS140

        A BOARD SCHEMATIC DIAGRAM (3 OF 6)

                1       |    2           |         3                    |                      4            |             5           |          6       |          7           |         8           |               9        |           10     |          11             |              12                 |                  13           |        14             |          15          |          16       |               17       |        18             |          19        |              20             |             21            |            22               |              23               |          24           |               25        |              26   |     27      |       28       |

          A

          —

          B                                                                                                                                                                                                                                                                                                                                                                                                                                                                                          IC606
                                                                                                                                                                                                                                                                                                                                                                                                                                                                                                  KIA78D33P1
                                                                                                                                                                                                                                                                                                                                                                                                                                                                                                  3.3V REG                                       C672
                                                                                                                                                                                                                                                                                                                                                                                                                                                                                                                                                 0.01
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
