nrzimmer/retro-crt/tv/manual/rev_s79aa/pages/img/page-41.png

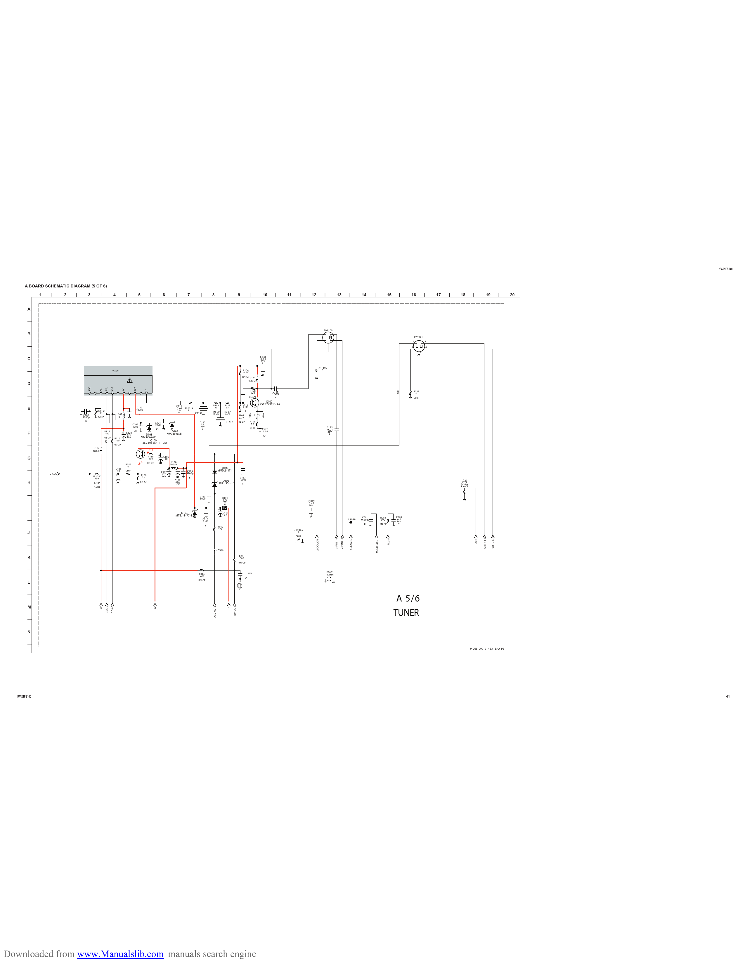
tv/manual/rev_s79aa/pages/img/page-41.png
