nrzimmer/retro-crt/tv/manual/rev_s79aa/pages/img/page-43.png

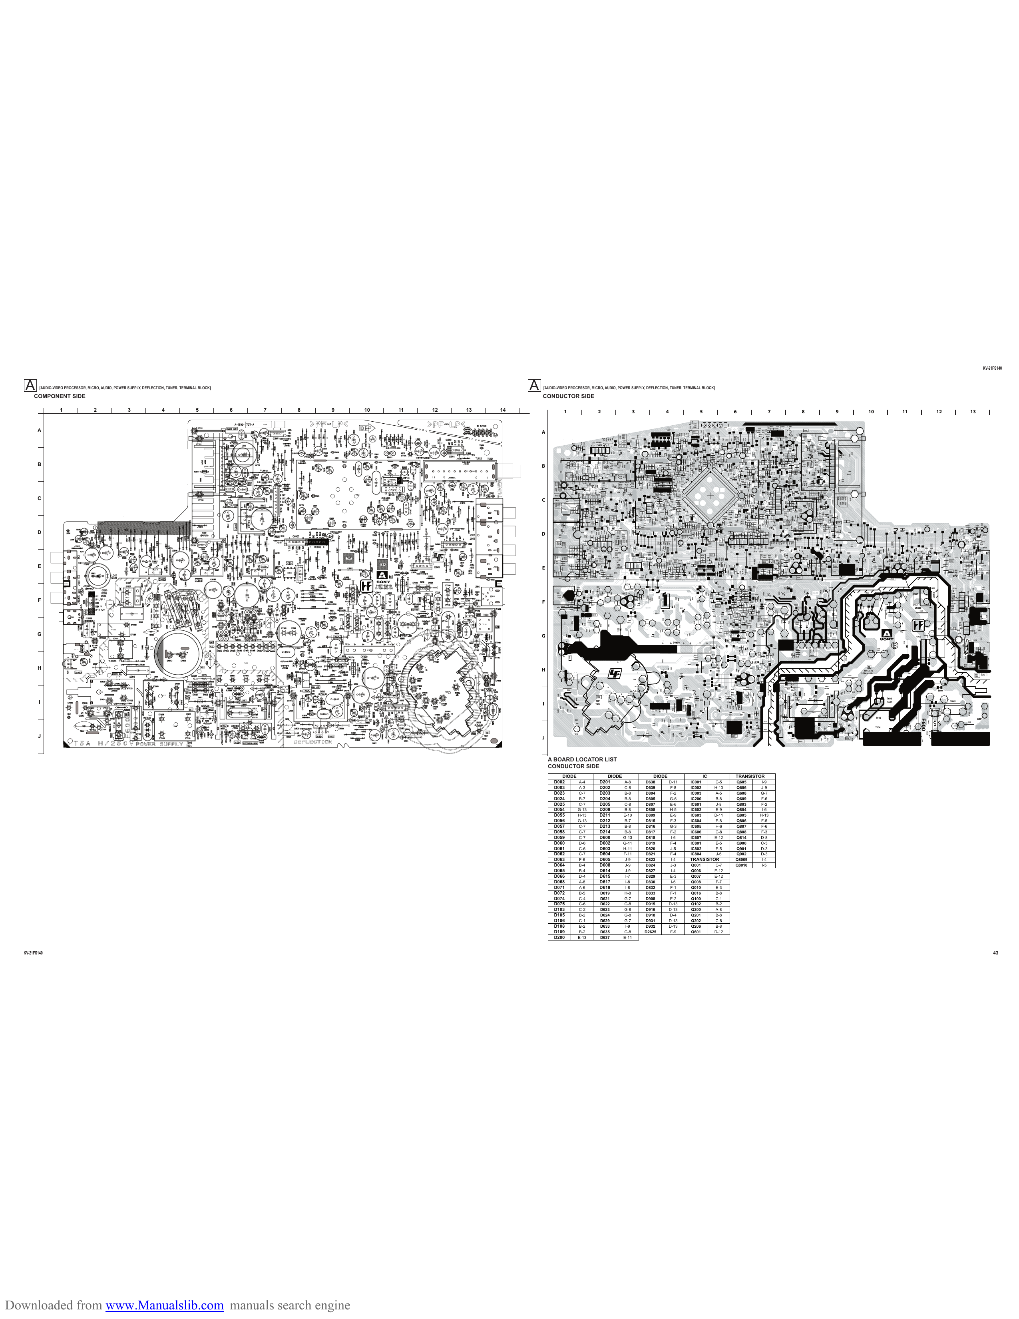
tv/manual/rev_s79aa/pages/img/page-43.png
