nrzimmer/retro-crt/tv/mod_rgb/rgb_mod.kicad_sch

## KiCad design tv/mod_rgb/rgb_mod.kicad_sch (2026-05-22)

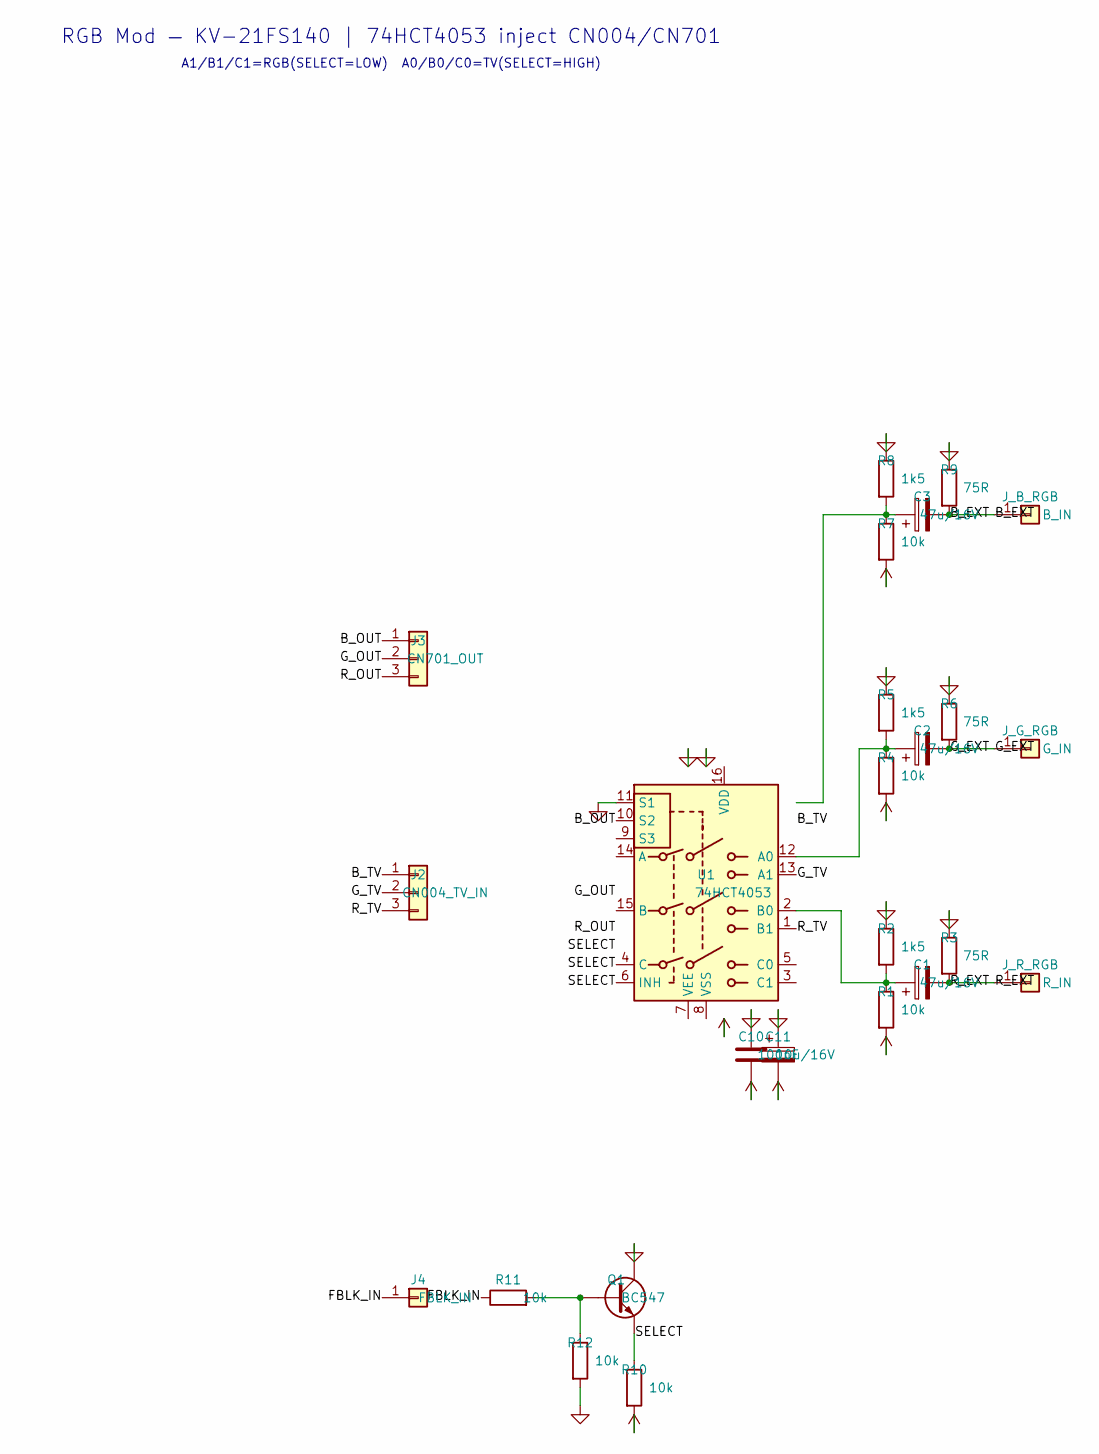
[picture p127: schematic rgb_mod.kicad_sch]

Parts:
C1, C2, C3: 47u/16V
C10: 100nF
C11: 10u/16V
J2: CN004_TV_IN
J3: CN701_OUT
J4: FBLK_IN
J_B_RGB: B_IN
J_G_RGB: G_IN
J_R_RGB: R_IN
Q1: BC547
R1, R4, R7, R10, R11, R12: 10k
R2, R5, R8: 1k5
R3, R6, R9: 75R
U1: 74HCT4053

Connections:
+5V: C10.2, C11.2, R1.2, R4.2, R7.2, R10.2
B_EXT: C3.2, J_B_RGB.1, R9.2
B_OUT: J3.1, U1.10 (S2)
B_TV: J2.1
FBLK_IN: J4.1, R11.1
GND: C10.1, C11.1, Q1.C, R2.1, R3.1, R5.1, R6.1, R8.1, R9.1, R12.2, U1.11 (S1)
G_EXT: C2.2, J_G_RGB.1, R6.2
G_OUT: J3.2
G_TV: J2.2, U1.13 (A1)
unnamed: C1.1, R1.1, R2.2, U1.2 (B0)
unnamed: C2.1, R4.1, R5.2, U1.12 (A0)
unnamed: C3.1, R7.1, R8.2
unnamed: Q1.B, R11.2, R12.1
R_EXT: C1.2, J_R_RGB.1, R3.2
R_OUT: J3.3
R_TV: J2.3, U1.1 (B1)
SELECT: Q1.E, R10.1, U1.4 (C), U1.6 (INH)

Notes on the sheet:
RGB Mod — KV-21FS140 | 74HCT4053 inject CN004/CN701
A1/B1/C1=RGB(SELECT=LOW) A0/B0/C0=TV(SELECT=HIGH)
